Noschvie/shrdzm/hardware/19-12-22 15-27-47 3607.jpg

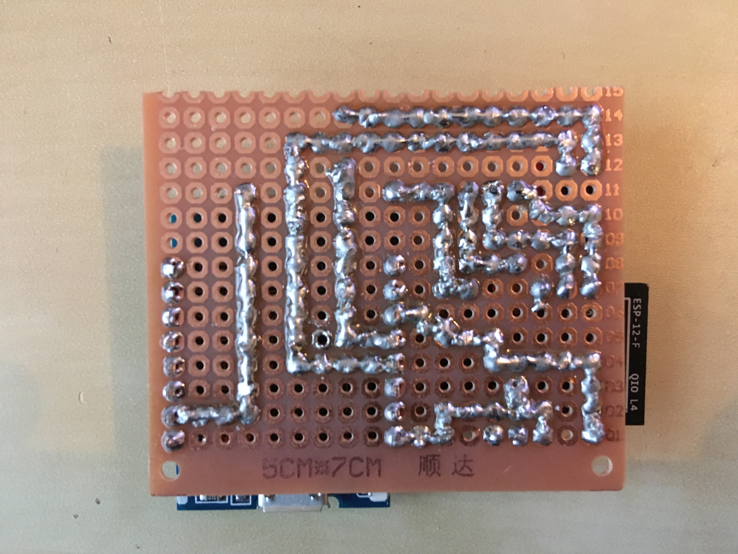
hardware/19-12-22 15-27-47 3607.jpg
