Noschvie/shrdzm/hardware/19-12-23 08-18-39 3610.jpg

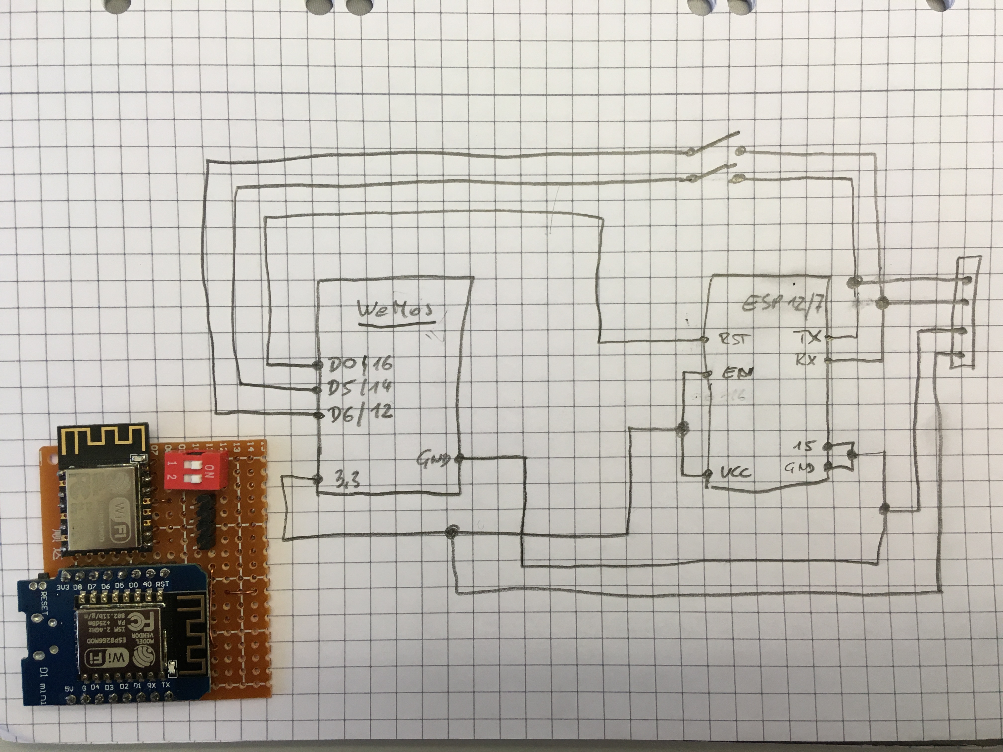
hardware/19-12-23 08-18-39 3610.jpg
