Noschvie/shrdzm/hardware/Alexa1.png

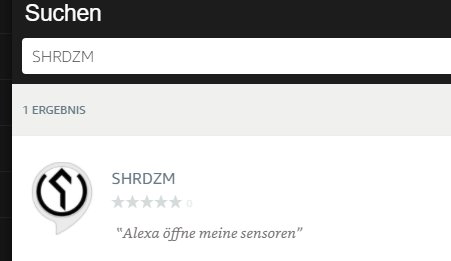
hardware/Alexa1.png
