Noschvie/shrdzm/hardware/Alexa5.png

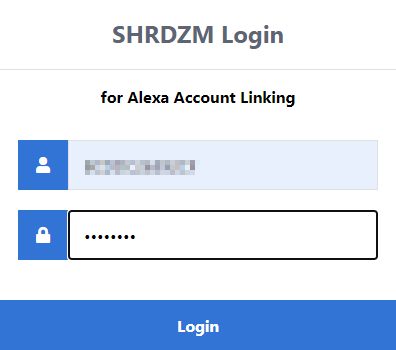
hardware/Alexa5.png
