Noschvie/shrdzm/hardware/Alexa6.png

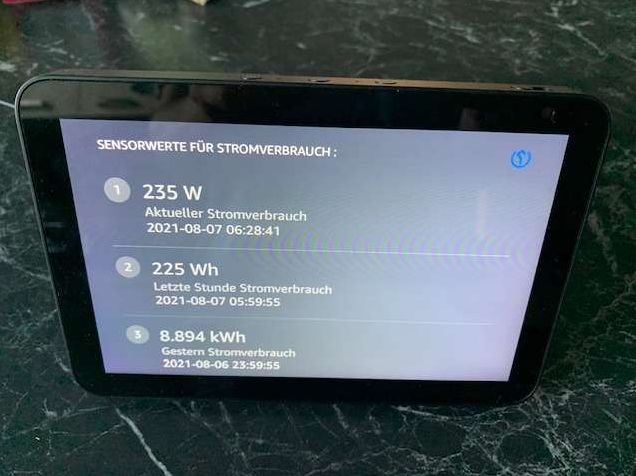
hardware/Alexa6.png
