Noschvie/shrdzm/hardware/Alexa7.png

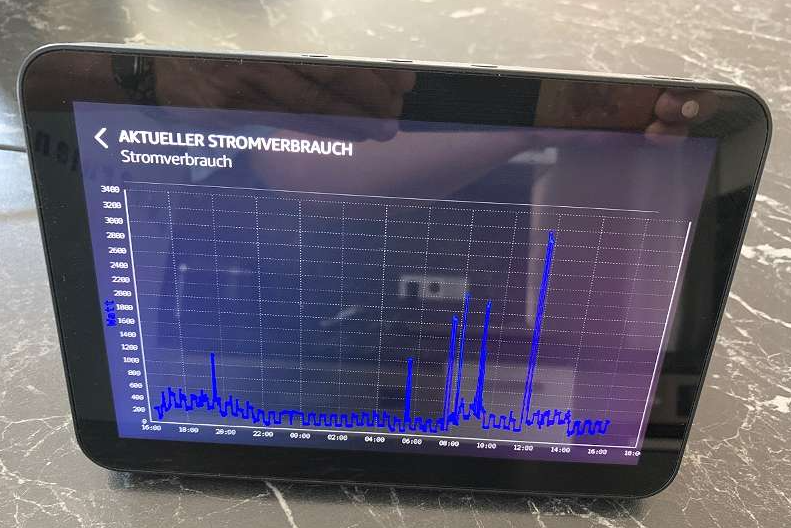
hardware/Alexa7.png
