Noschvie/shrdzm/hardware/AlexaConcept.png

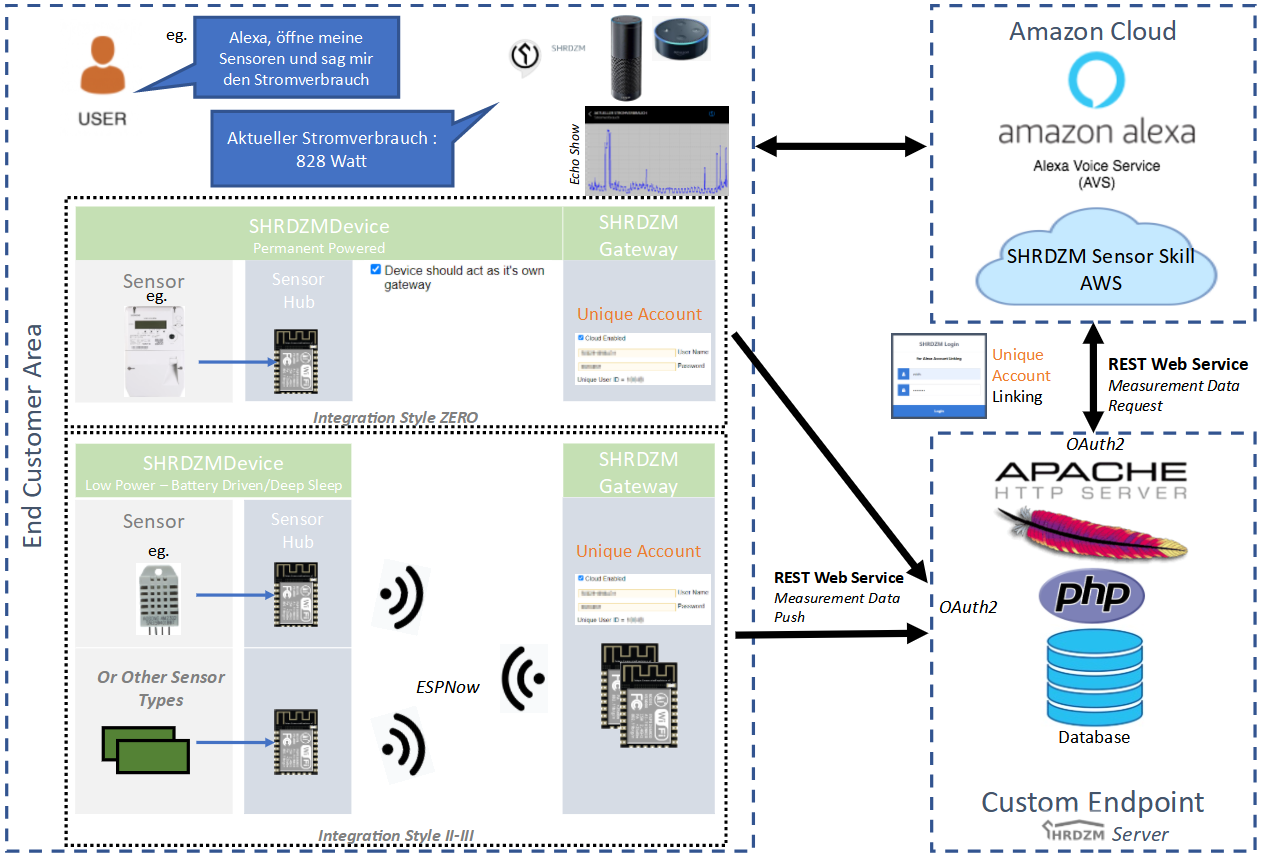
hardware/AlexaConcept.png
