Noschvie/shrdzm/hardware/BatteryCheck_1.png

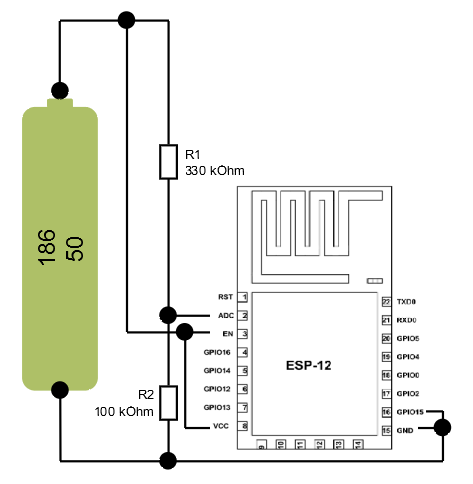
hardware/BatteryCheck_1.png
