Noschvie/shrdzm/hardware/BatteryCheck_4.png

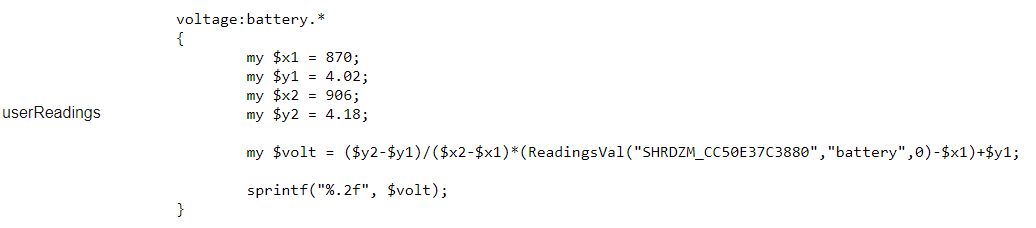
hardware/BatteryCheck_4.png
