Noschvie/shrdzm/hardware/BH1750.png

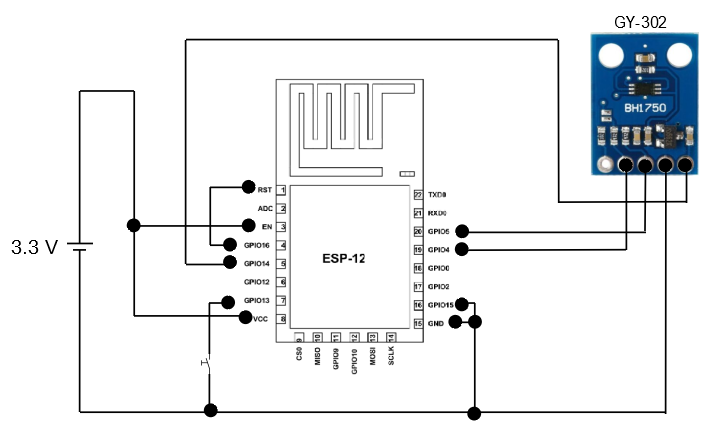
hardware/BH1750.png
