Noschvie/shrdzm/hardware/BMP280.png

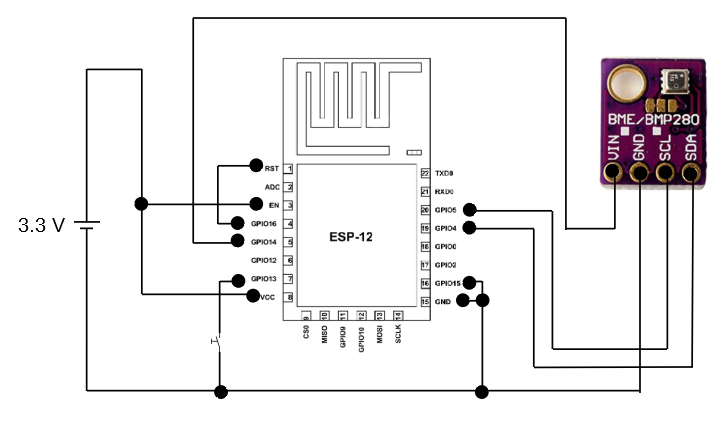
hardware/BMP280.png
