Noschvie/shrdzm/hardware/Breadboard.png

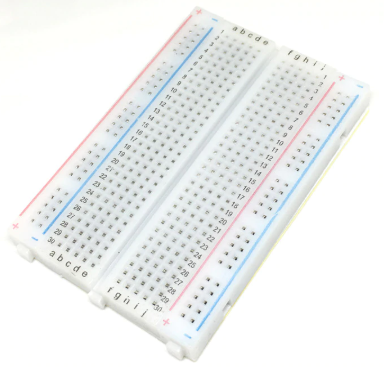
hardware/Breadboard.png
