Noschvie/shrdzm/hardware/CH340.png

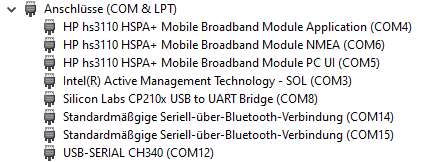
hardware/CH340.png
