Noschvie/shrdzm/hardware/Cloud1.png

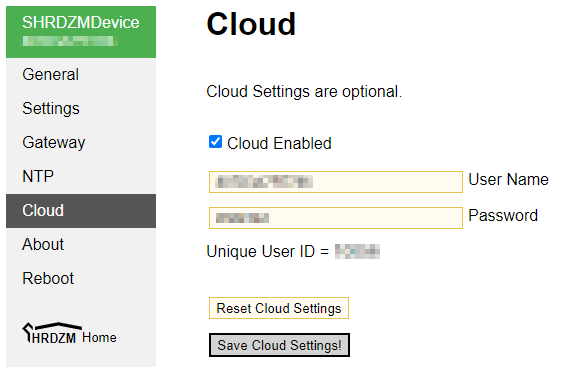
hardware/Cloud1.png
