Noschvie/shrdzm/hardware/Cloud2.png

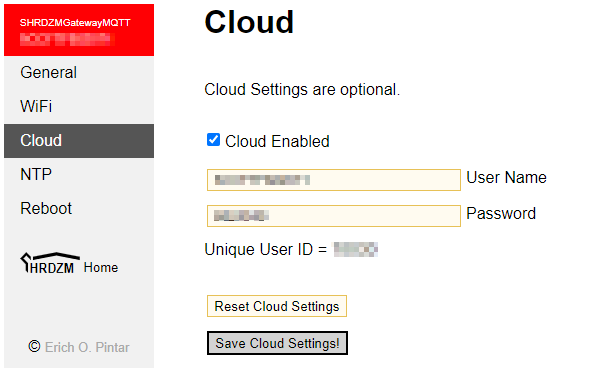
hardware/Cloud2.png
