Noschvie/shrdzm/hardware/Copyright.png

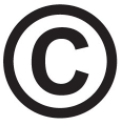
hardware/Copyright.png
