Noschvie/shrdzm/hardware/CP2102.png

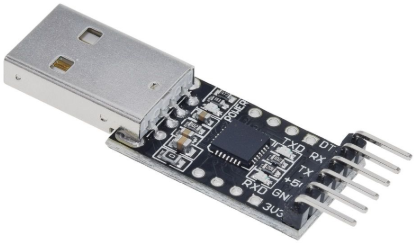
hardware/CP2102.png
