Noschvie/shrdzm/hardware/DeviceConfig.png

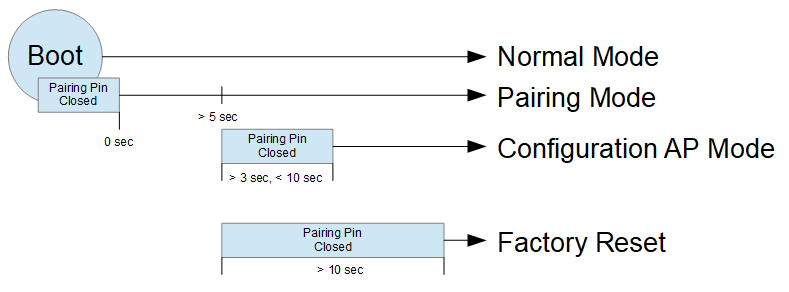
hardware/DeviceConfig.png
