Noschvie/shrdzm/hardware/DHT22.png

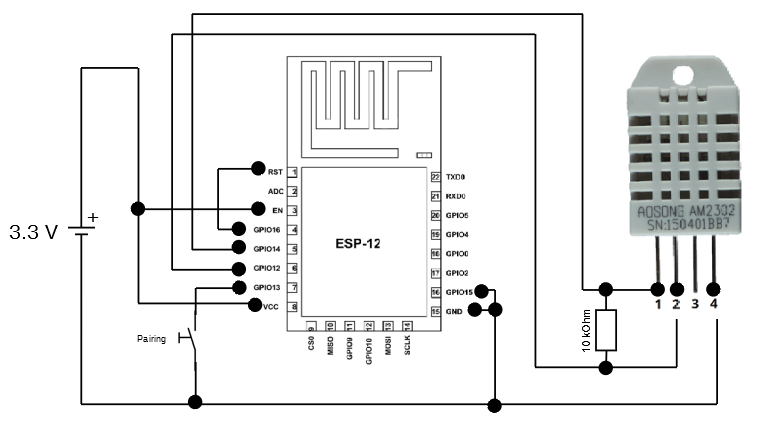
hardware/DHT22.png
