Noschvie/shrdzm/hardware/DOORSENSOR.png

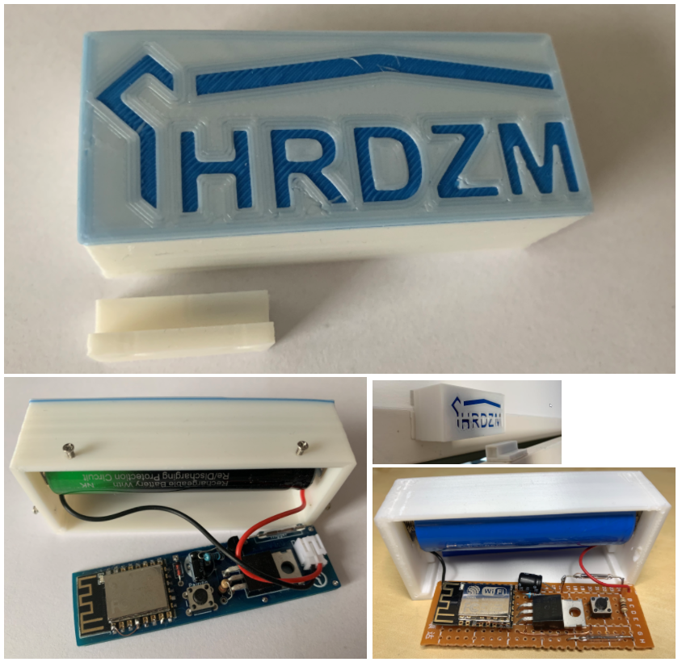
hardware/DOORSENSOR.png
