Noschvie/shrdzm/hardware/DOORSENSOR_1.png

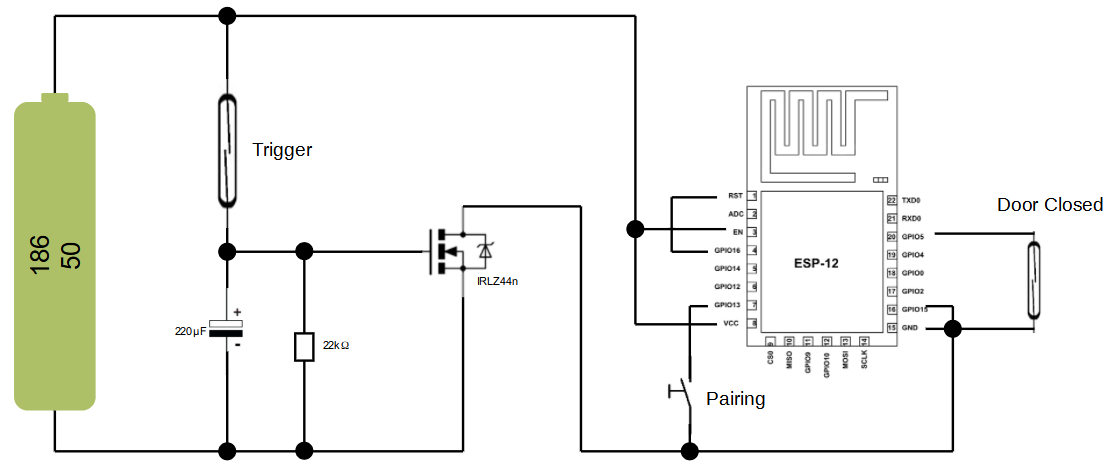
hardware/DOORSENSOR_1.png
