Noschvie/shrdzm/hardware/DOORSENSOR_9V_Cover.png

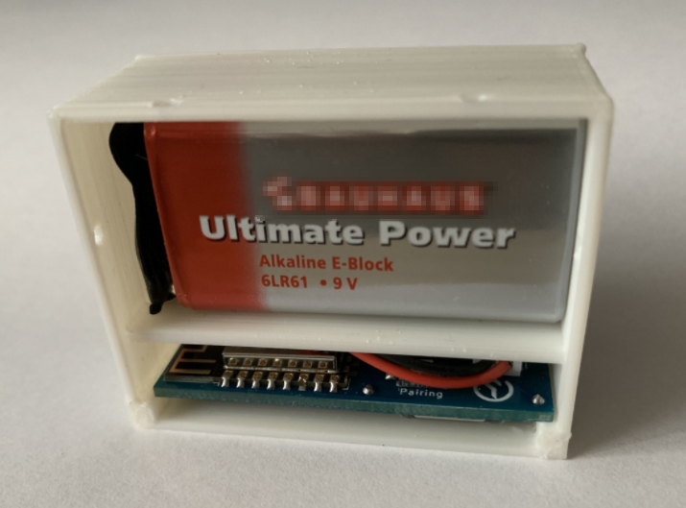
hardware/DOORSENSOR_9V_Cover.png
