Noschvie/shrdzm/hardware/DOORSENSOR_Closed.png

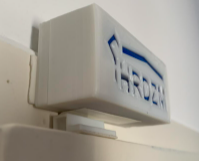
hardware/DOORSENSOR_Closed.png
