Noschvie/shrdzm/hardware/DOORSENSOR_Enhanced_Circuit.png

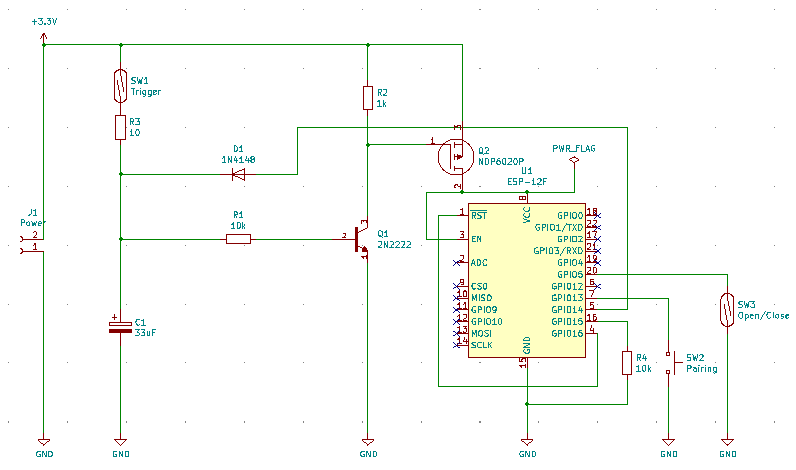
hardware/DOORSENSOR_Enhanced_Circuit.png
