Noschvie/shrdzm/hardware/DOORSENSOR_Enhanced_Cover.png

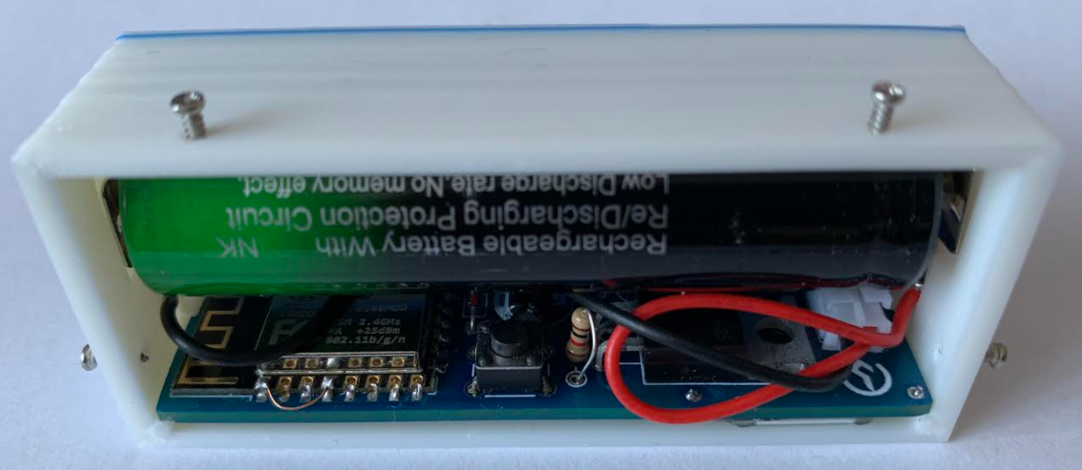
hardware/DOORSENSOR_Enhanced_Cover.png
