Noschvie/shrdzm/hardware/DOORSENSOR_Enhanced_PCB.png

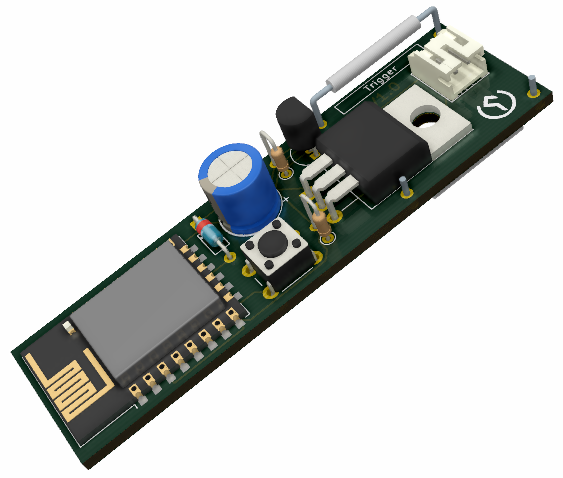
hardware/DOORSENSOR_Enhanced_PCB.png
