Noschvie/shrdzm/hardware/DOORSENSOR_FHEM.png

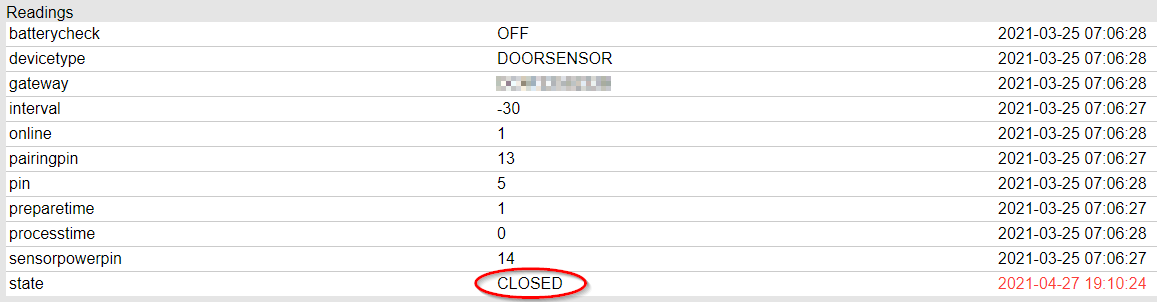
hardware/DOORSENSOR_FHEM.png
