Noschvie/shrdzm/hardware/DOORSENSOR_Open.png

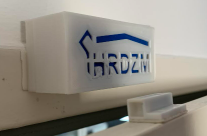
hardware/DOORSENSOR_Open.png
