Noschvie/shrdzm/hardware/DOORSENSOR_PCB.png

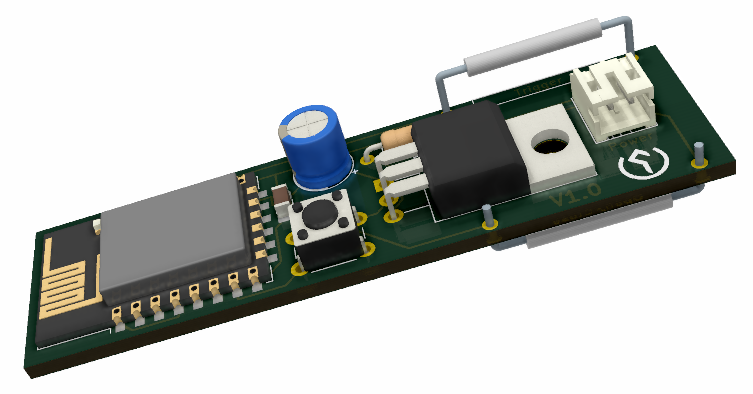
hardware/DOORSENSOR_PCB.png
