Noschvie/shrdzm/hardware/DOORSENSOR_Principle.png

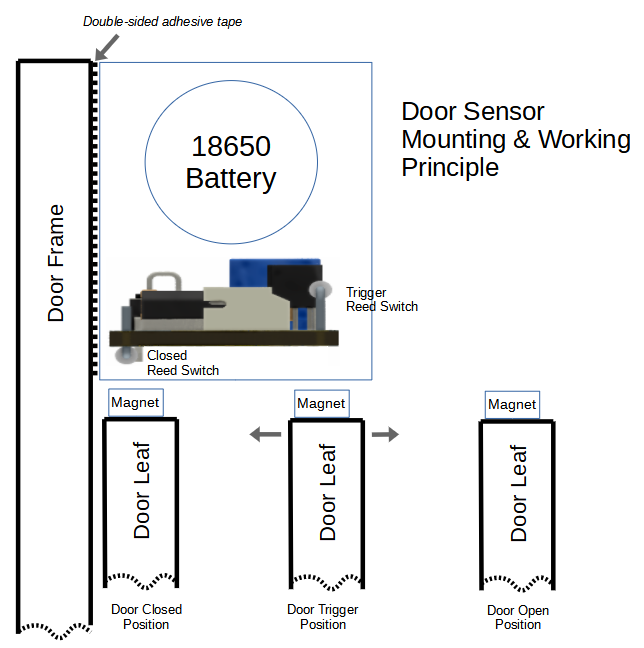
hardware/DOORSENSOR_Principle.png
