Noschvie/shrdzm/hardware/DOORSENSOR_Simple_9V_Circuit.png

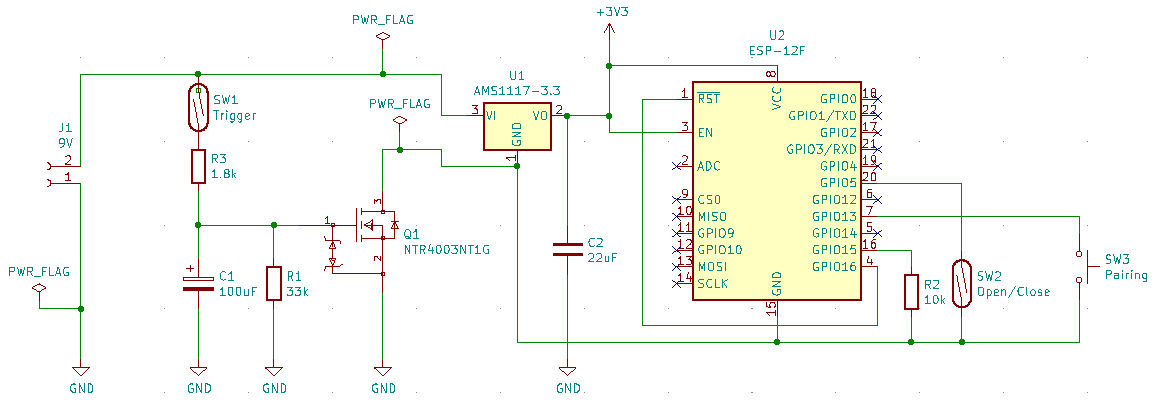
hardware/DOORSENSOR_Simple_9V_Circuit.png
