Noschvie/shrdzm/hardware/DOORSENSOR_Simple_9V_PCB.png

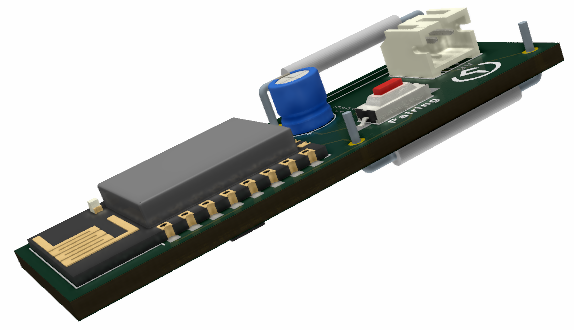
hardware/DOORSENSOR_Simple_9V_PCB.png
