Noschvie/shrdzm/hardware/DOORSENSOR_Trigger.png

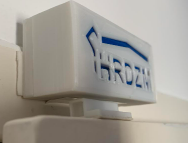
hardware/DOORSENSOR_Trigger.png
