Noschvie/shrdzm/hardware/DOORSENSOR_Unmounted.png

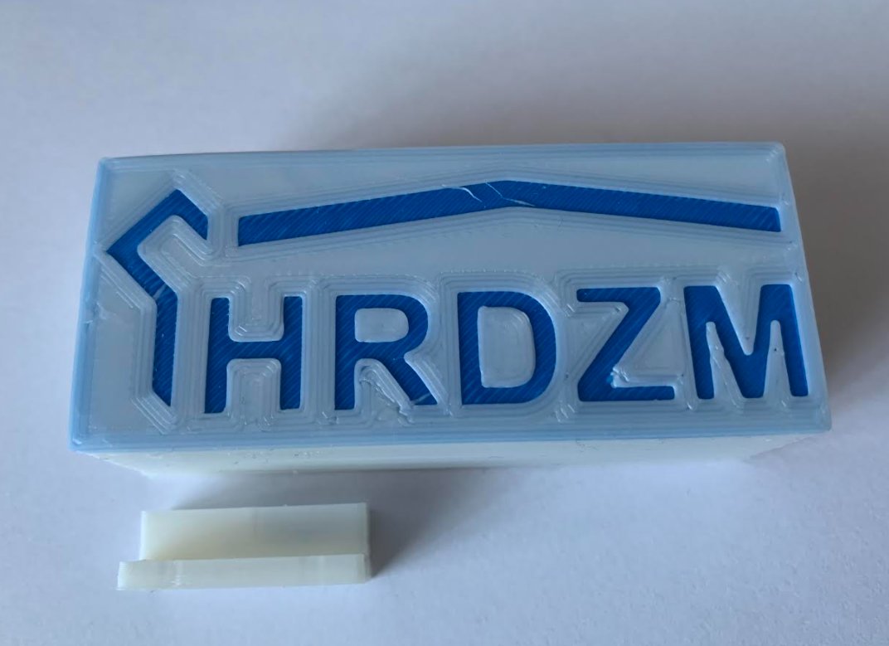
hardware/DOORSENSOR_Unmounted.png
