Noschvie/shrdzm/hardware/DS18B20.png

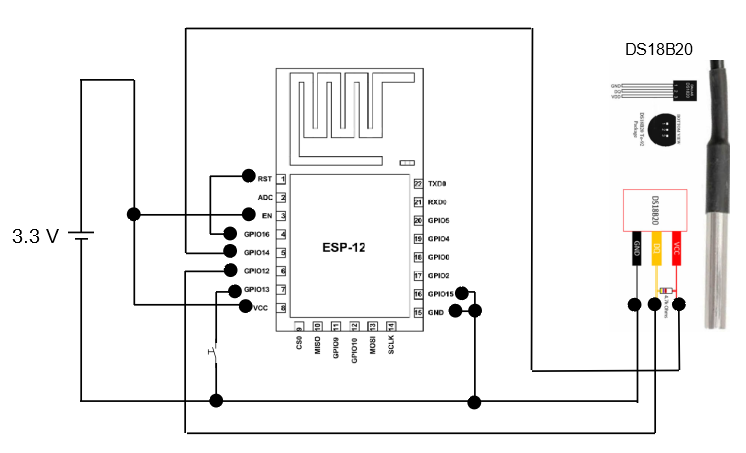
hardware/DS18B20.png
