Noschvie/shrdzm/hardware/ESP12.png

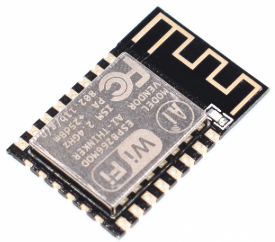
hardware/ESP12.png
