Noschvie/shrdzm/hardware/ESP8266Flasher_1.png

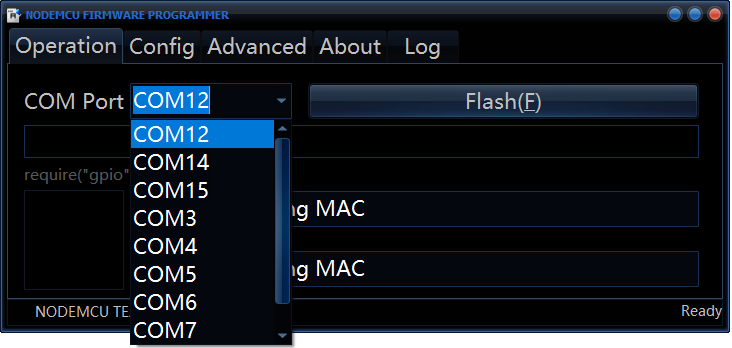
hardware/ESP8266Flasher_1.png
