Noschvie/shrdzm/hardware/ESP8266Flasher_2.png

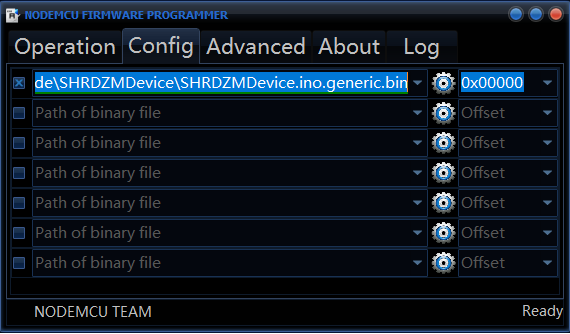
hardware/ESP8266Flasher_2.png
