Noschvie/shrdzm/hardware/ESP8266Flasher_2_1.png

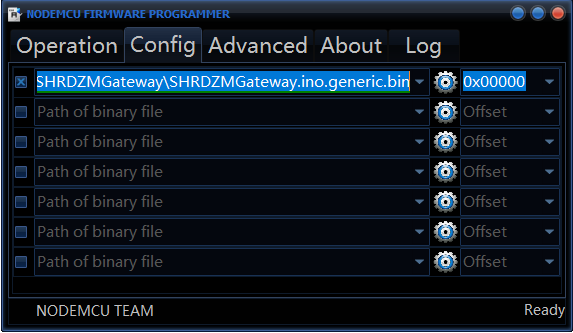
hardware/ESP8266Flasher_2_1.png
