Noschvie/shrdzm/hardware/ESP8266Flasher_3.png

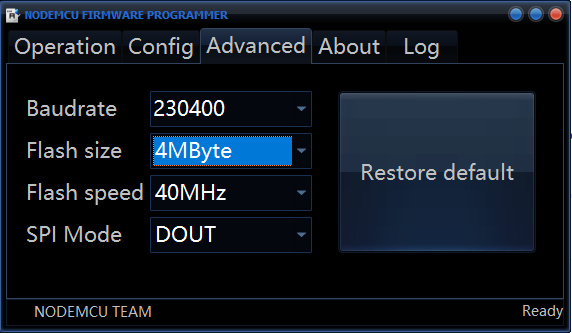
hardware/ESP8266Flasher_3.png
