Noschvie/shrdzm/hardware/ESP8266Flasher_3_1.png

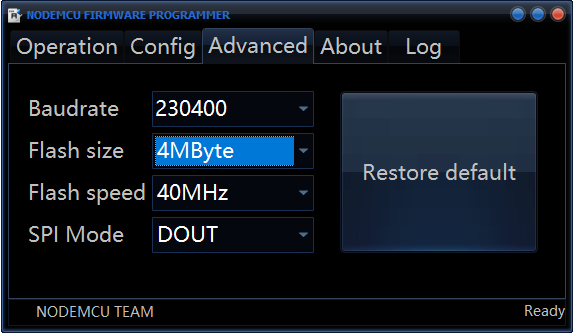
hardware/ESP8266Flasher_3_1.png
