Noschvie/shrdzm/hardware/ESP8266Flasher_4.png

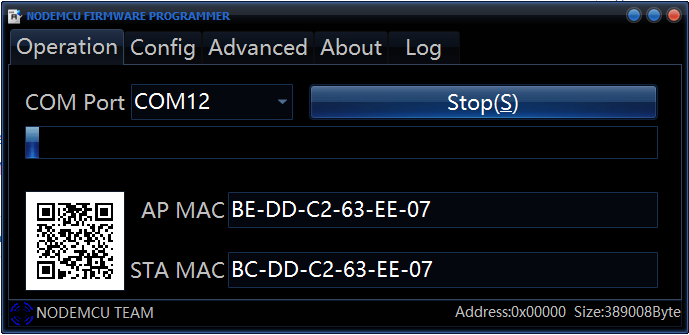
hardware/ESP8266Flasher_4.png
