Noschvie/shrdzm/hardware/ESP8266Flasher_5.png

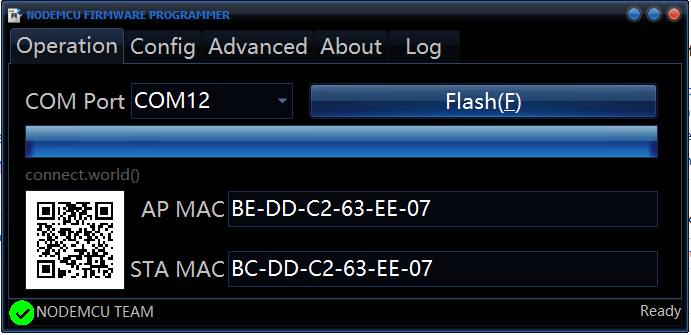
hardware/ESP8266Flasher_5.png
