Noschvie/shrdzm/hardware/ESP-07.png

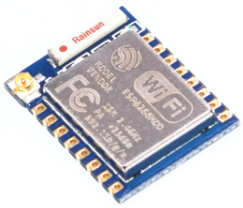
hardware/ESP-07.png
