Noschvie/shrdzm/hardware/ESPWLANGatewayAntennaHolder.png

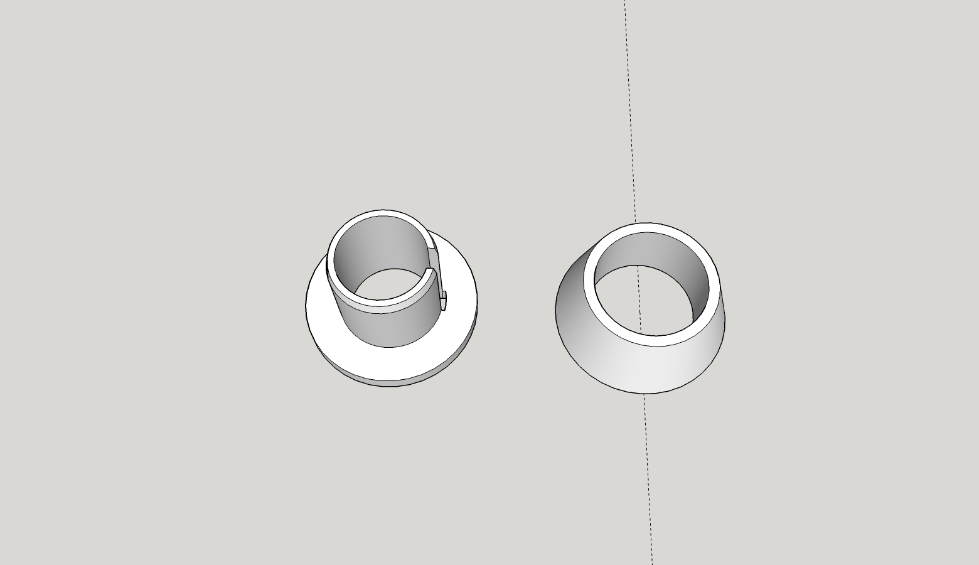
hardware/ESPWLANGatewayAntennaHolder.png
