Noschvie/shrdzm/hardware/ESPWLANGatewayBottom.png

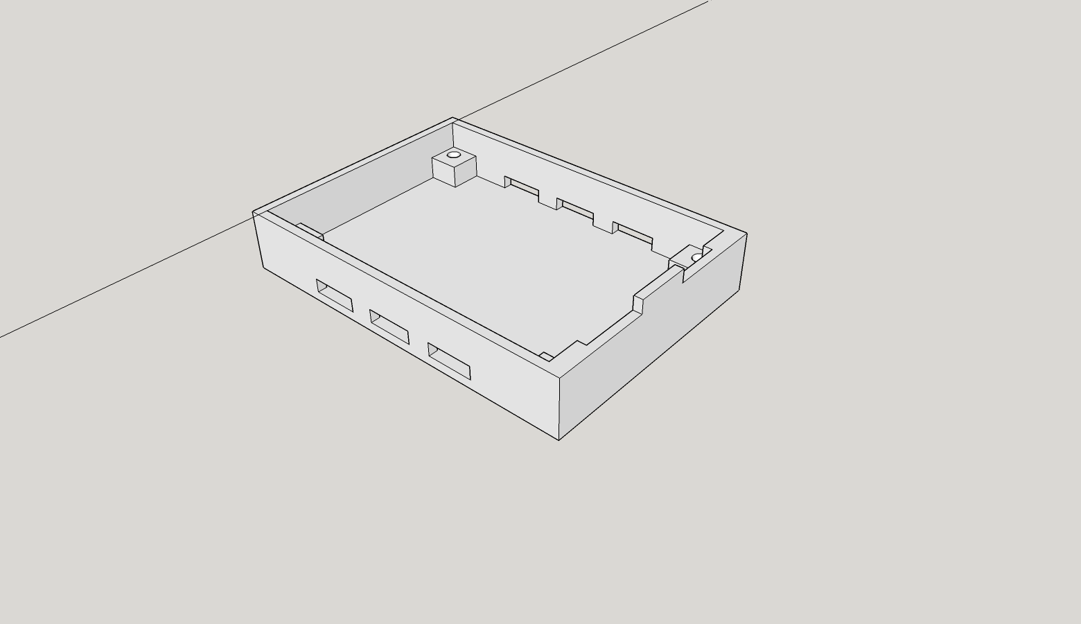
hardware/ESPWLANGatewayBottom.png
