Noschvie/shrdzm/hardware/ESPWLANGatewayTop.png

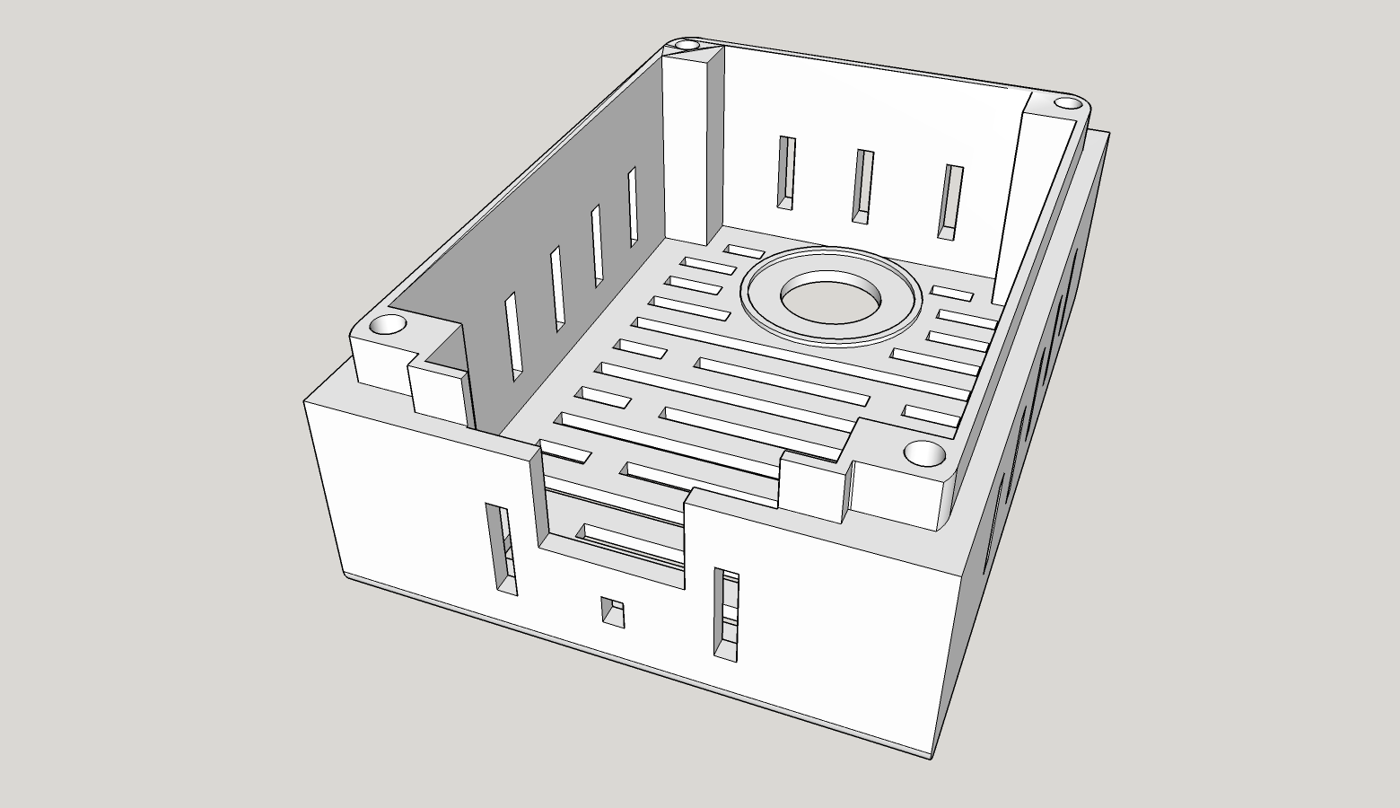
hardware/ESPWLANGatewayTop.png
