Noschvie/shrdzm/hardware/FHEM_definedMQTT.png

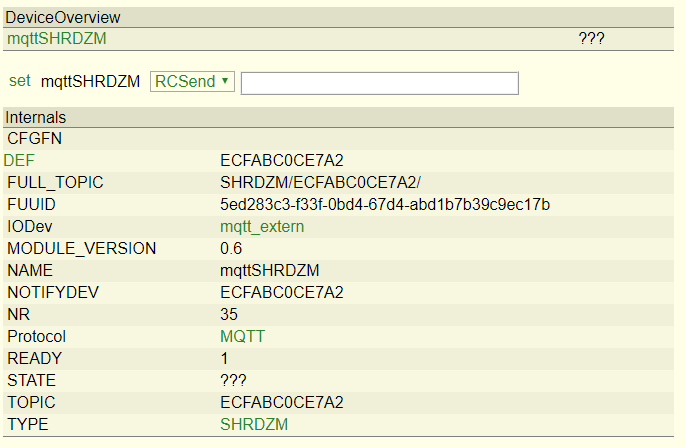
hardware/FHEM_definedMQTT.png
