Noschvie/shrdzm/hardware/FHEM_definedSerial.png

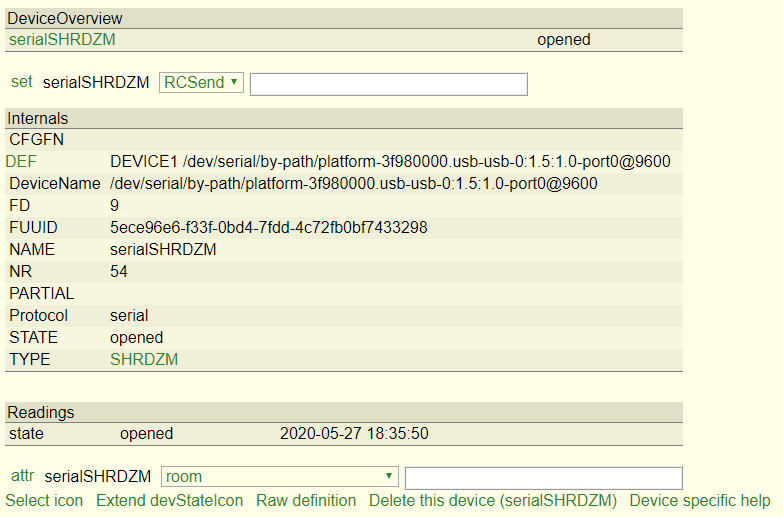
hardware/FHEM_definedSerial.png
