Noschvie/shrdzm/hardware/FHEM_DHT22_1.PNG

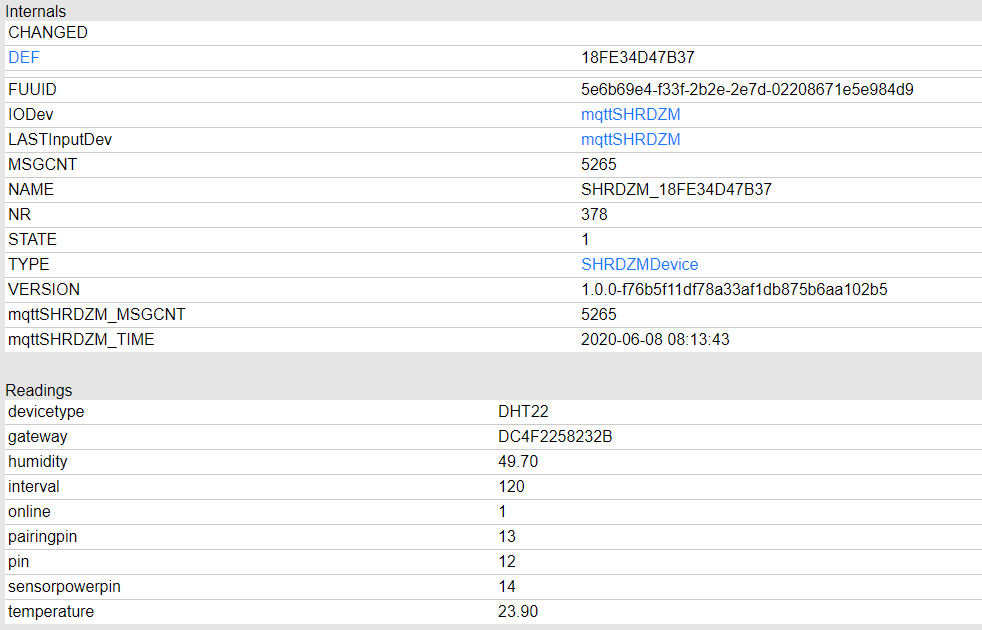
hardware/FHEM_DHT22_1.PNG
