Noschvie/shrdzm/hardware/FHEM_DIGITALGROUNDopen.png

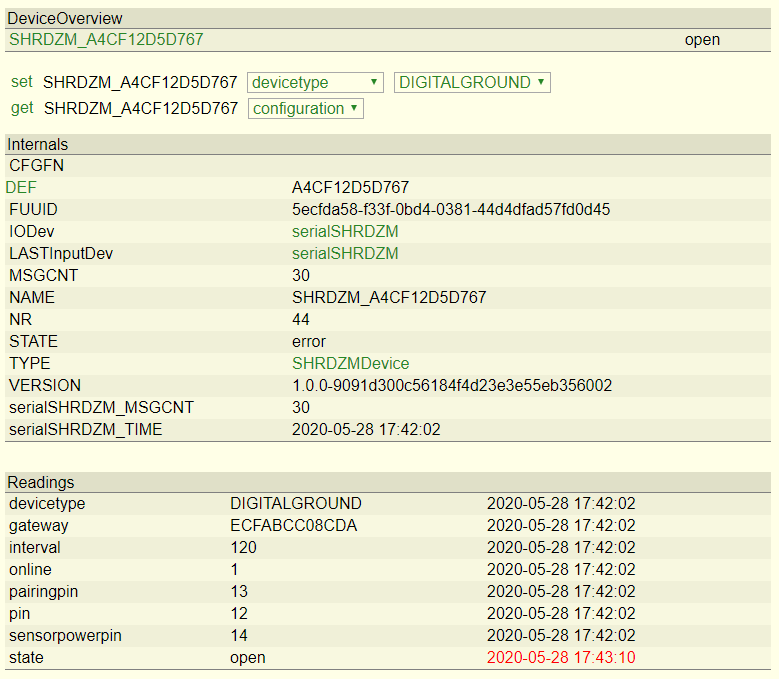
hardware/FHEM_DIGITALGROUNDopen.png
