Noschvie/shrdzm/hardware/FHEM_HTU21D_1.PNG

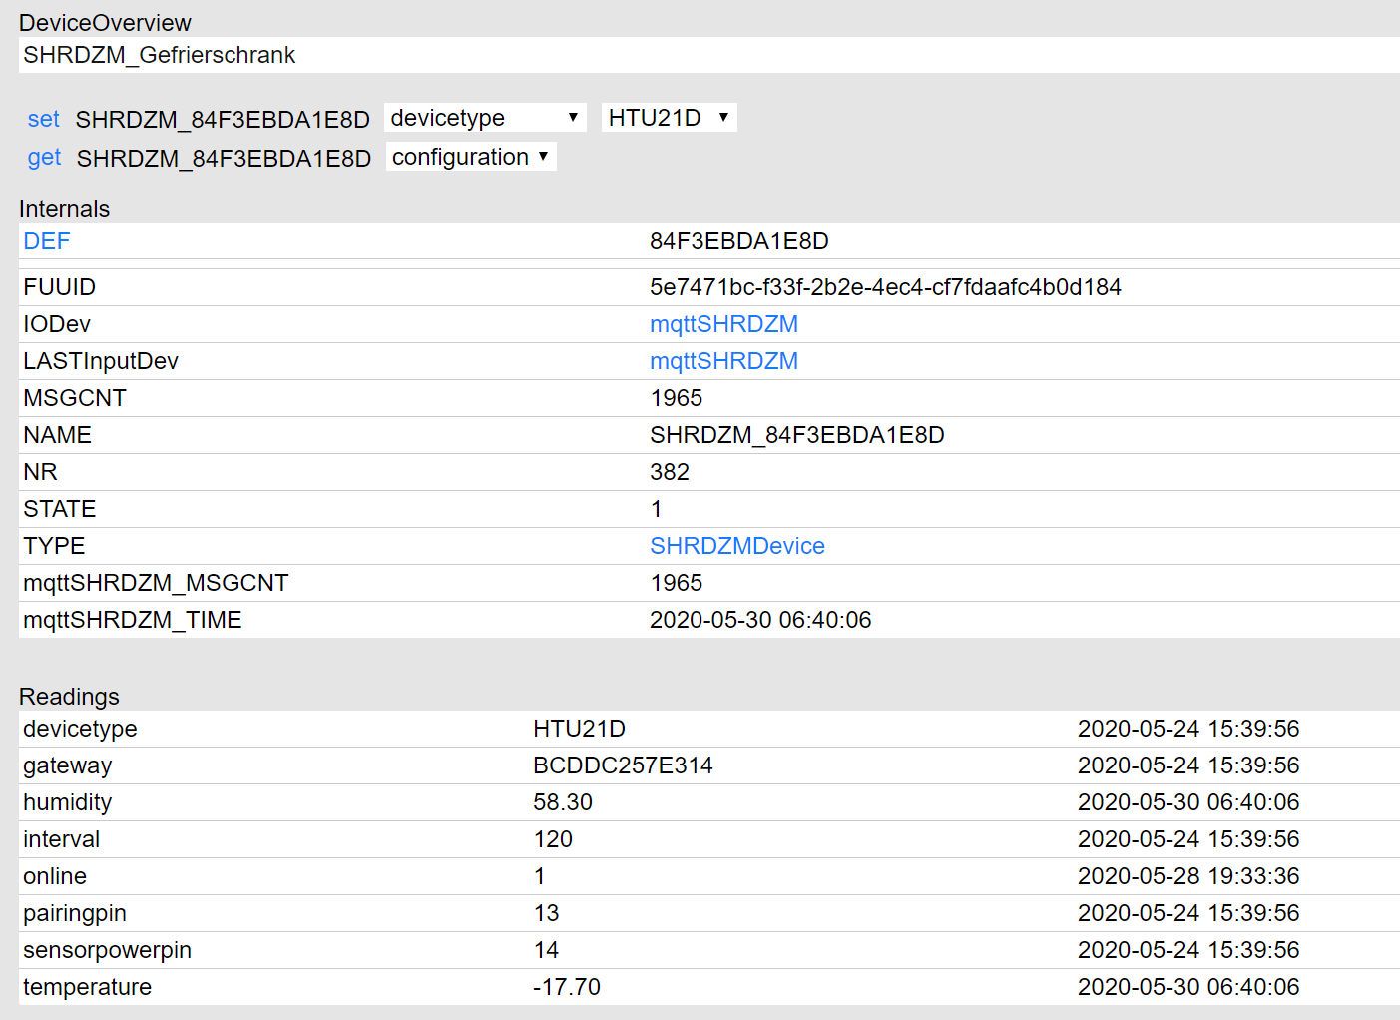
hardware/FHEM_HTU21D_1.PNG
