Noschvie/shrdzm/hardware/FHEM_HTU21D_2.PNG

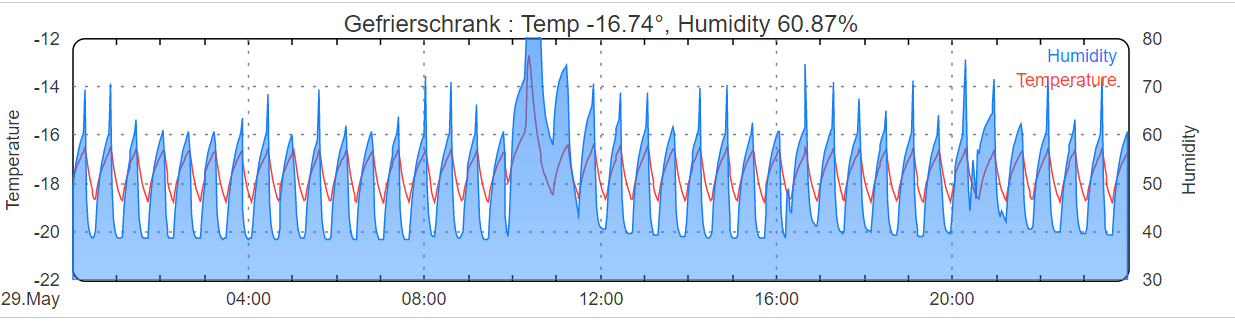
hardware/FHEM_HTU21D_2.PNG
