Noschvie/shrdzm/hardware/FHEM_IM350_2.png

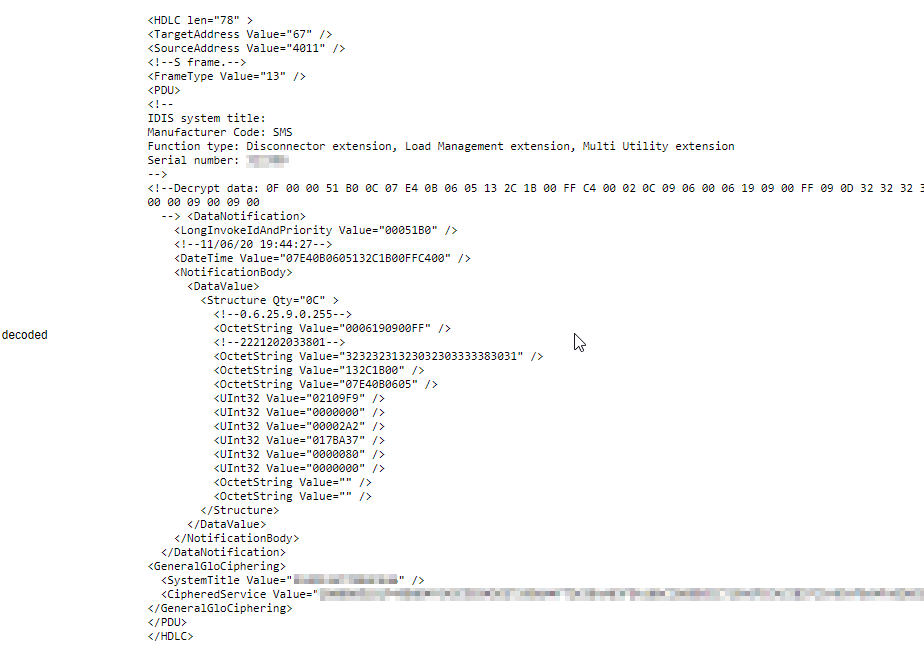
hardware/FHEM_IM350_2.png
