Noschvie/shrdzm/hardware/FHEM_IM350_3.png

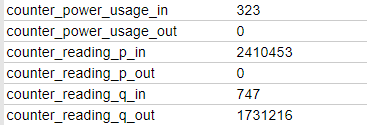
hardware/FHEM_IM350_3.png
