Noschvie/shrdzm/hardware/FHEM_IM350_4.png

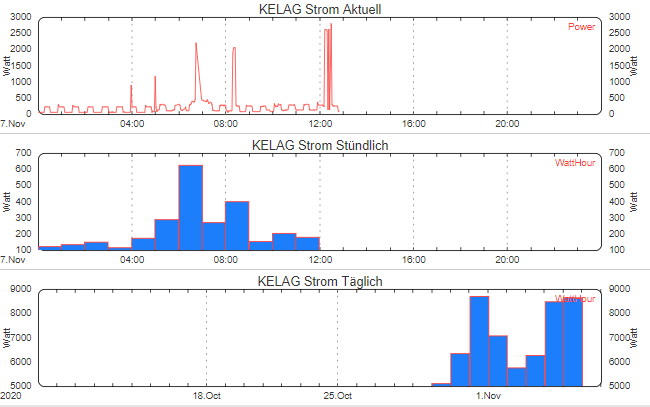
hardware/FHEM_IM350_4.png
