Noschvie/shrdzm/hardware/FHEM_PairedDone.png

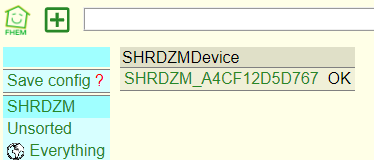
hardware/FHEM_PairedDone.png
