Noschvie/shrdzm/hardware/FHEM_SelectDIGITALGROUND.png

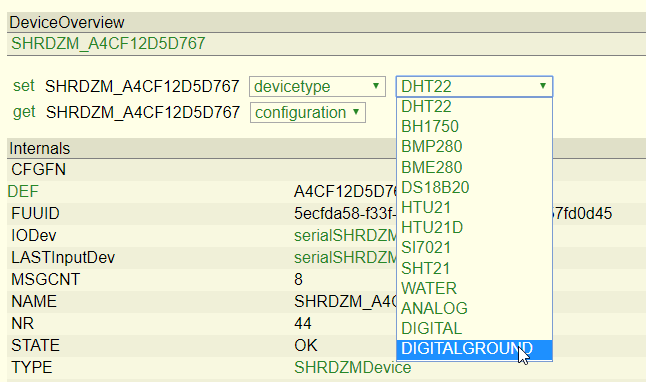
hardware/FHEM_SelectDIGITALGROUND.png
