Noschvie/shrdzm/hardware/FHEM_Sensors1.jpg

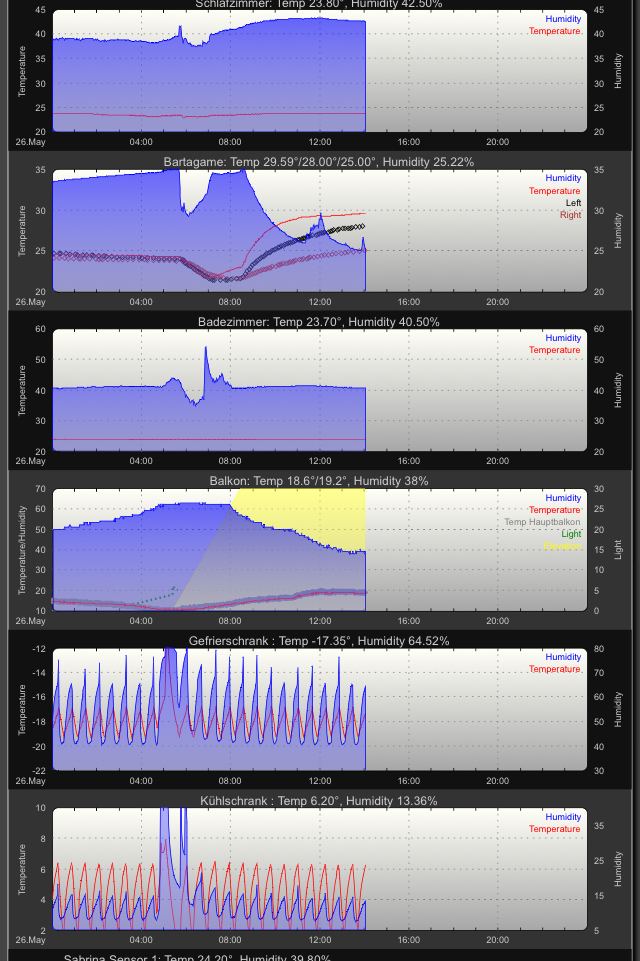
hardware/FHEM_Sensors1.jpg
