Noschvie/shrdzm/hardware/GatewaySettings.png

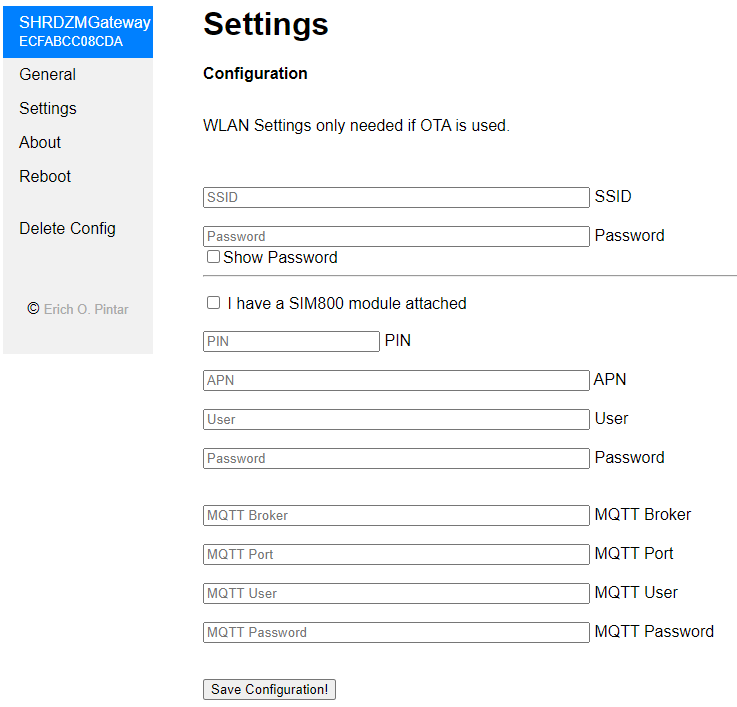
hardware/GatewaySettings.png
