Noschvie/shrdzm/hardware/GatewaySSID.png

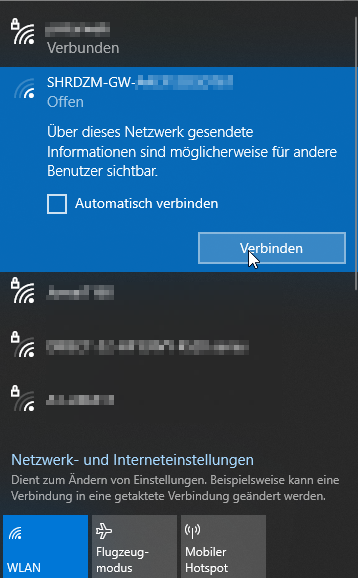
hardware/GatewaySSID.png
