Noschvie/shrdzm/hardware/Grafana_IM350.png

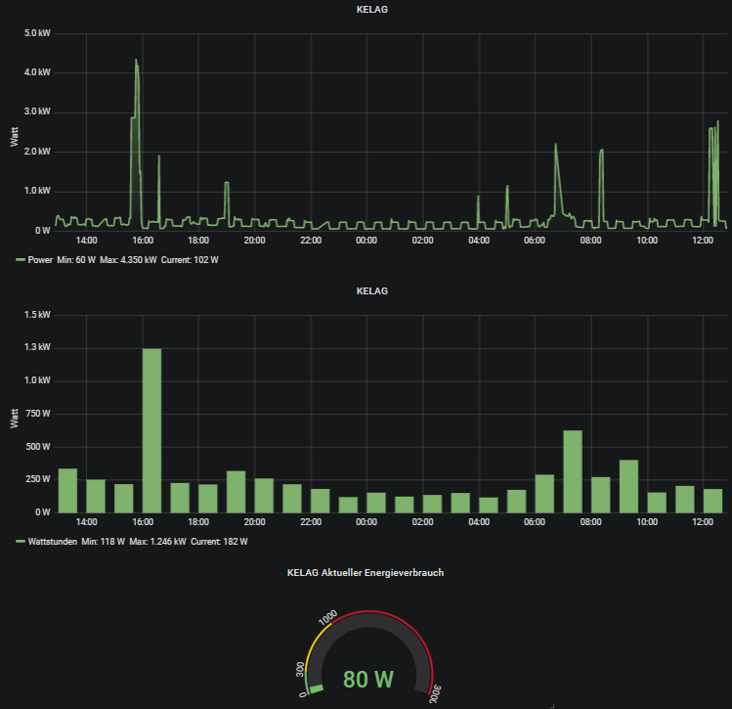
hardware/Grafana_IM350.png
