Noschvie/shrdzm/hardware/IM350.png

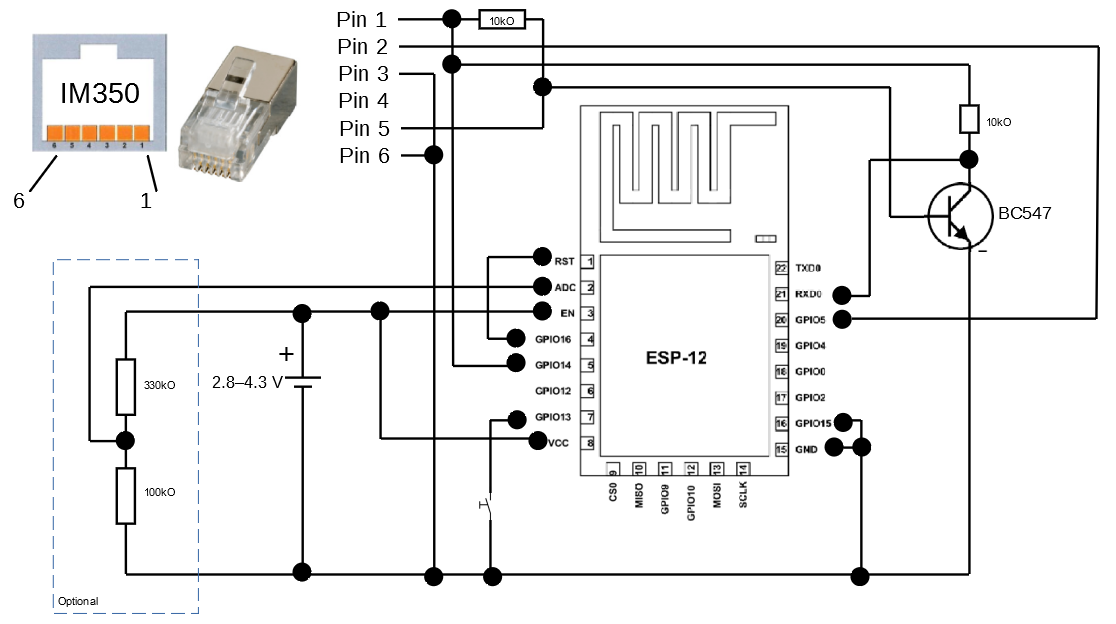
hardware/IM350.png
