Noschvie/shrdzm/hardware/IM350_1_Battery.png

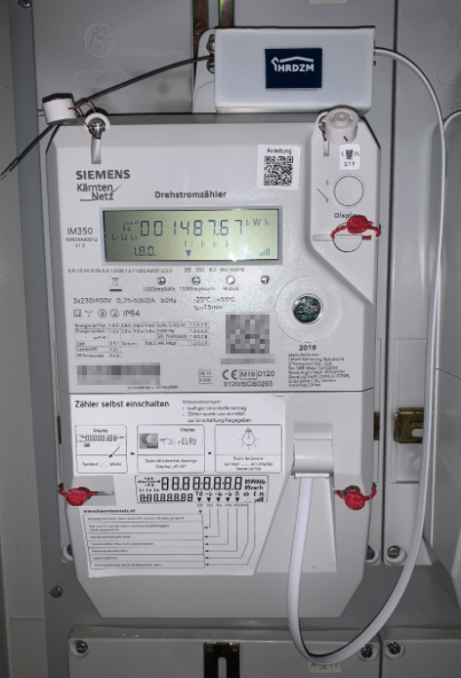
hardware/IM350_1_Battery.png
