Noschvie/shrdzm/hardware/IM350_2.png

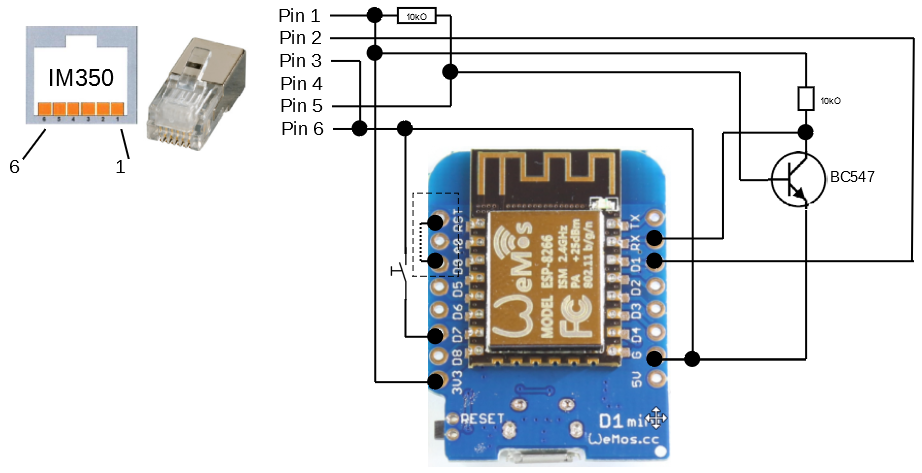
hardware/IM350_2.png
