Noschvie/shrdzm/hardware/IM350_2_SWInverter.png

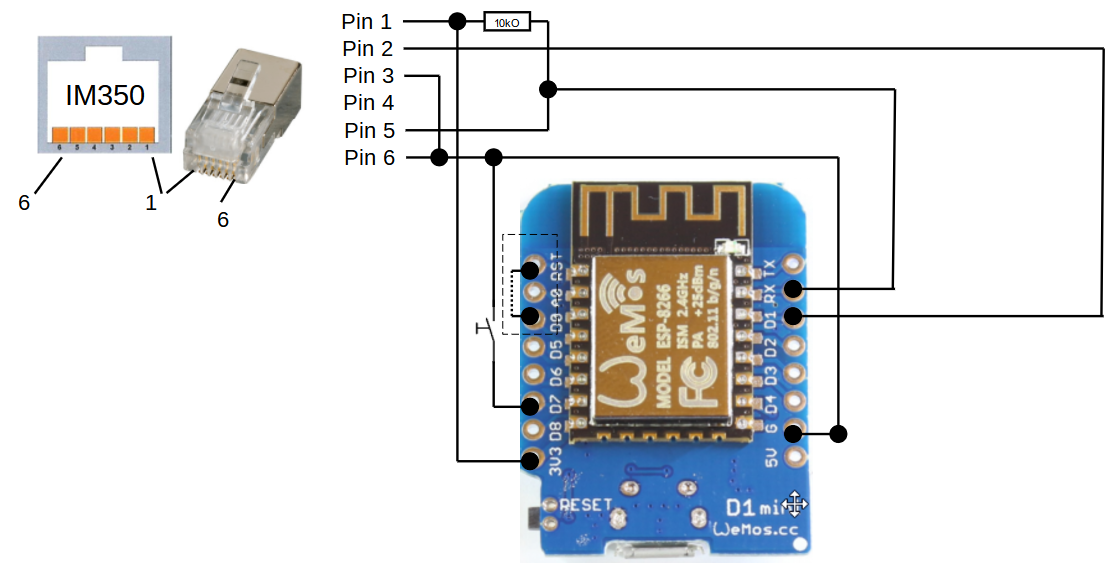
hardware/IM350_2_SWInverter.png
