Noschvie/shrdzm/hardware/IM350_3.png

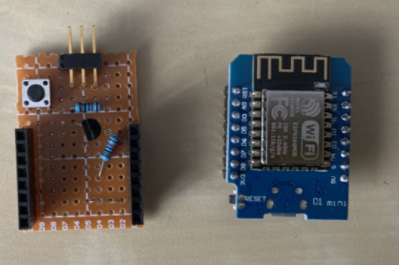
hardware/IM350_3.png
