Noschvie/shrdzm/hardware/IM350_4.png

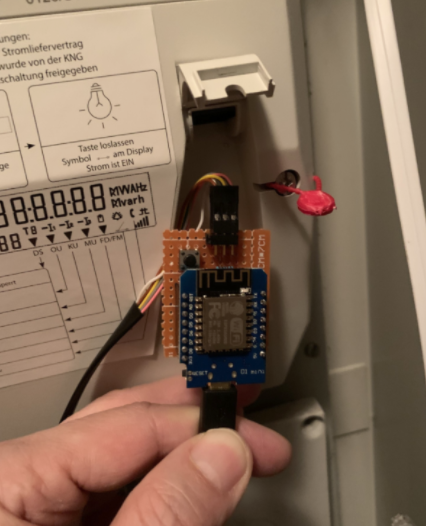
hardware/IM350_4.png
