Noschvie/shrdzm/hardware/IM350_PCB.png

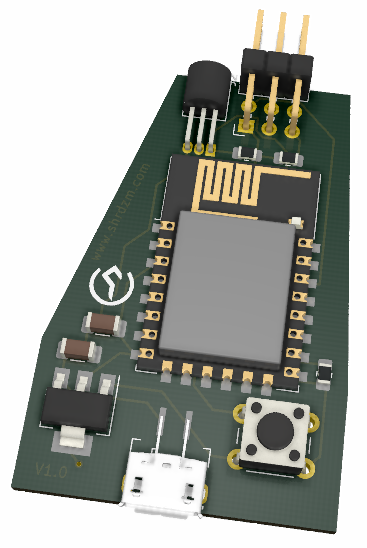
hardware/IM350_PCB.png
