Noschvie/shrdzm/hardware/IM350_PCB_Battery.png

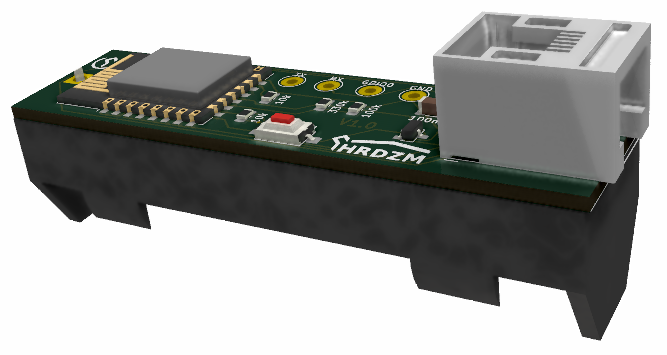
hardware/IM350_PCB_Battery.png
