Noschvie/shrdzm/hardware/IM350_PCB_Mini.png

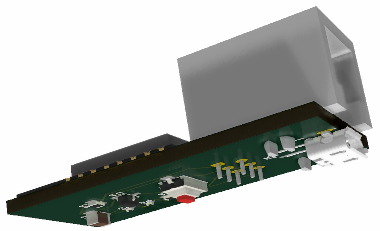
hardware/IM350_PCB_Mini.png
