Noschvie/shrdzm/hardware/IM350_PCB_Standard.png

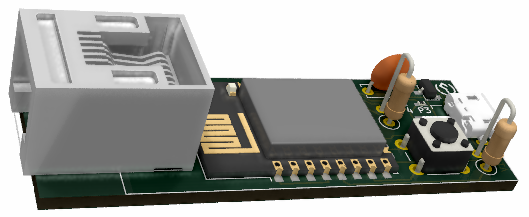
hardware/IM350_PCB_Standard.png
