Noschvie/shrdzm/hardware/IM350_S1.png

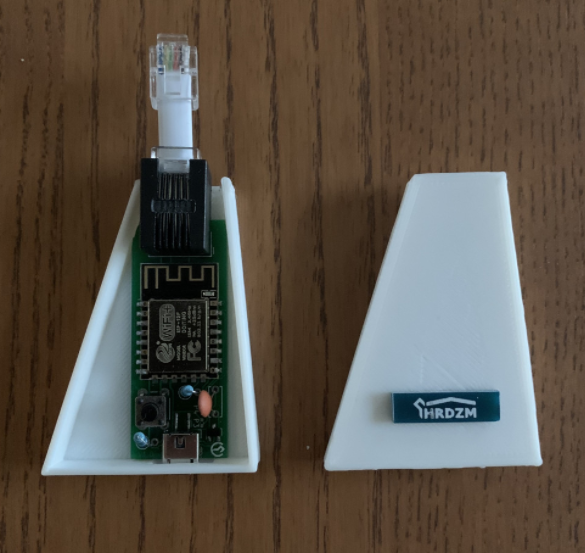
hardware/IM350_S1.png
