Noschvie/shrdzm/hardware/IM350_S2.png

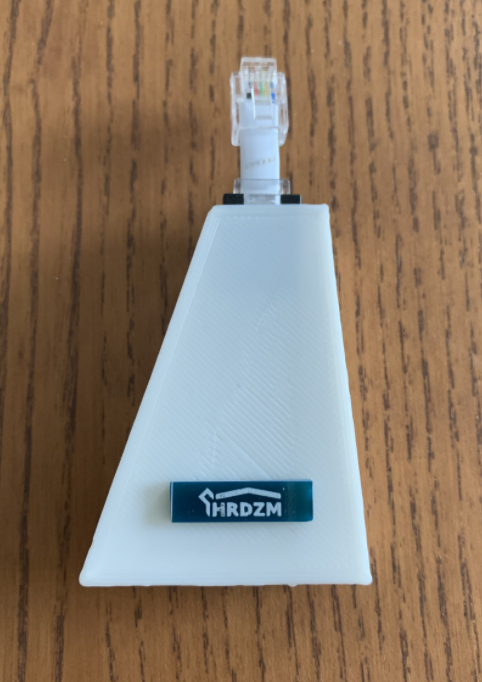
hardware/IM350_S2.png
