Noschvie/shrdzm/hardware/IM350_S3.png

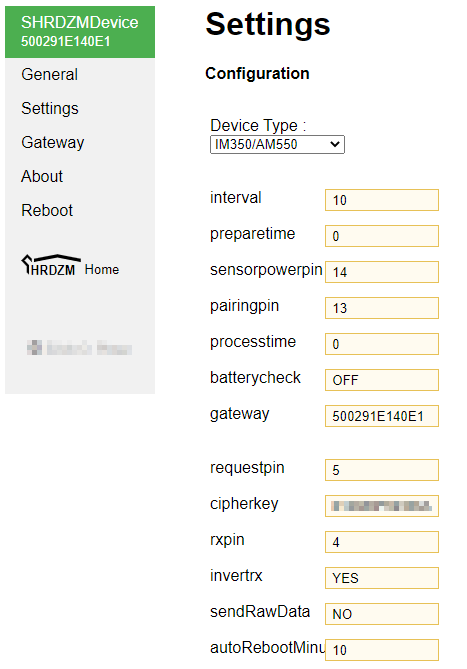
hardware/IM350_S3.png
