Noschvie/shrdzm/hardware/IM350_S4.png

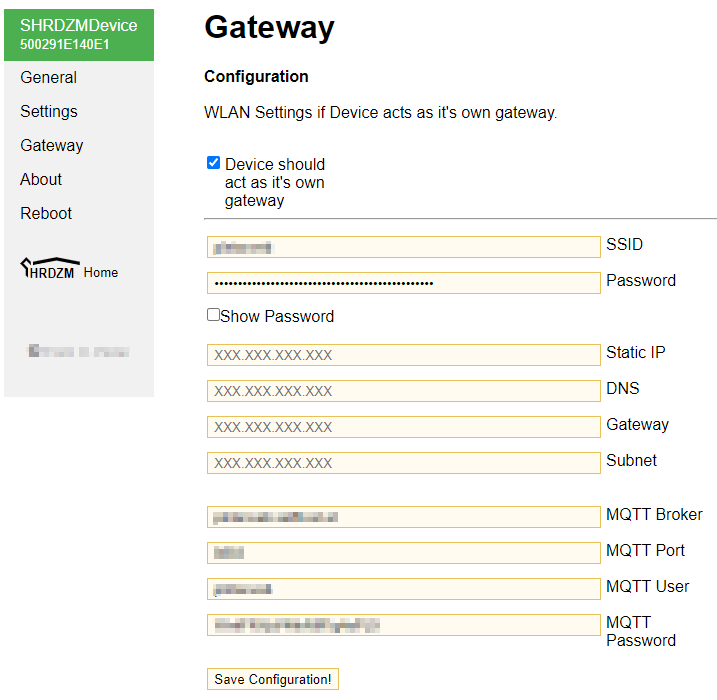
hardware/IM350_S4.png
