Noschvie/shrdzm/hardware/IM350_S5.png

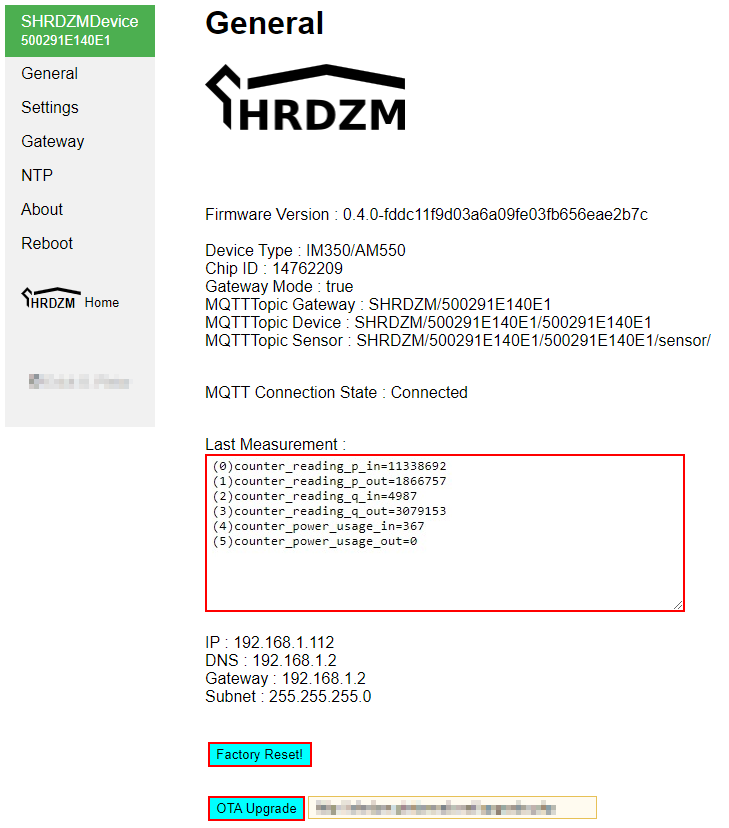
hardware/IM350_S5.png
