Noschvie/shrdzm/hardware/IM350_SWInverter.png

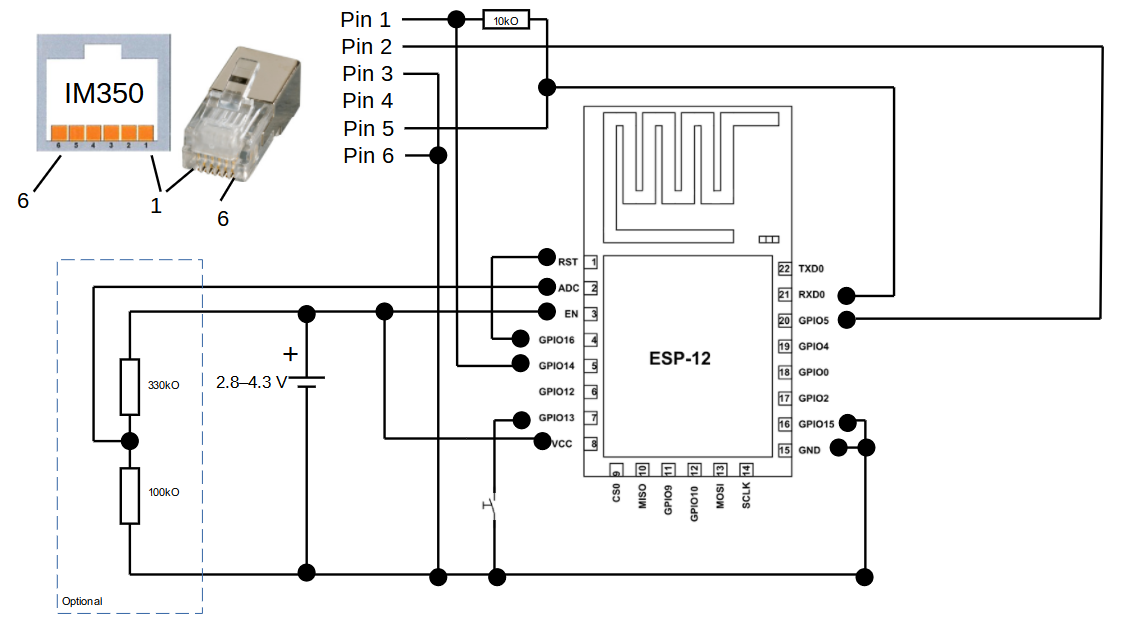
hardware/IM350_SWInverter.png
