Noschvie/shrdzm/hardware/IM350_SWInvertNO.png

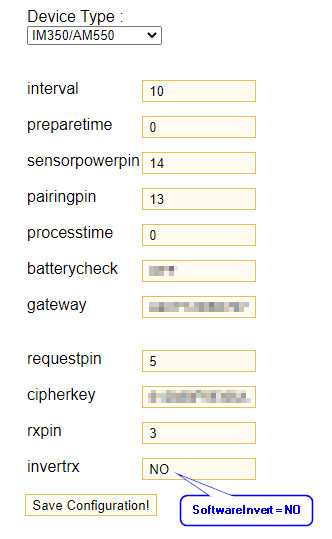
hardware/IM350_SWInvertNO.png
