Noschvie/shrdzm/hardware/IM350_SWInvertYES.png

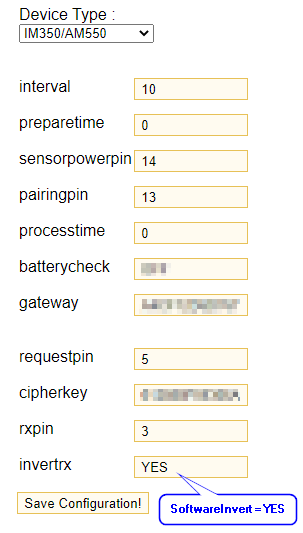
hardware/IM350_SWInvertYES.png
