Noschvie/shrdzm/hardware/IMG_3999.JPG

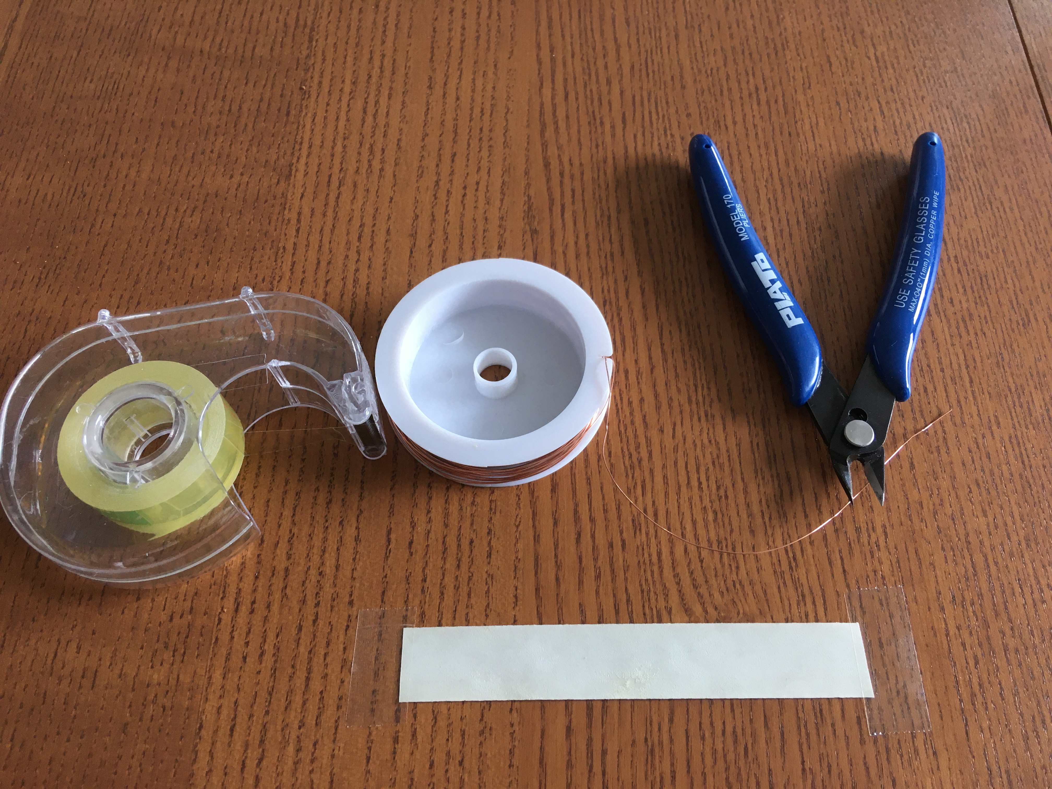
hardware/IMG_3999.JPG
