Noschvie/shrdzm/hardware/IMG_4001.JPG

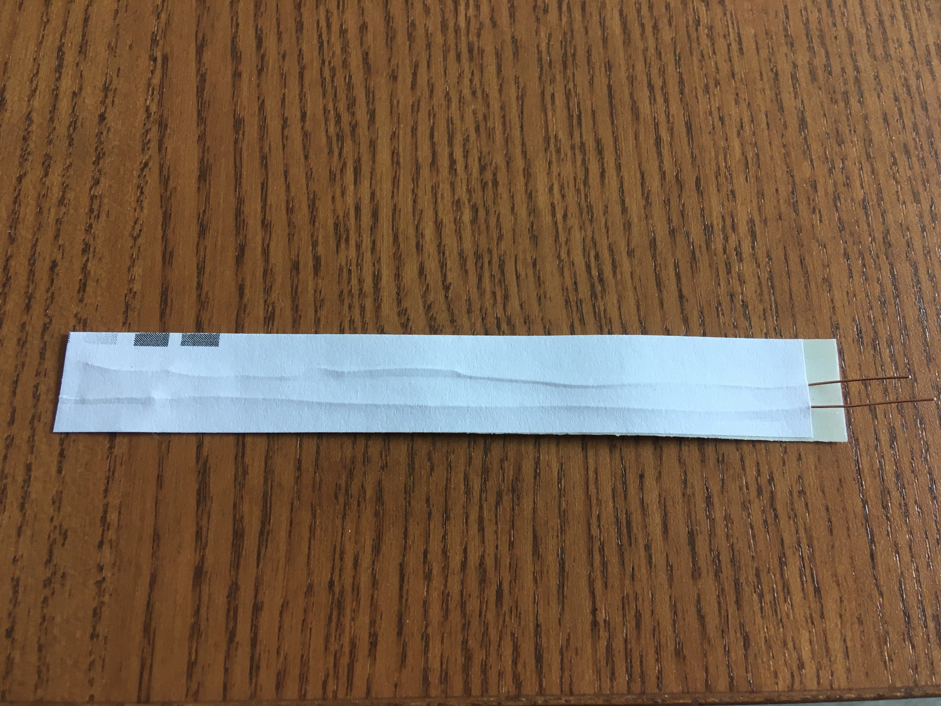
hardware/IMG_4001.JPG
