Noschvie/shrdzm/hardware/IMG_4002.JPG

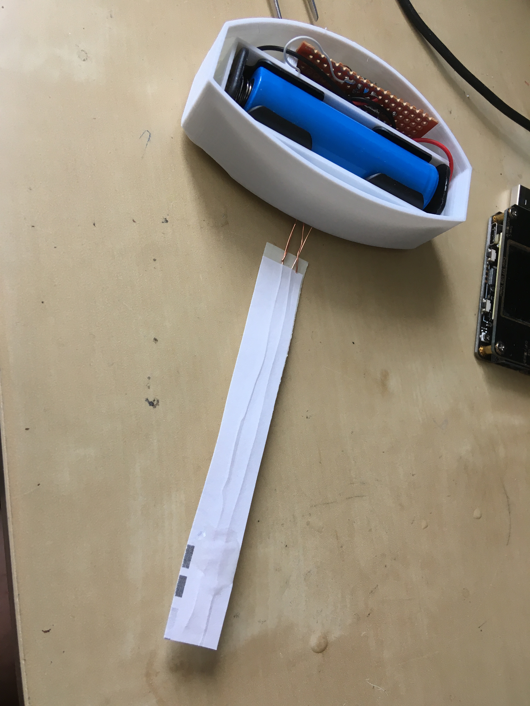
hardware/IMG_4002.JPG
