Noschvie/shrdzm/hardware/IMG_4003.JPG

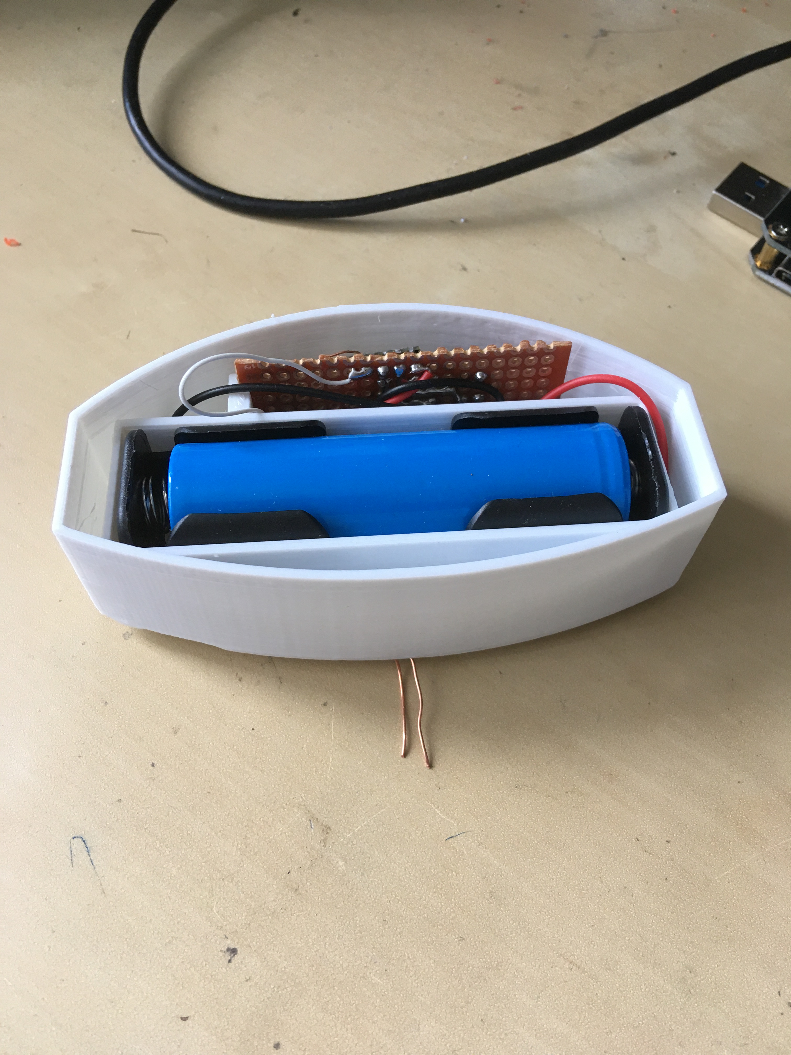
hardware/IMG_4003.JPG
