Noschvie/shrdzm/hardware/IMG_4005.JPG

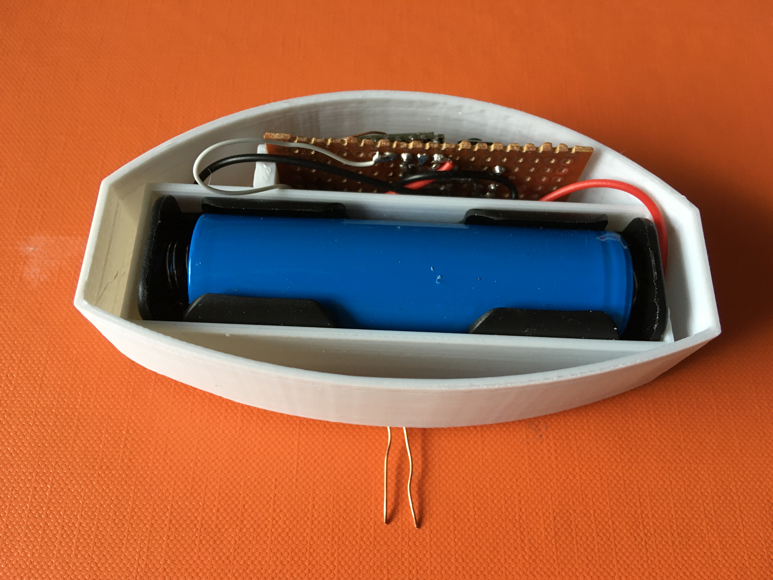
hardware/IMG_4005.JPG
