Noschvie/shrdzm/hardware/IMG_4006.JPG

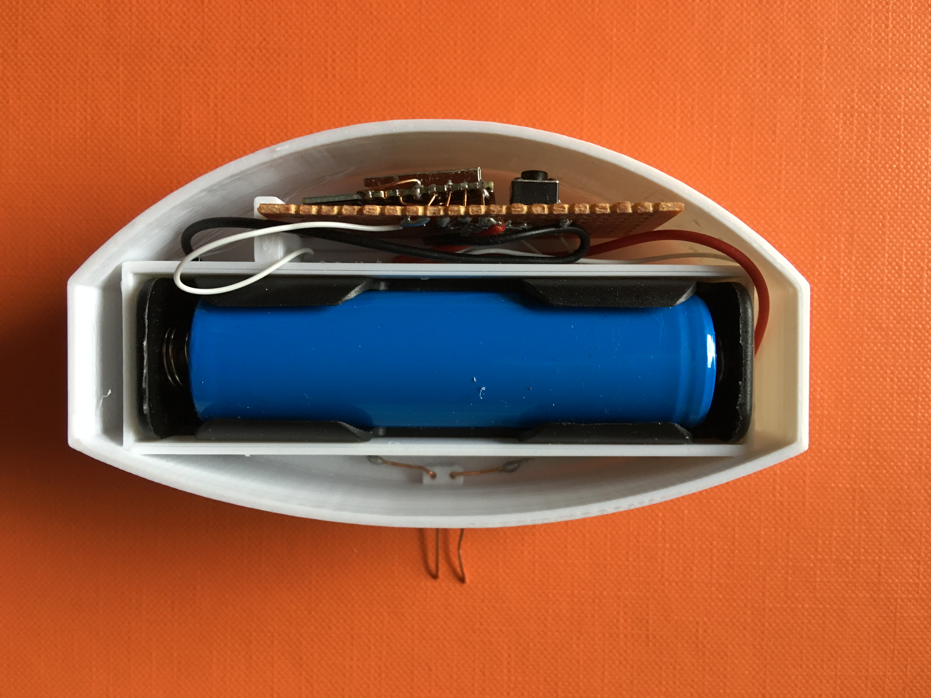
hardware/IMG_4006.JPG
