Noschvie/shrdzm/hardware/IMG_4007.JPG

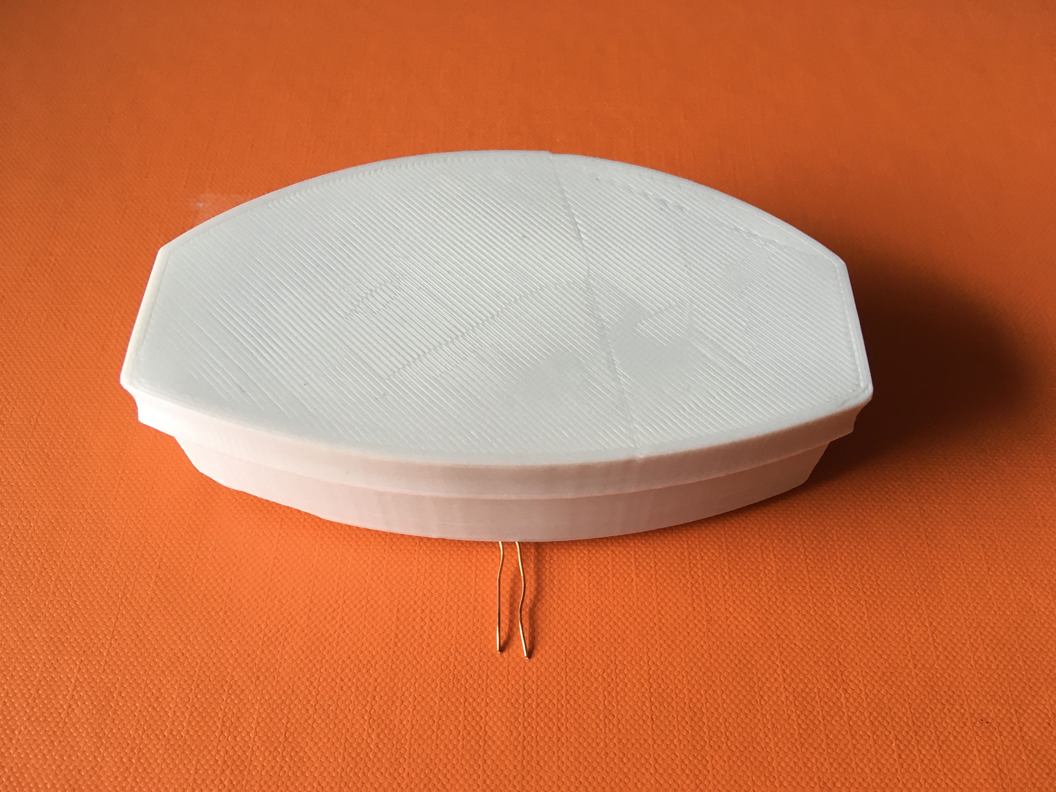
hardware/IMG_4007.JPG
