Noschvie/shrdzm/hardware/IMG_4008.JPG

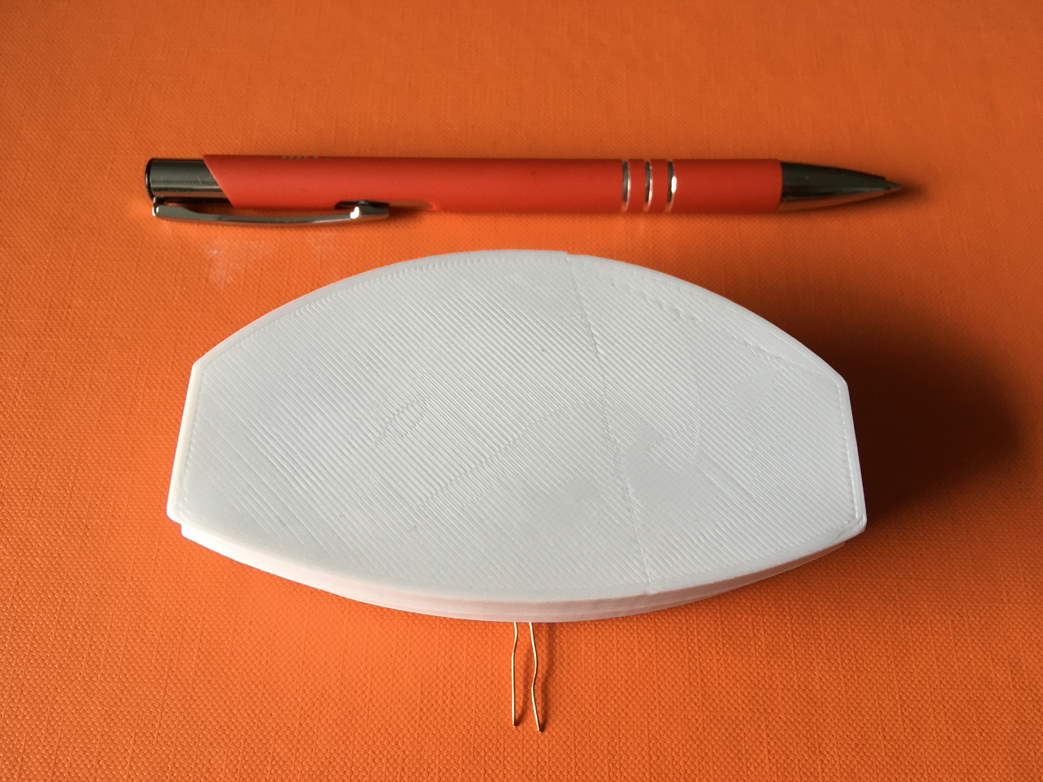
hardware/IMG_4008.JPG
