Noschvie/shrdzm/hardware/IntegrationStyle_1.png

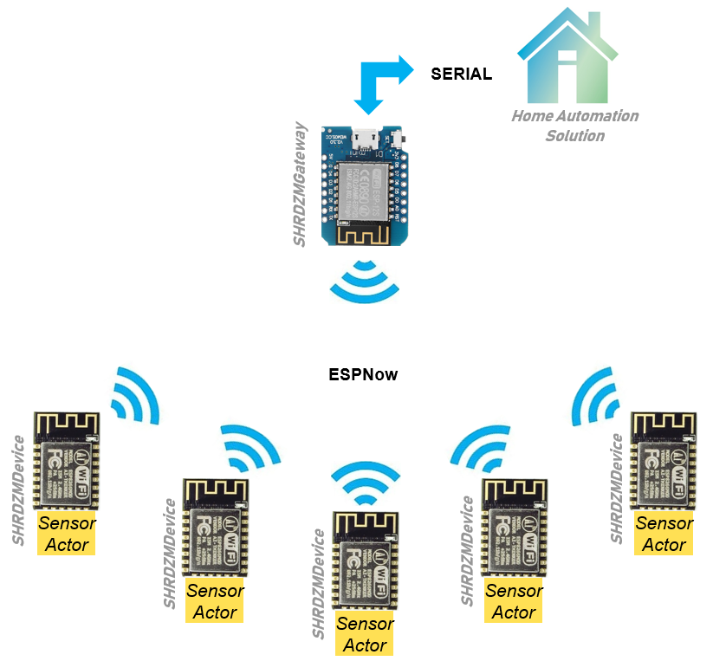
hardware/IntegrationStyle_1.png
