Noschvie/shrdzm/hardware/IntegrationStyle_2.png

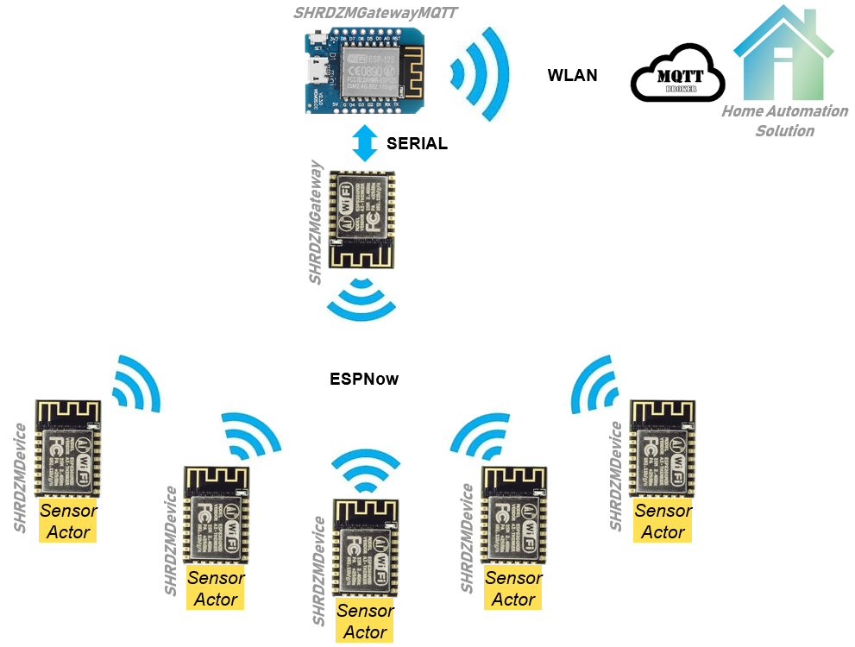
hardware/IntegrationStyle_2.png
