Noschvie/shrdzm/hardware/IntegrationStyle_2a.png

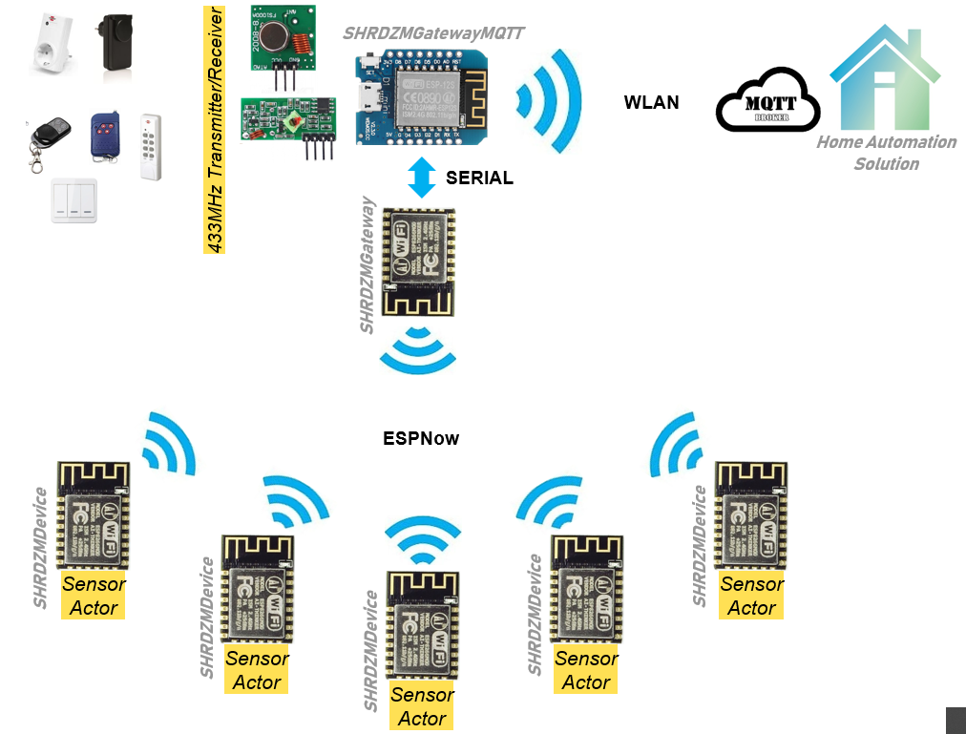
hardware/IntegrationStyle_2a.png
