Noschvie/shrdzm/hardware/IntegrationStyle_3.png

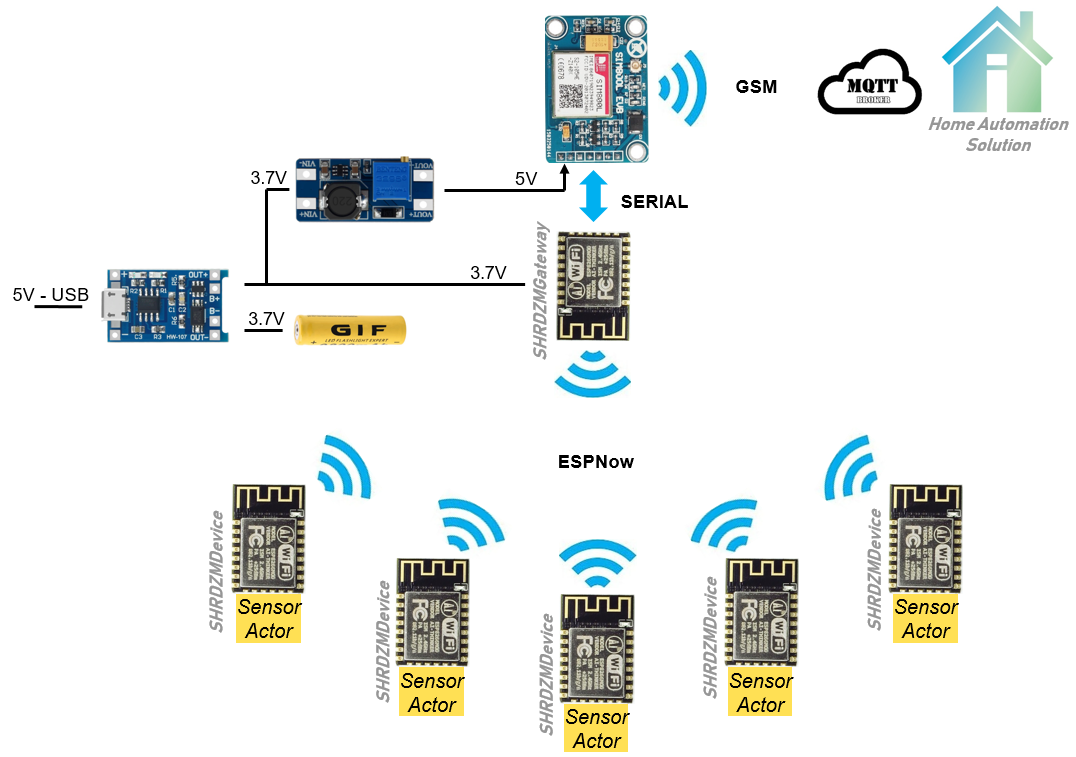
hardware/IntegrationStyle_3.png
