Noschvie/shrdzm/hardware/IntegrationStyle_4.png

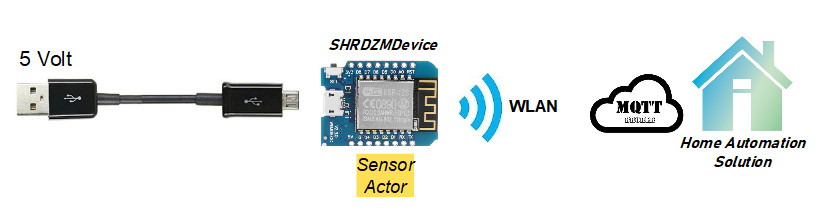
hardware/IntegrationStyle_4.png
