Noschvie/shrdzm/hardware/JumperCable.png

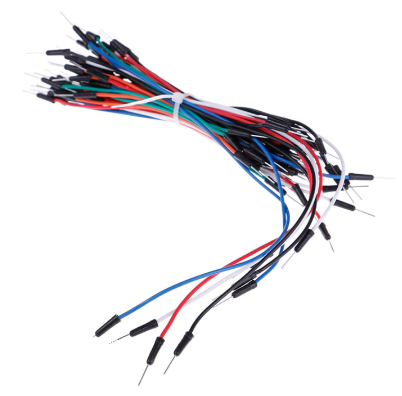
hardware/JumperCable.png
