Noschvie/shrdzm/hardware/LongTimeUp.png

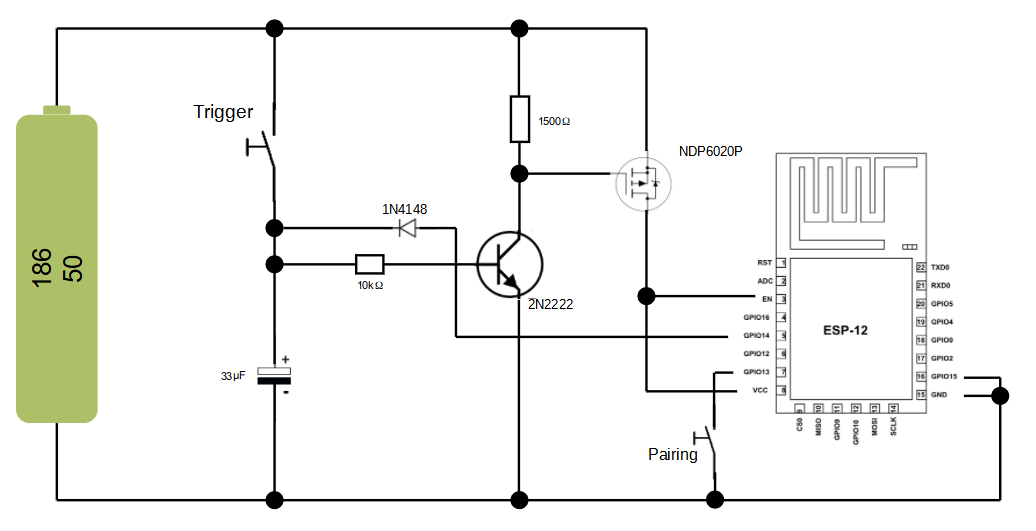
hardware/LongTimeUp.png
