Noschvie/shrdzm/hardware/MQ135.png

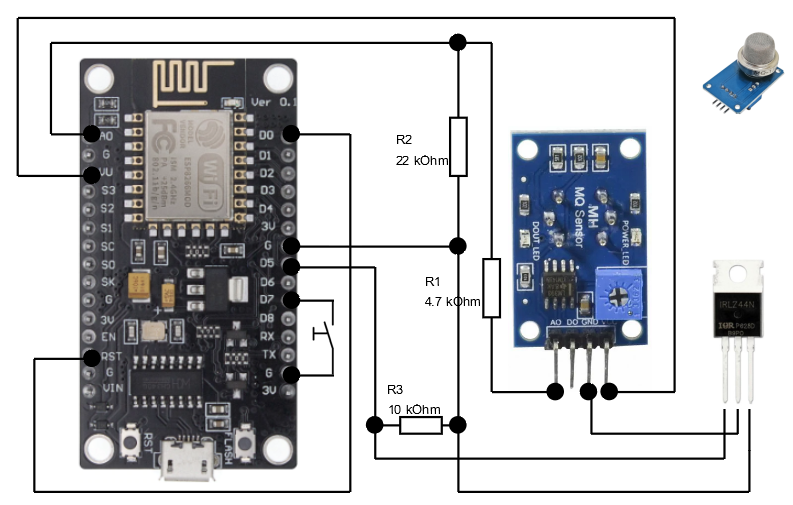
hardware/MQ135.png
