Noschvie/shrdzm/hardware/MQ135_1.png

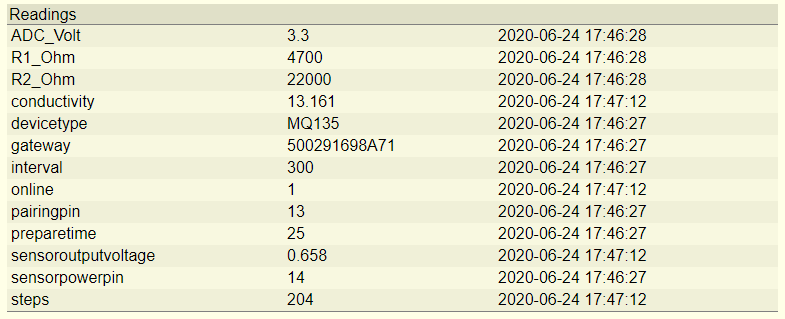
hardware/MQ135_1.png
