Noschvie/shrdzm/hardware/MQ135_2.png

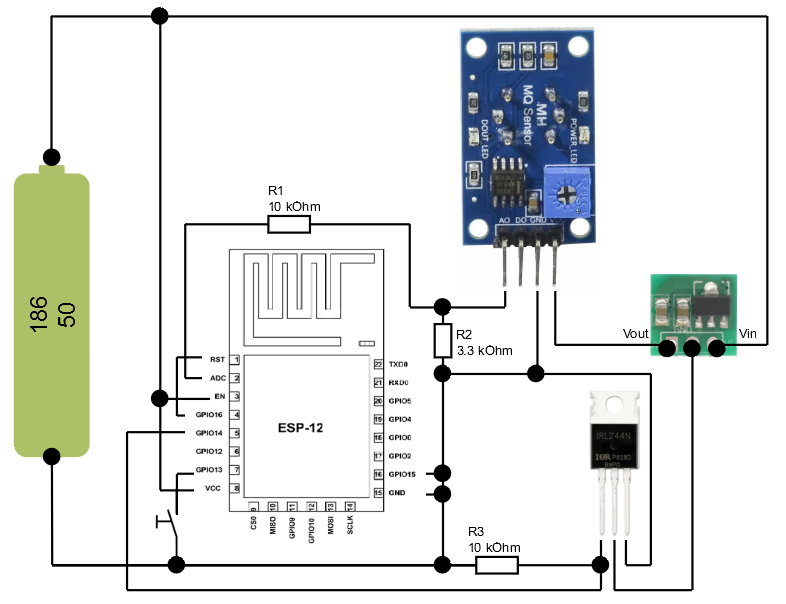
hardware/MQ135_2.png
