Noschvie/shrdzm/hardware/MQTTGateway_1.JPG

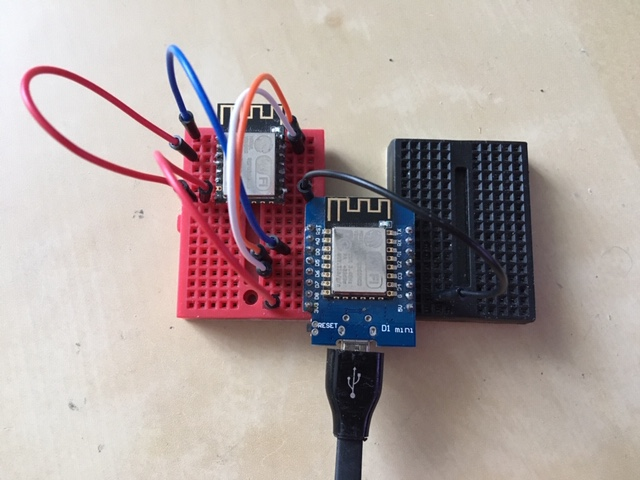
hardware/MQTTGateway_1.JPG
