Noschvie/shrdzm/hardware/MQTTGateway_2.JPG

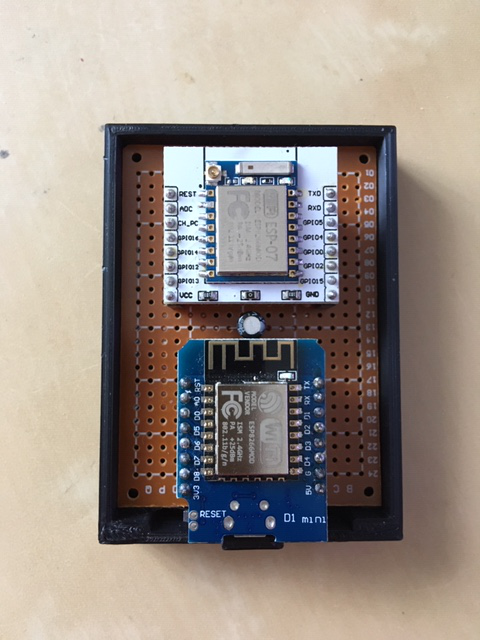
hardware/MQTTGateway_2.JPG
