Noschvie/shrdzm/hardware/NodeMCU.png

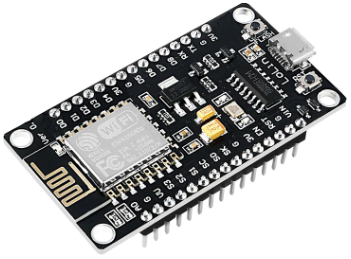
hardware/NodeMCU.png
