Noschvie/shrdzm/hardware/openSenseMap_1.png

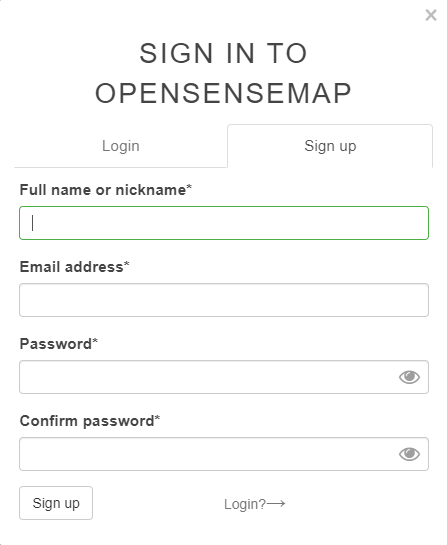
hardware/openSenseMap_1.png
