Noschvie/shrdzm/hardware/openSenseMap_2.png

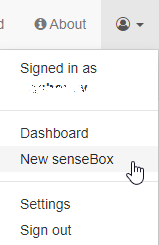
hardware/openSenseMap_2.png
