Noschvie/shrdzm/hardware/openSenseMap_3.png

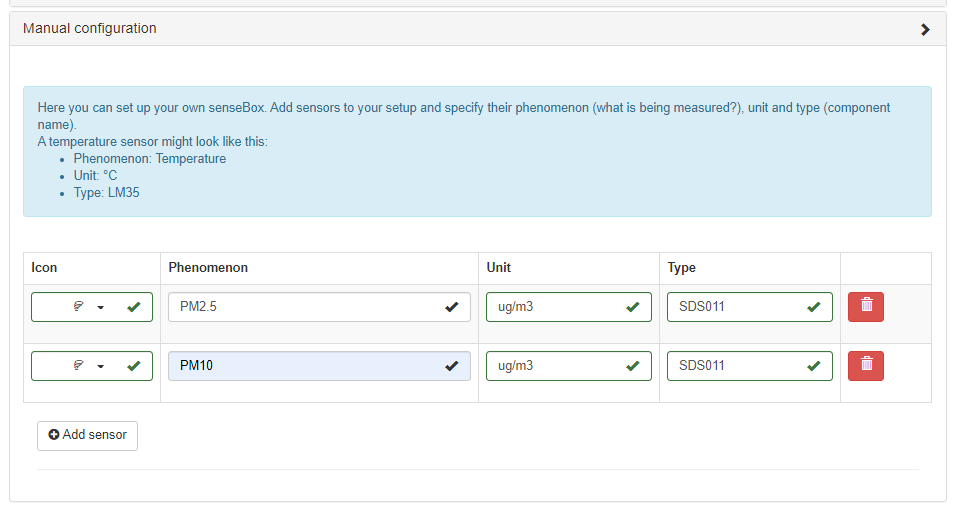
hardware/openSenseMap_3.png
