Noschvie/shrdzm/hardware/openSenseMap_4.png

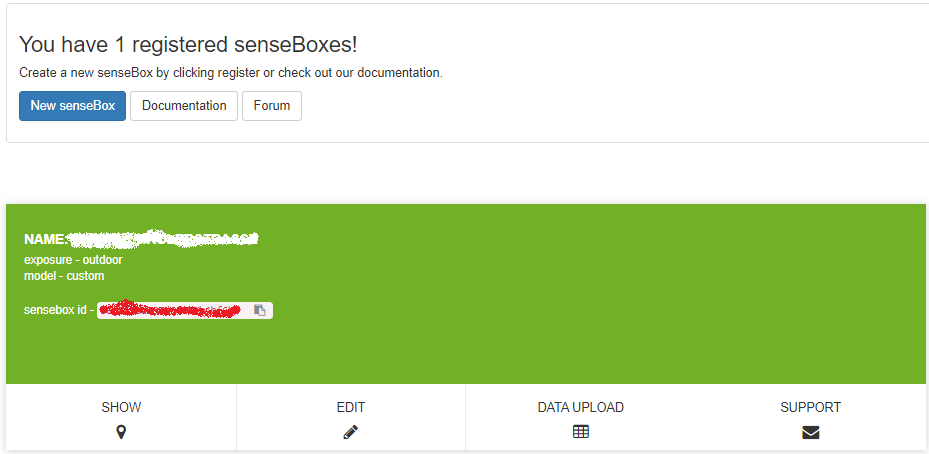
hardware/openSenseMap_4.png
