Noschvie/shrdzm/hardware/openSenseMap_5.png

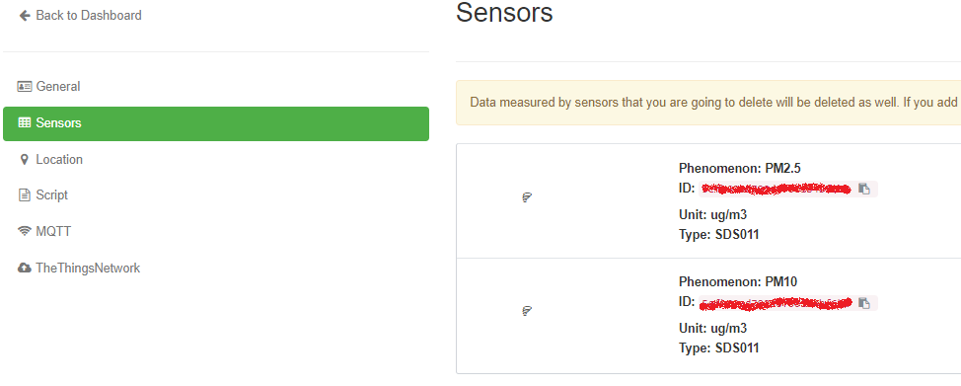
hardware/openSenseMap_5.png
