Noschvie/shrdzm/hardware/openSenseMap_6.png

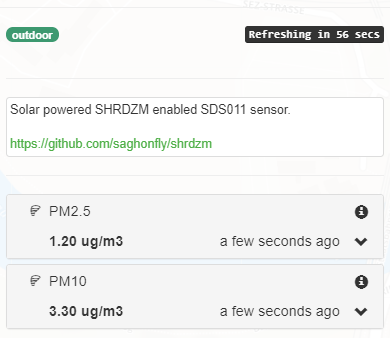
hardware/openSenseMap_6.png
