Noschvie/shrdzm/hardware/P1.jpg

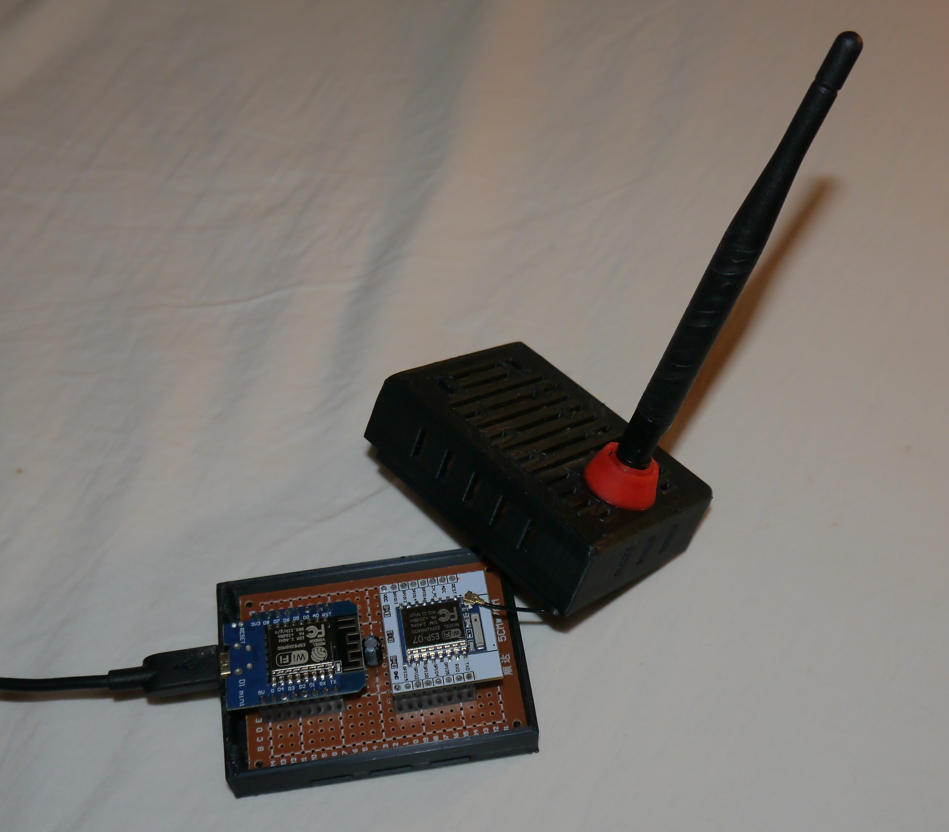
hardware/P1.jpg
