Noschvie/shrdzm/hardware/P2.jpg

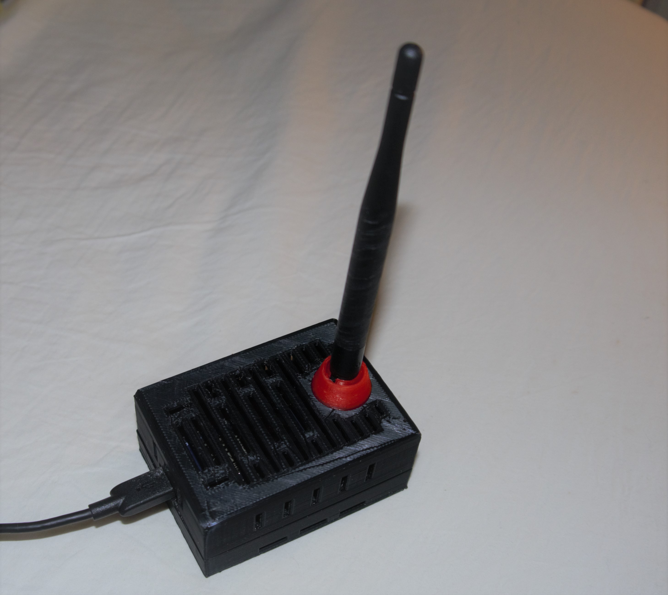
hardware/P2.jpg
