Noschvie/shrdzm/hardware/PiezoWaterSensor_Template.jpg

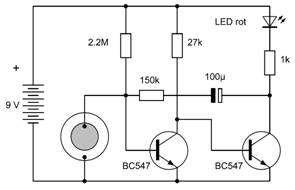
hardware/PiezoWaterSensor_Template.jpg
