Noschvie/shrdzm/hardware/PushButtonSwitch.png

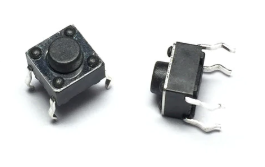
hardware/PushButtonSwitch.png
