Noschvie/shrdzm/hardware/Putty_1.png

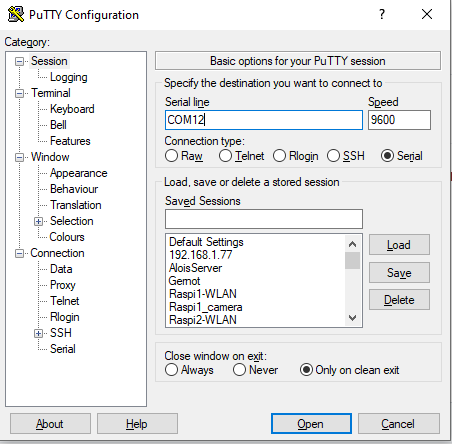
hardware/Putty_1.png
