Noschvie/shrdzm/hardware/Putty_2.png

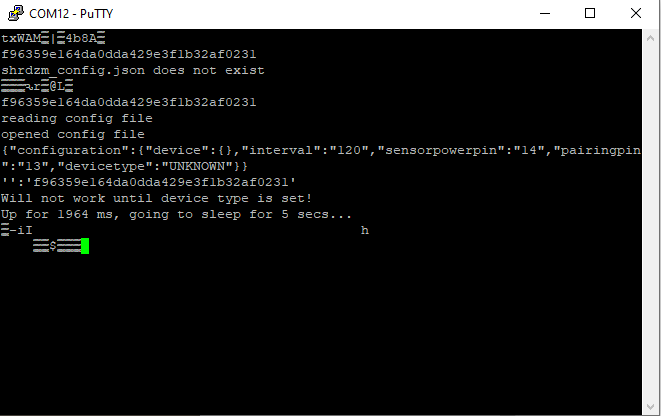
hardware/Putty_2.png
