Noschvie/shrdzm/hardware/Putty_3.png

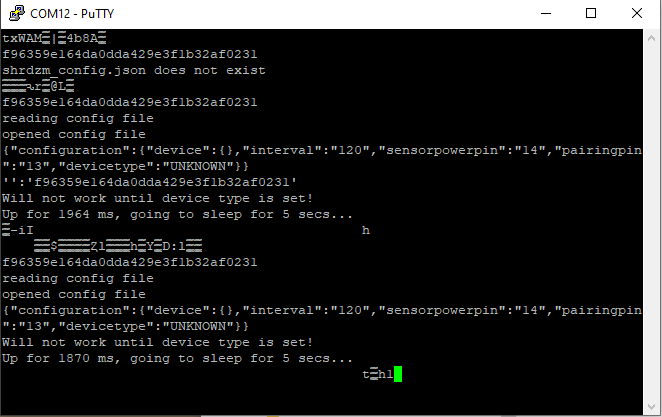
hardware/Putty_3.png
