Noschvie/shrdzm/hardware/Putty_4.png

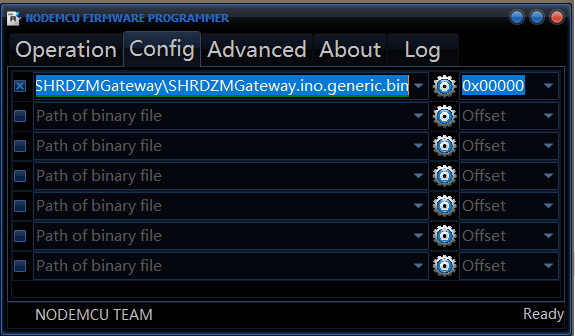
hardware/Putty_4.png
