Noschvie/shrdzm/hardware/RasPi.png

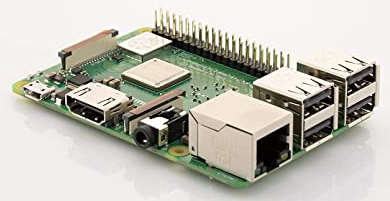
hardware/RasPi.png
