Noschvie/shrdzm/hardware/Sagemcom.png

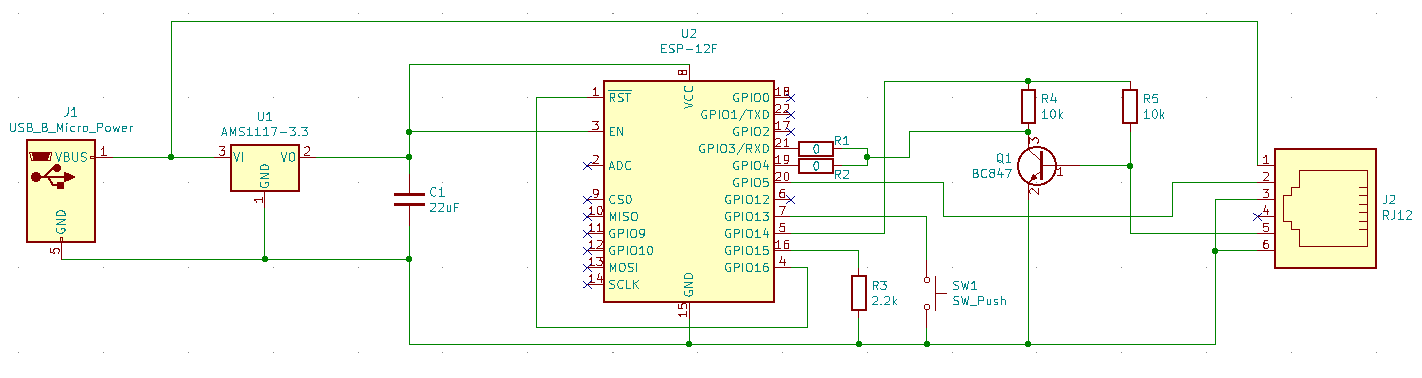
hardware/Sagemcom.png
