Noschvie/shrdzm/hardware/SDS011-Solar.jpg

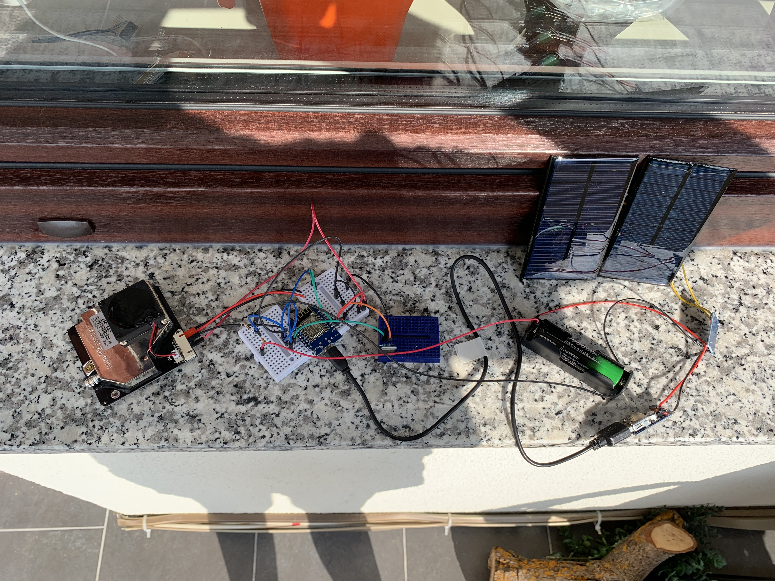
hardware/SDS011-Solar.jpg
