Noschvie/shrdzm/hardware/SDS011_3DCase.jpg

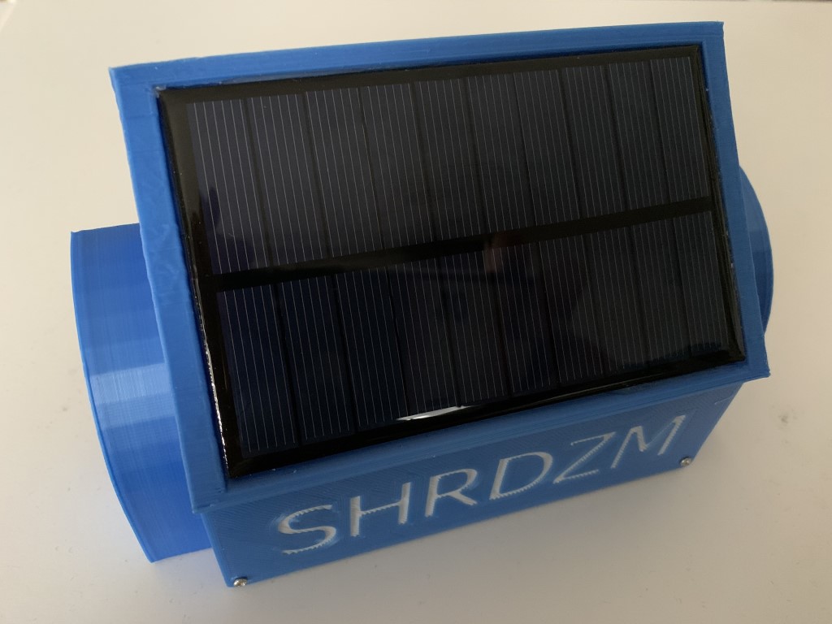
hardware/SDS011_3DCase.jpg
