Noschvie/shrdzm/hardware/SDS011_Blue.jpg

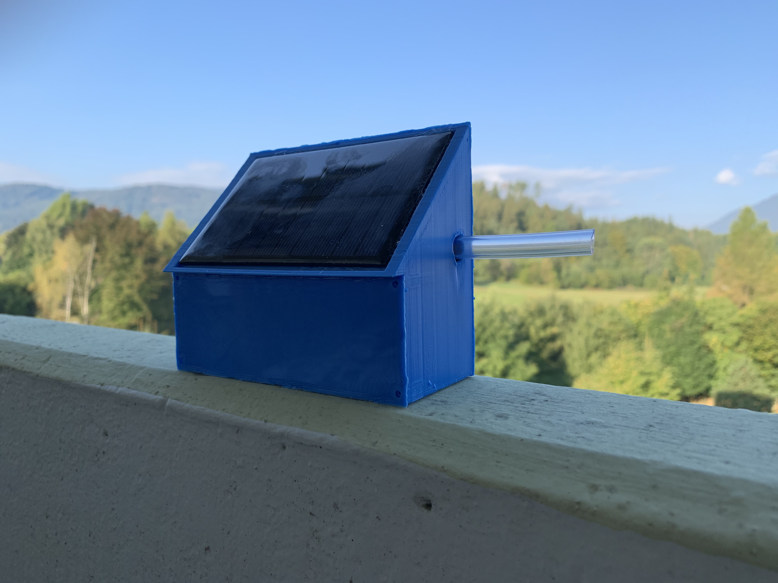
hardware/SDS011_Blue.jpg
