Noschvie/shrdzm/hardware/SDS011_Blue_Small.jpg

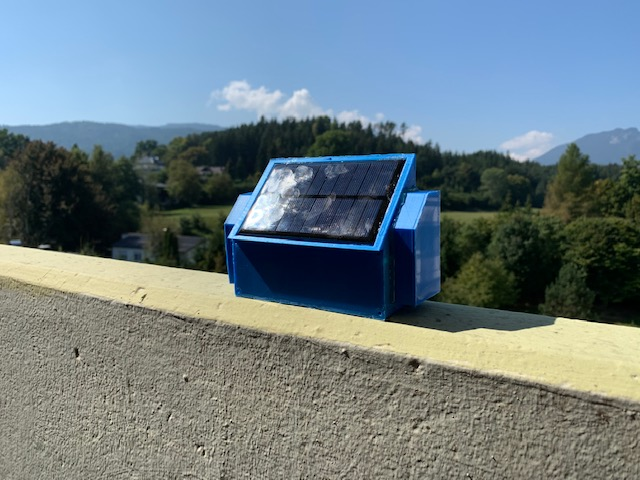
hardware/SDS011_Blue_Small.jpg
