Noschvie/shrdzm/hardware/SDS011_Final.png

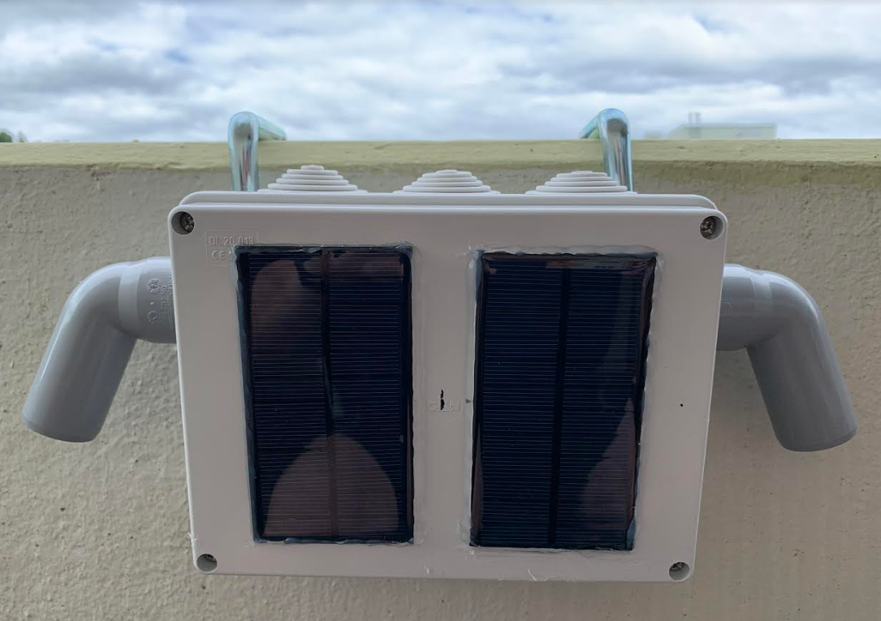
hardware/SDS011_Final.png
