Noschvie/shrdzm/hardware/SDS011_Full.png

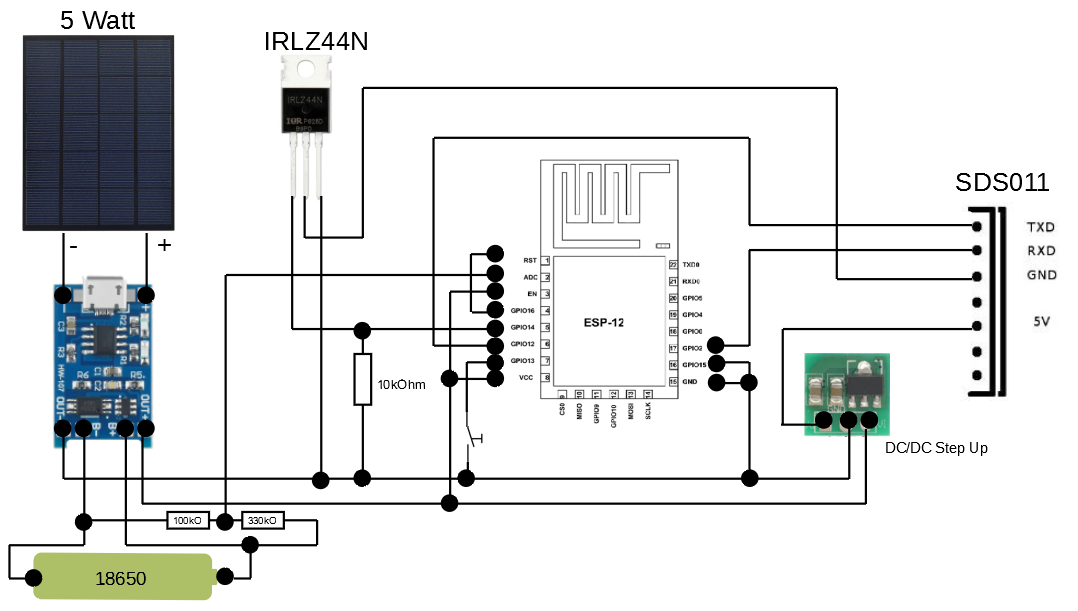
hardware/SDS011_Full.png
