Noschvie/shrdzm/hardware/SDS011_Minimum.png

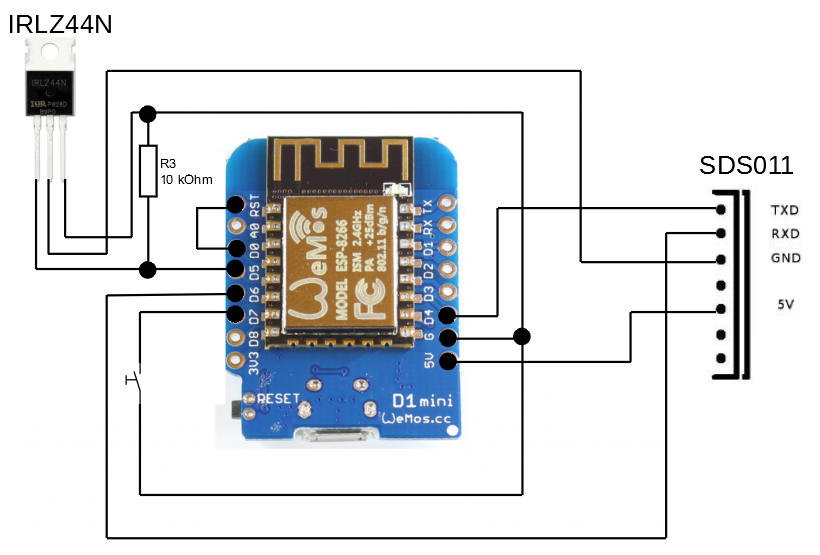
hardware/SDS011_Minimum.png
