Noschvie/shrdzm/hardware/SDS011_NOMOSFET.png

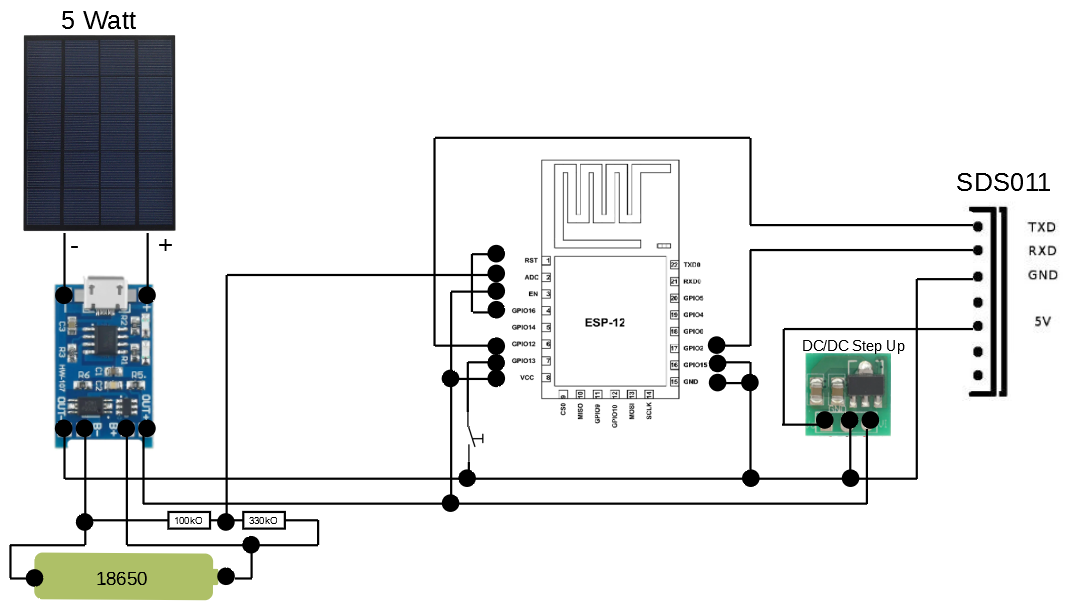
hardware/SDS011_NOMOSFET.png
