Noschvie/shrdzm/hardware/SDS011_Ossiachersee.png

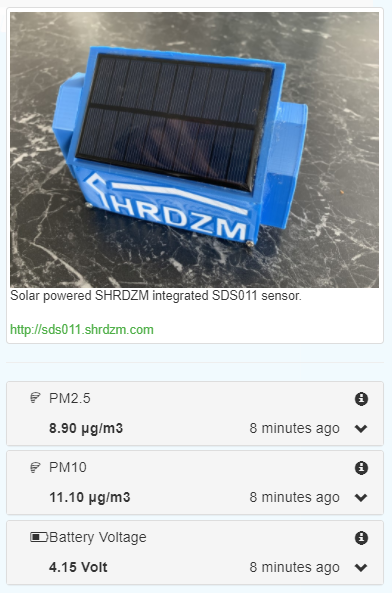
hardware/SDS011_Ossiachersee.png
