Noschvie/shrdzm/hardware/SDS011_Small.png

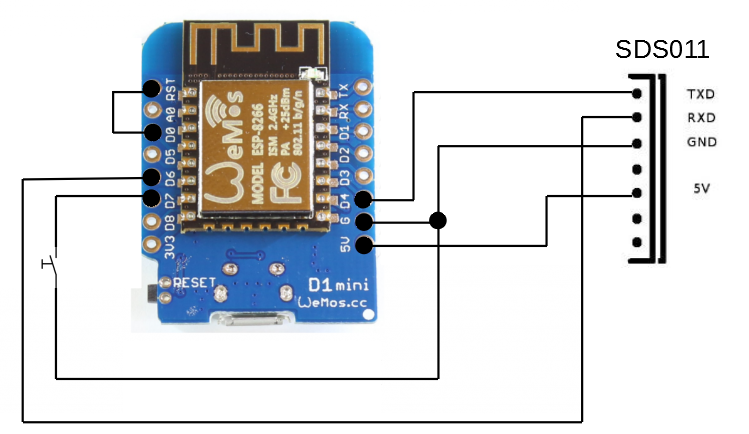
hardware/SDS011_Small.png
