Noschvie/shrdzm/hardware/SDS011Cloudy.png

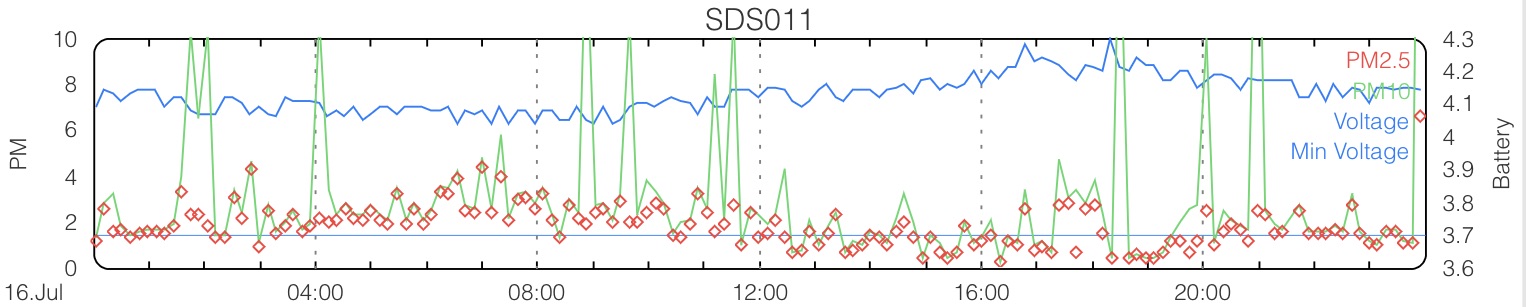
hardware/SDS011Cloudy.png
