Noschvie/shrdzm/hardware/SDS011Grafana.png

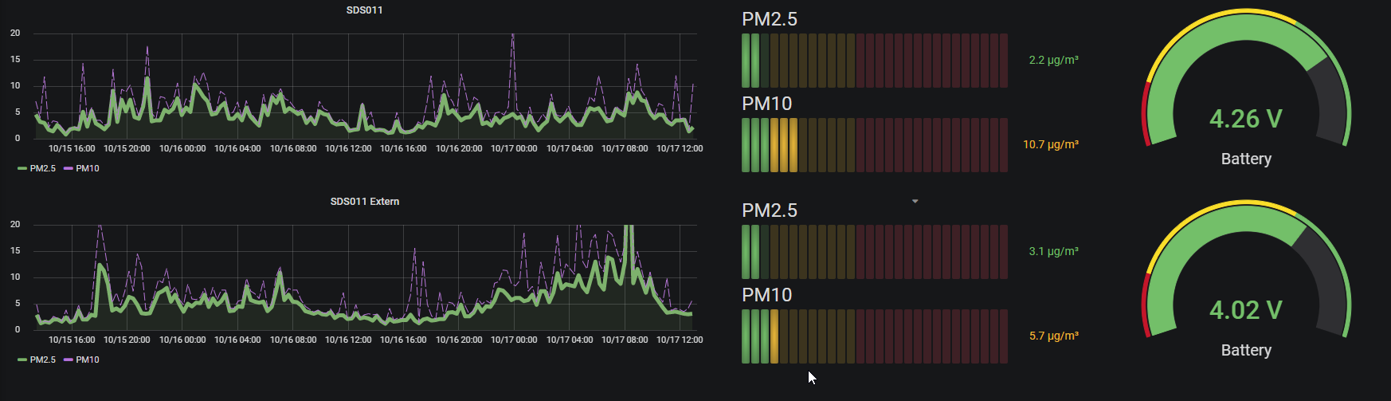
hardware/SDS011Grafana.png
