Noschvie/shrdzm/hardware/SensorMinimal.JPG

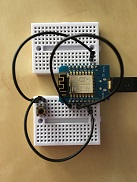
hardware/SensorMinimal.JPG
