Noschvie/shrdzm/hardware/Sensors1.png

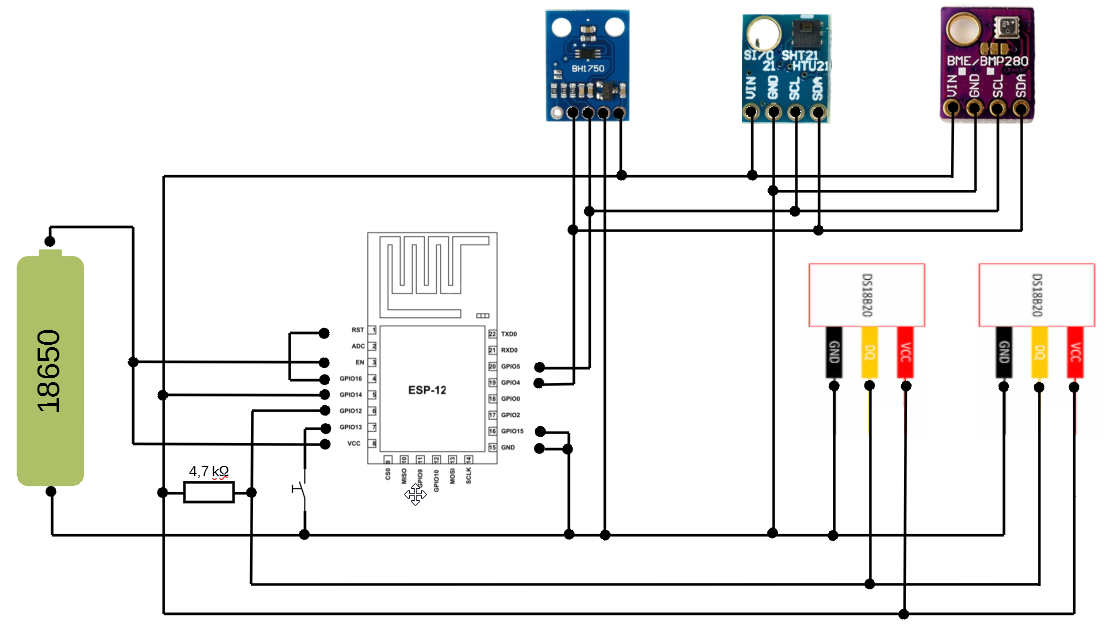
hardware/Sensors1.png
