Noschvie/shrdzm/hardware/ShortTimeUp.png

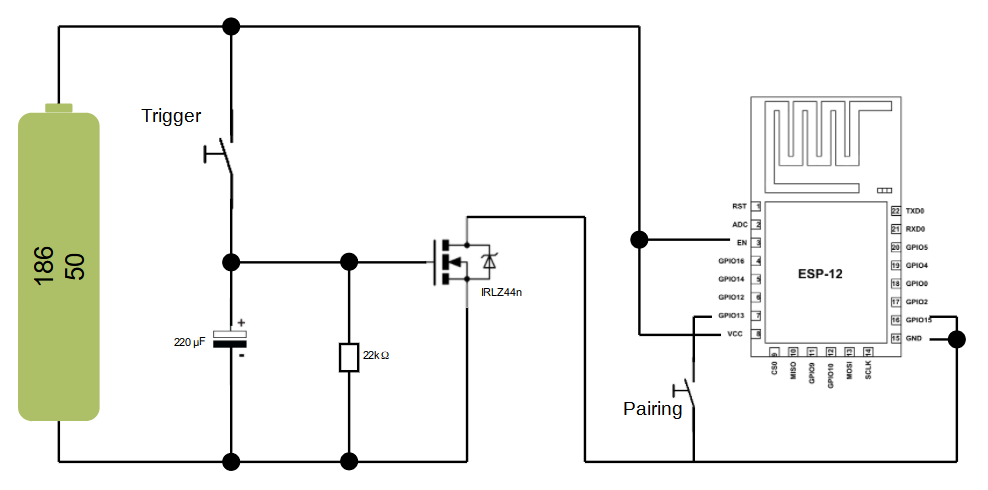
hardware/ShortTimeUp.png
