Noschvie/shrdzm/hardware/SHRDZMDevice-AP-1.png

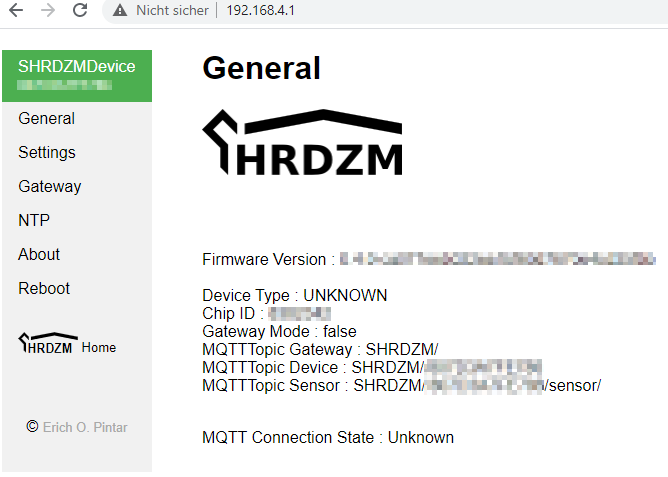
hardware/SHRDZMDevice-AP-1.png
