Noschvie/shrdzm/hardware/SHRDZMDevice-AP-2.png

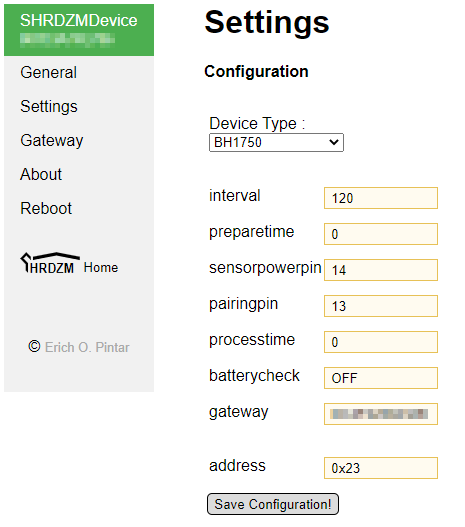
hardware/SHRDZMDevice-AP-2.png
