Noschvie/shrdzm/hardware/SHRDZMDevice-AP-3.png

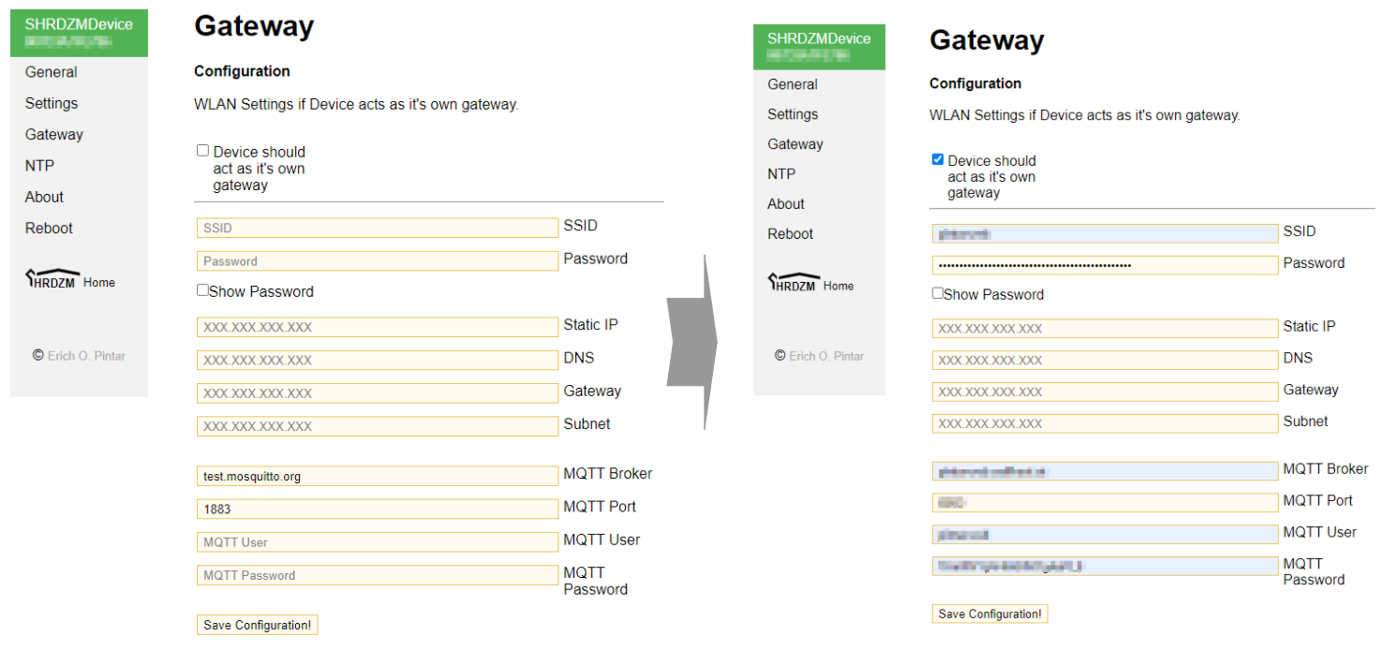
hardware/SHRDZMDevice-AP-3.png
