Noschvie/shrdzm/hardware/SHRDZMDevice-AP-4.png

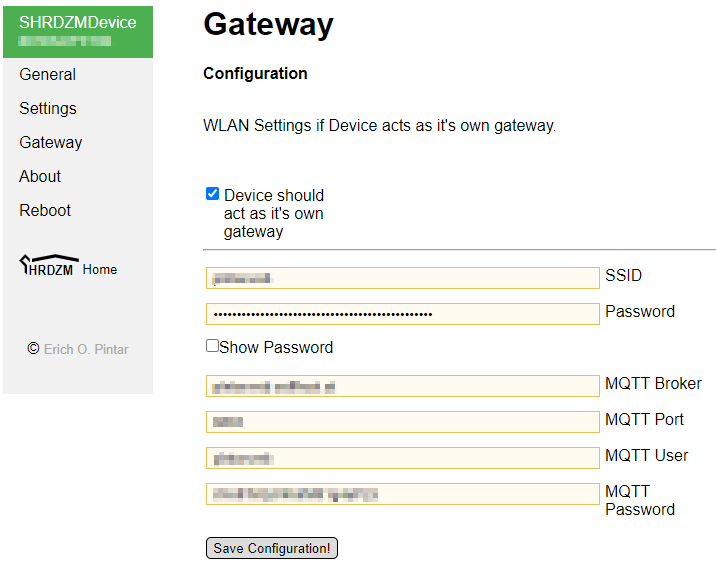
hardware/SHRDZMDevice-AP-4.png
