Noschvie/shrdzm/hardware/SHRDZMDevice-AP-5.png

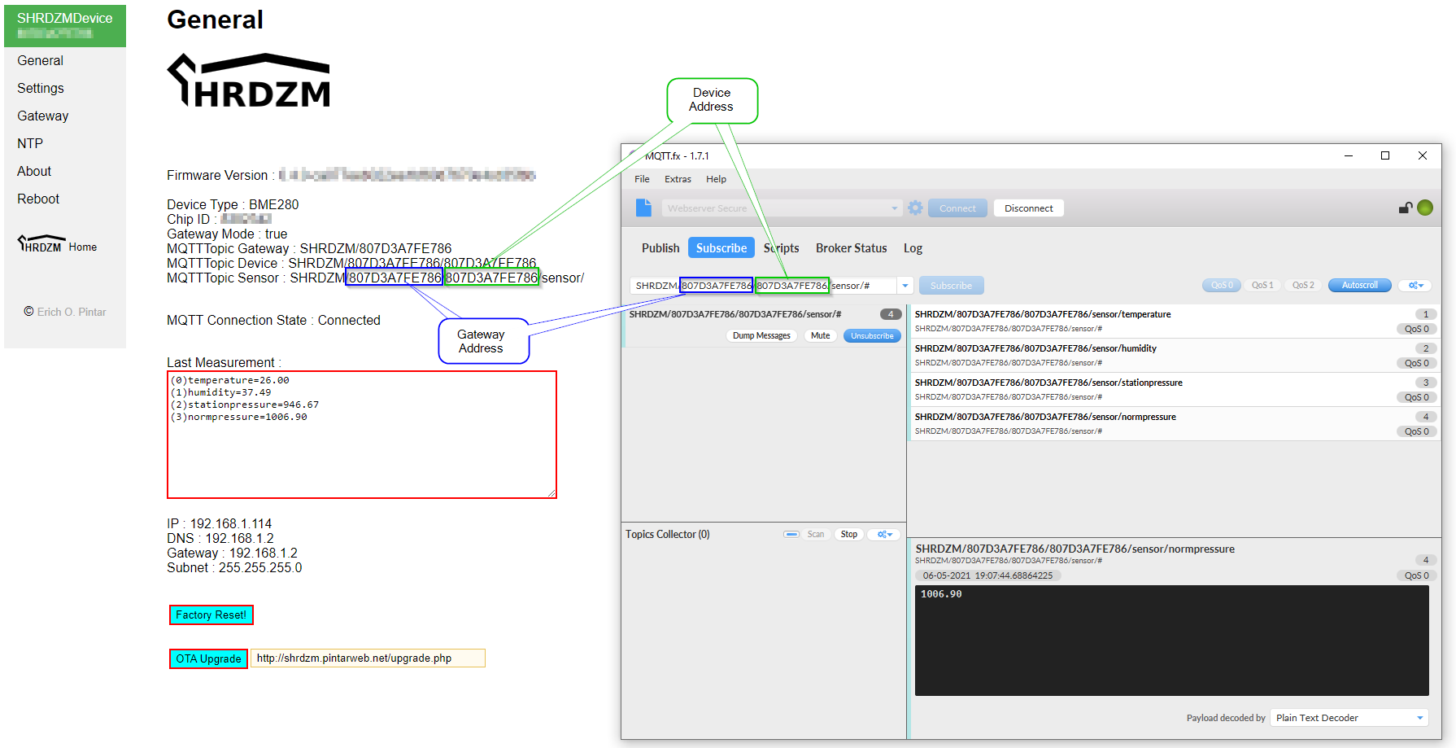
hardware/SHRDZMDevice-AP-5.png
