Noschvie/shrdzm/hardware/SHRDZMDevice-AP.png

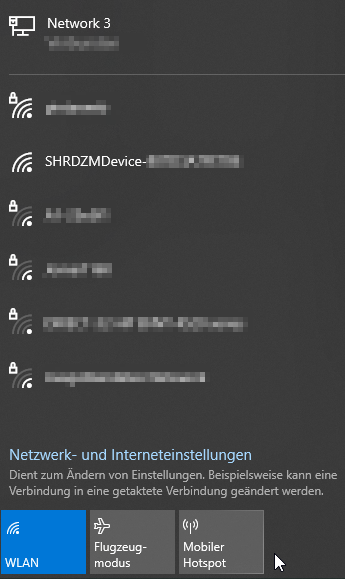
hardware/SHRDZMDevice-AP.png
