Noschvie/shrdzm/hardware/SHRDZMGateway_OTA1.png

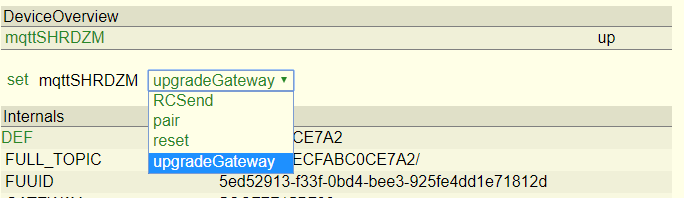
hardware/SHRDZMGateway_OTA1.png
