Noschvie/shrdzm/hardware/SHRDZMGatewayMQTT-AP.png

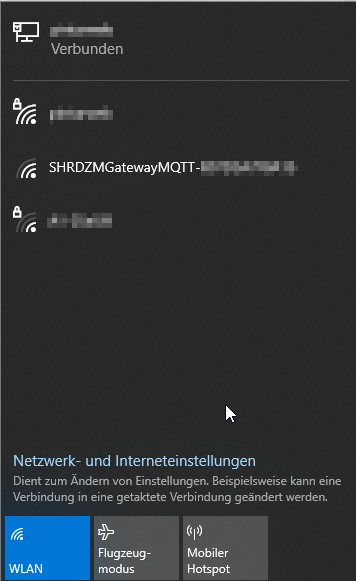
hardware/SHRDZMGatewayMQTT-AP.png
