Noschvie/shrdzm/hardware/SHRDZMGatewayMQTT-webserver.png

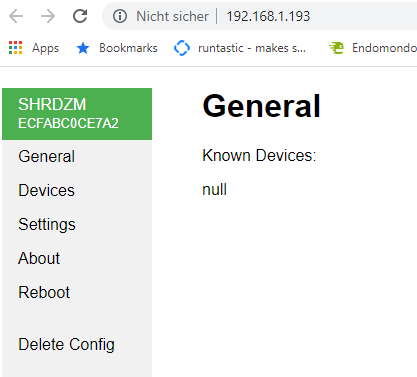
hardware/SHRDZMGatewayMQTT-webserver.png
