Noschvie/shrdzm/hardware/SHRDZMGatewayMQTT-WIFI-Parameter.png

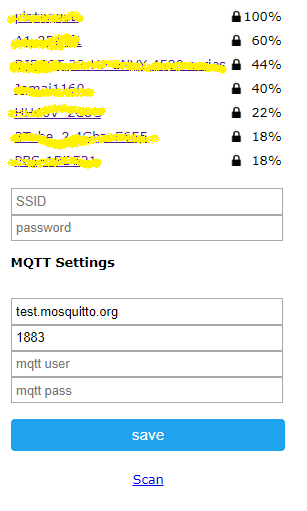
hardware/SHRDZMGatewayMQTT-WIFI-Parameter.png
