Noschvie/shrdzm/hardware/SHRDZMGatewayMQTT-WifiManager.png

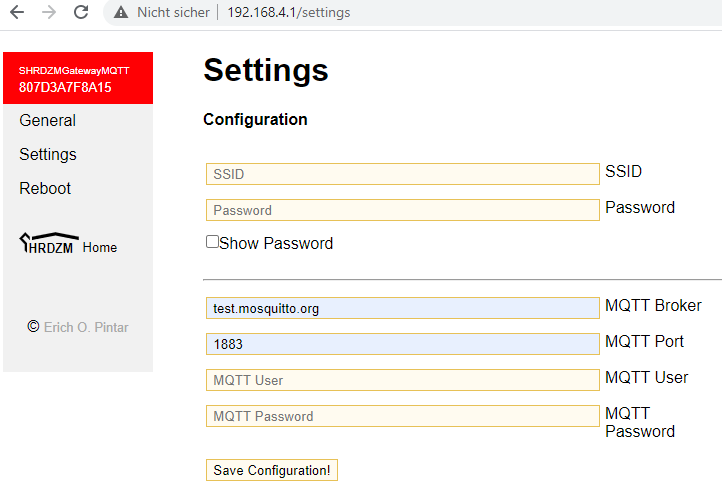
hardware/SHRDZMGatewayMQTT-WifiManager.png
