Noschvie/shrdzm/hardware/SHRDZMGatewayMQTT_mini1.JPG

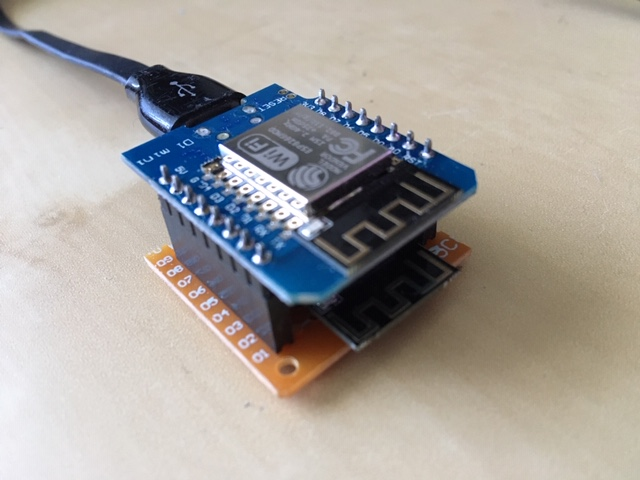
hardware/SHRDZMGatewayMQTT_mini1.JPG
