Noschvie/shrdzm/hardware/SHRDZMGatewayMQTT_mini2.JPG

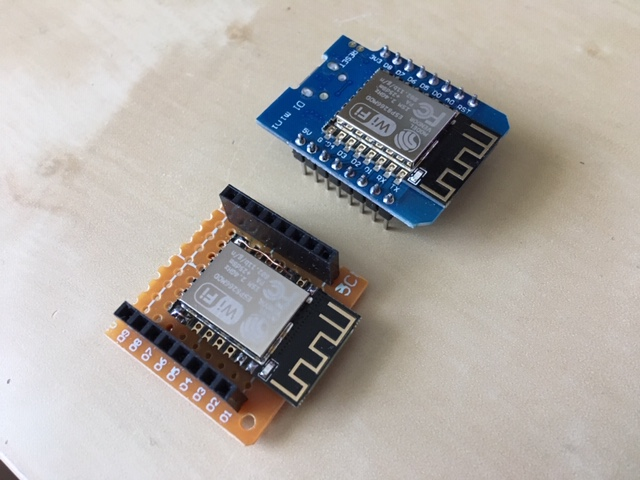
hardware/SHRDZMGatewayMQTT_mini2.JPG
