Noschvie/shrdzm/hardware/SHRDZMGatewayMQTT_OTA1.png

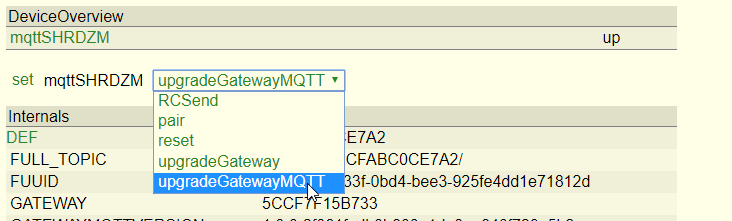
hardware/SHRDZMGatewayMQTT_OTA1.png
