Noschvie/shrdzm/hardware/SHRDZMGatewaySIM800.jpg

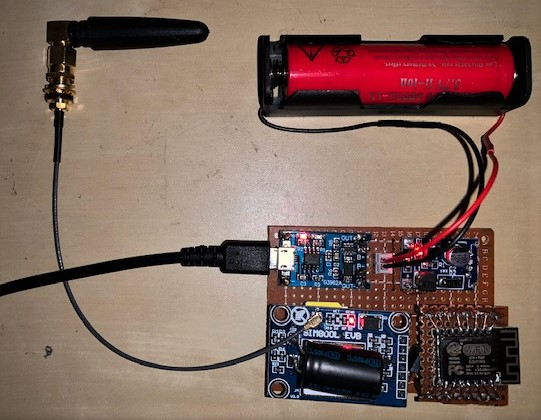
hardware/SHRDZMGatewaySIM800.jpg
