Noschvie/shrdzm/hardware/SHRDZMSensor_OTA1.png

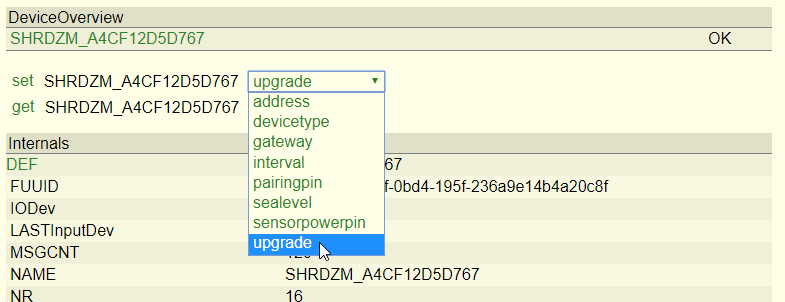
hardware/SHRDZMSensor_OTA1.png
