Noschvie/shrdzm/hardware/SHT21.png

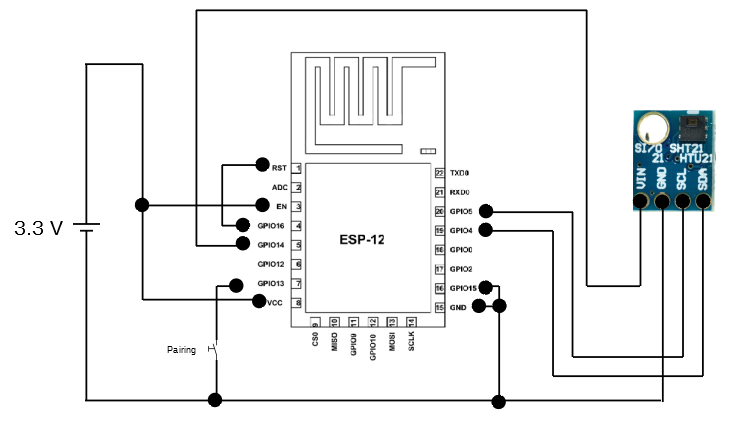
hardware/SHT21.png
