Noschvie/shrdzm/hardware/SIM800_Gateway1.png

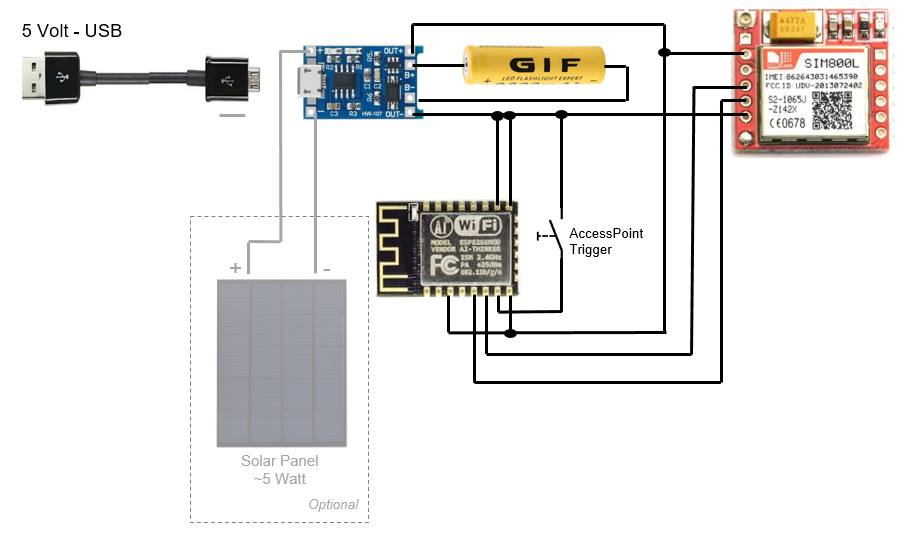
hardware/SIM800_Gateway1.png
