Noschvie/shrdzm/hardware/SIM800_Gateway.png

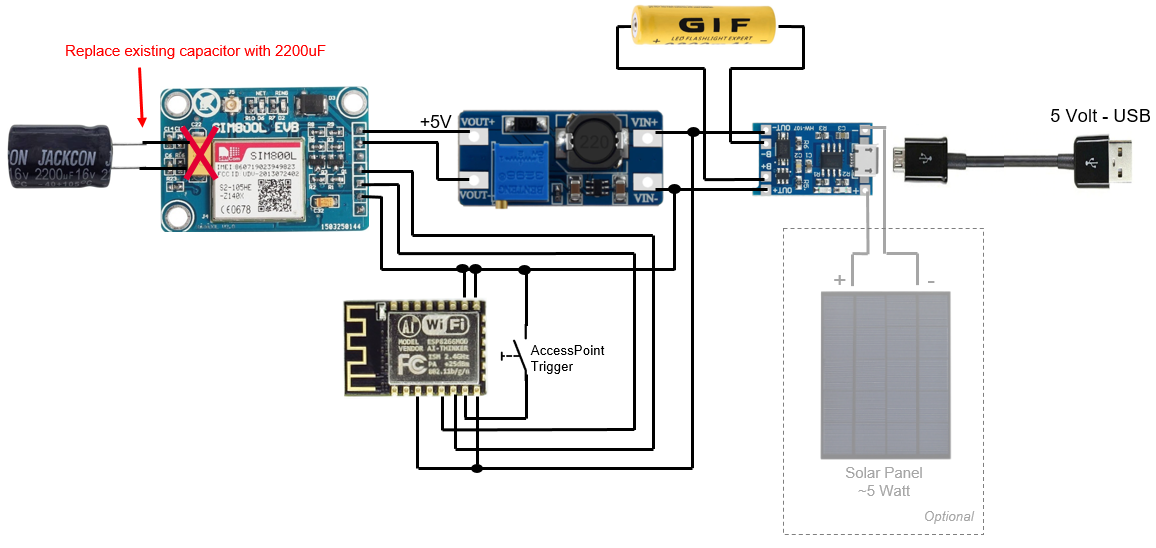
hardware/SIM800_Gateway.png
