Noschvie/shrdzm/hardware/Smartmeter.png

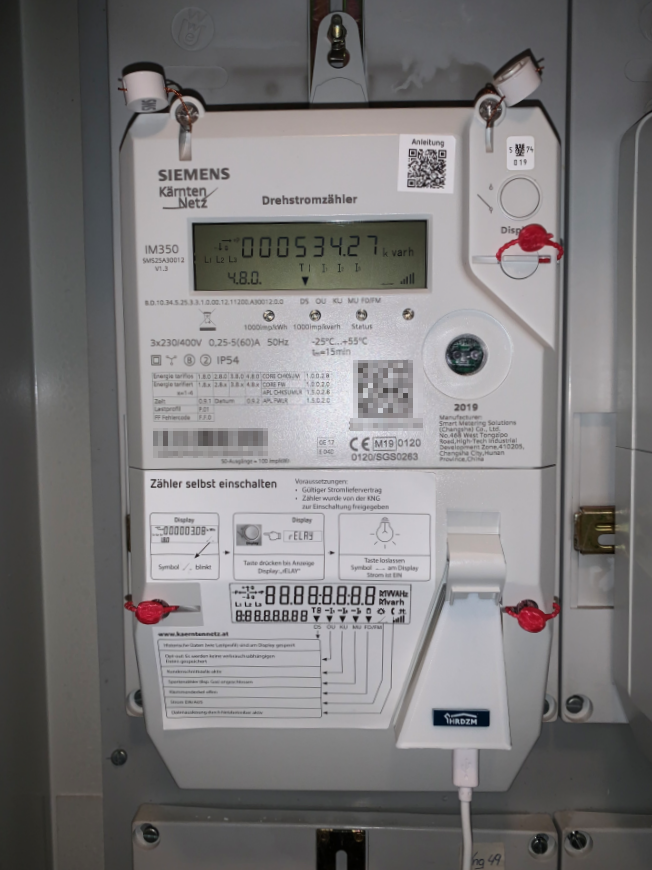
hardware/Smartmeter.png
