Noschvie/shrdzm/hardware/SmartmeterList.jpeg

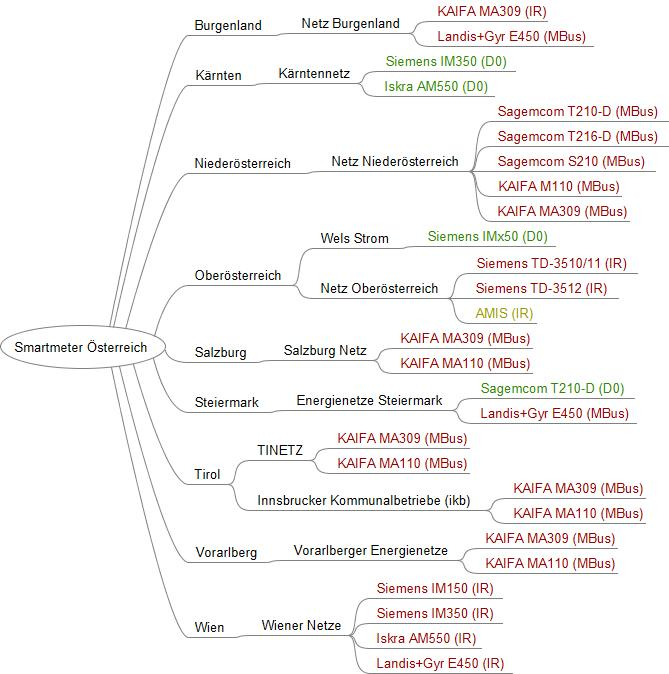
hardware/SmartmeterList.jpeg
