Noschvie/shrdzm/hardware/TP4056 USB18650 Lithium Battery Protection Charger.png

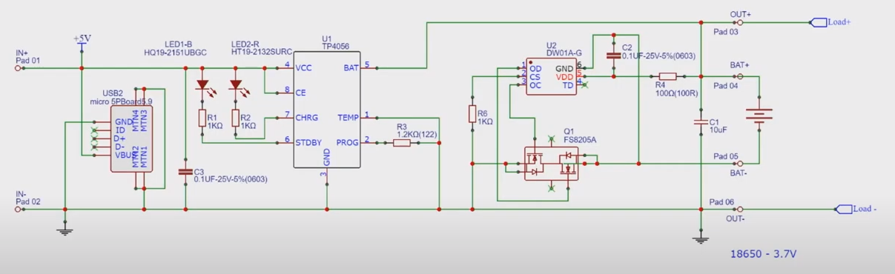
hardware/TP4056 USB18650 Lithium Battery Protection Charger.png
