Noschvie/shrdzm/hardware/Water Detector.png

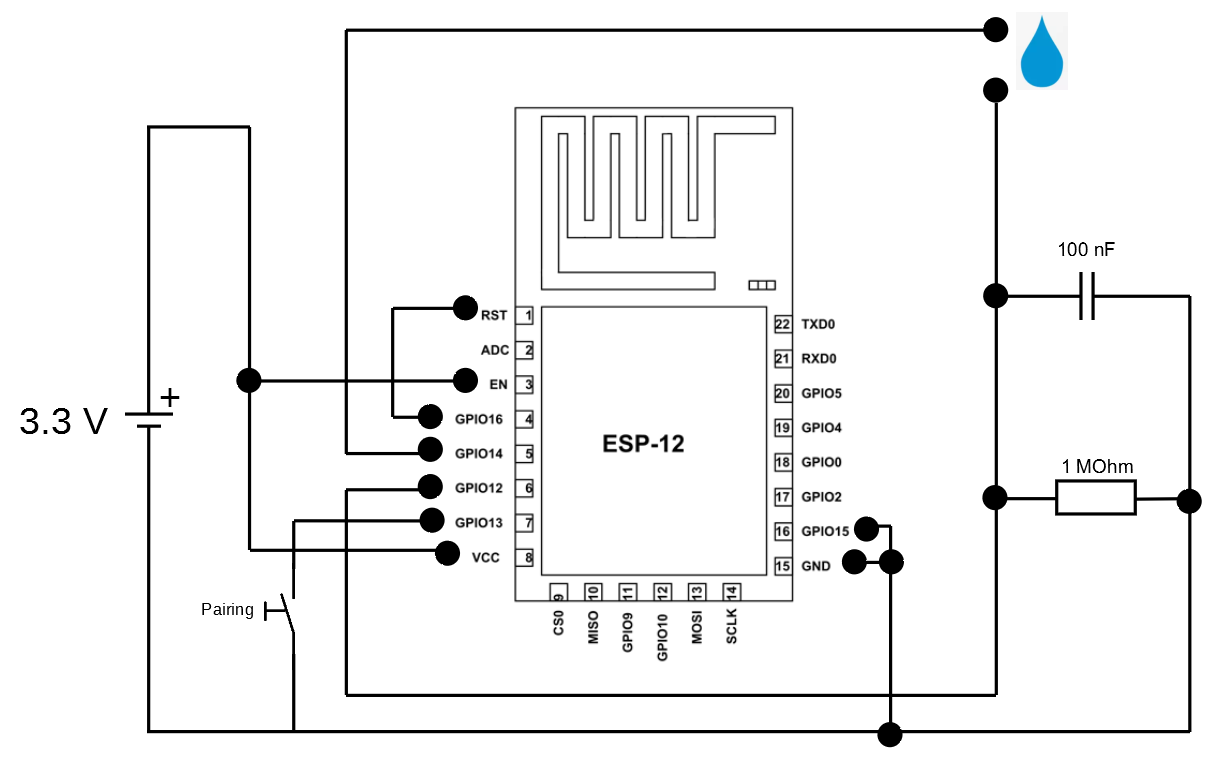
hardware/Water Detector.png
