Noschvie/shrdzm/hardware/WaterStripe1.png

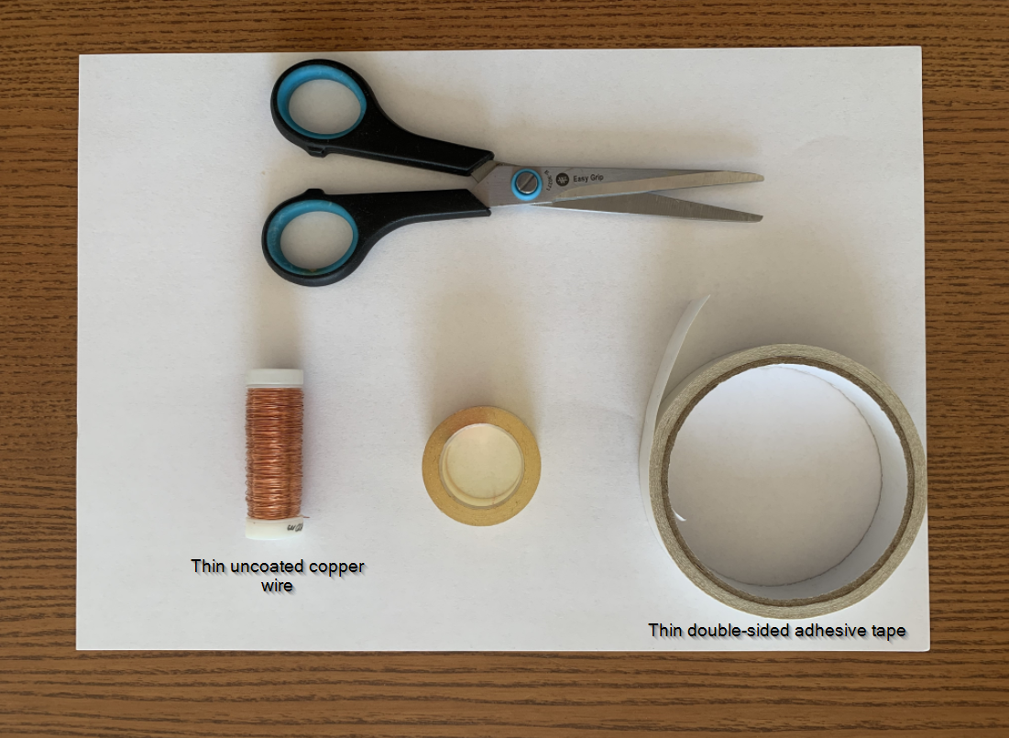
hardware/WaterStripe1.png
