Noschvie/shrdzm/hardware/WaterStripe2.png

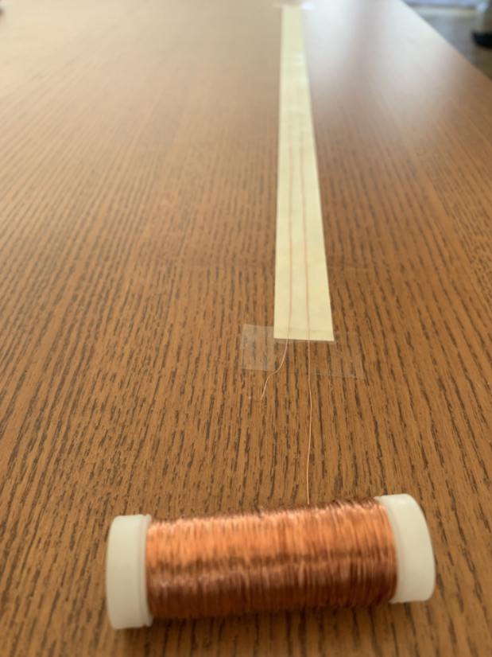
hardware/WaterStripe2.png
