Noschvie/shrdzm/hardware/WaterStripe3.png

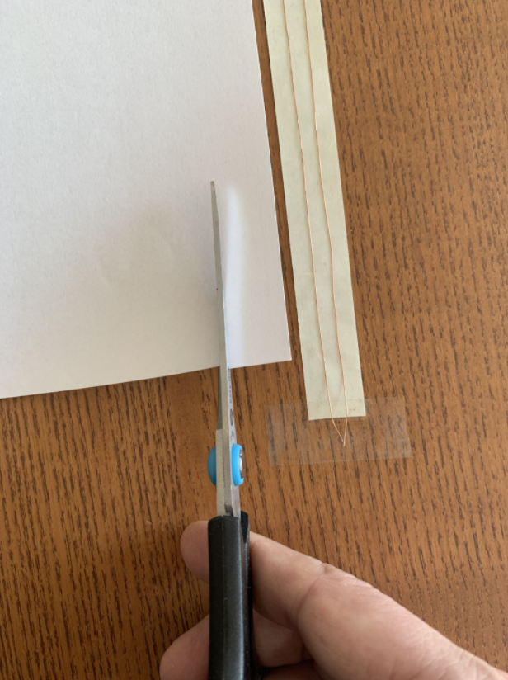
hardware/WaterStripe3.png
