Noschvie/shrdzm/hardware/WaterStripe4.png

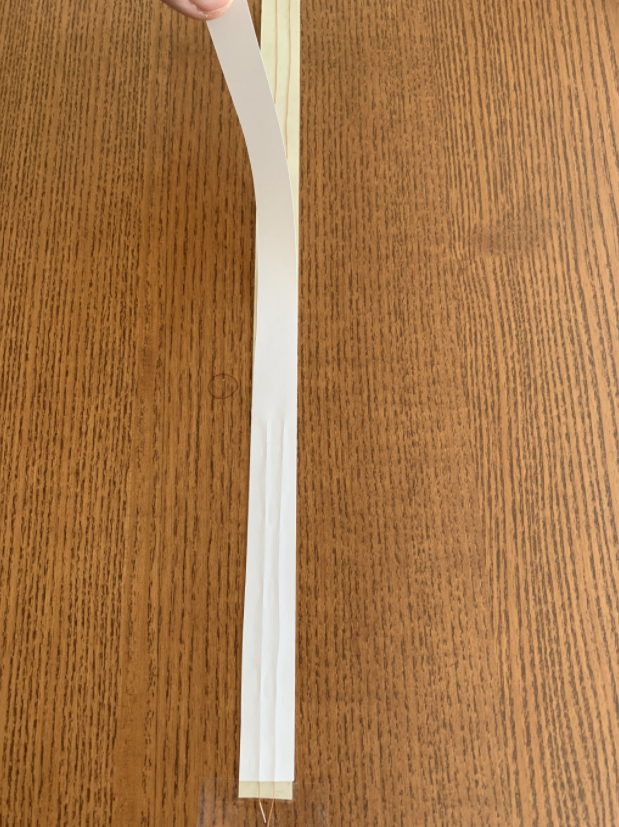
hardware/WaterStripe4.png
