Noschvie/shrdzm/hardware/WaterStripe5.png

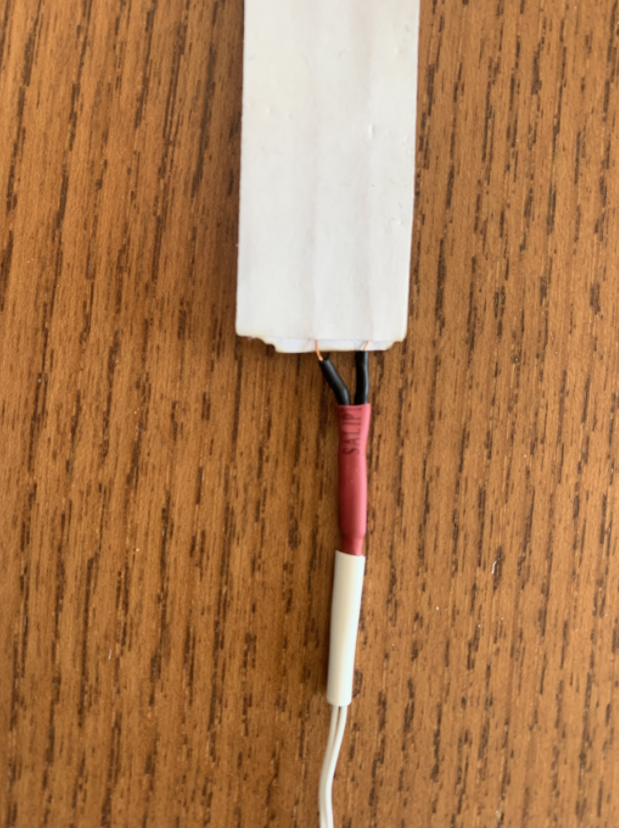
hardware/WaterStripe5.png
