Noschvie/shrdzm/hardware/WaterWithStripes.png

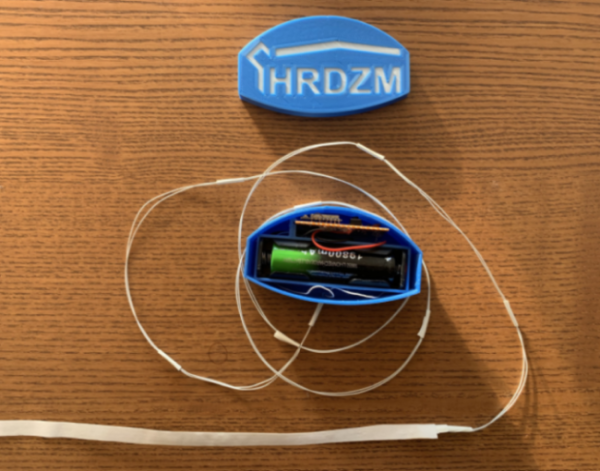
hardware/WaterWithStripes.png
