Noschvie/shrdzm/hardware/WeMos D1 mini.png

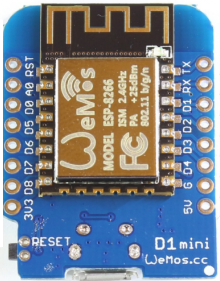
hardware/WeMos D1 mini.png
