Noschvie/shrdzm/hardware/DOORSENSOR_BOM.png

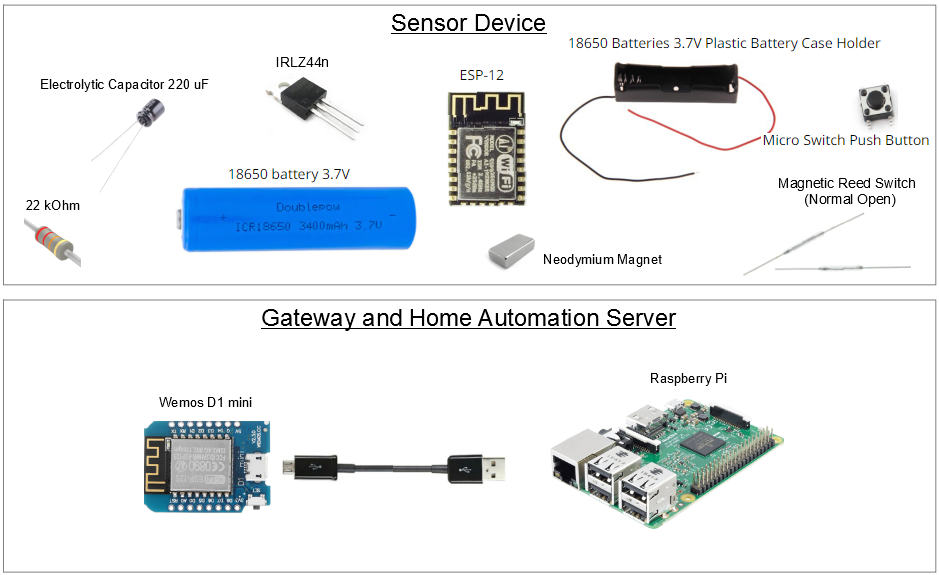
hardware/DOORSENSOR_BOM.png
