Noschvie/shrdzm/hardware/IntegrationStyleI_BOM.png

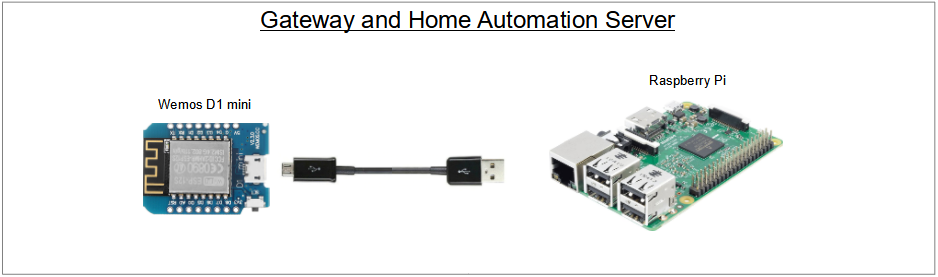
hardware/IntegrationStyleI_BOM.png
