Noschvie/shrdzm/hardware/SDS011_BOM.png

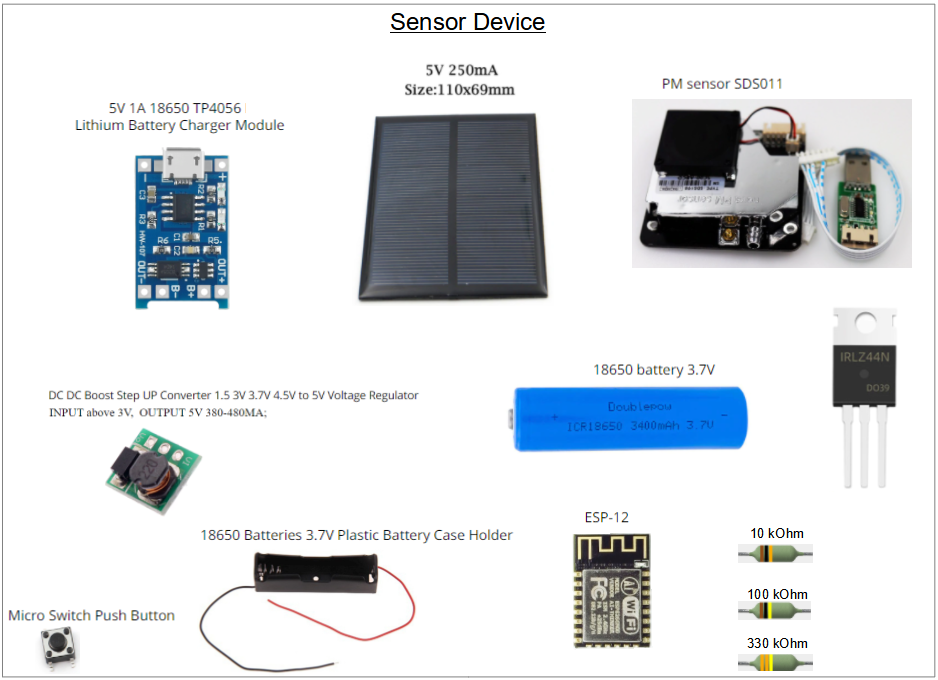
hardware/SDS011_BOM.png
