Noschvie/shrdzm/hardware/Water_BOM.png

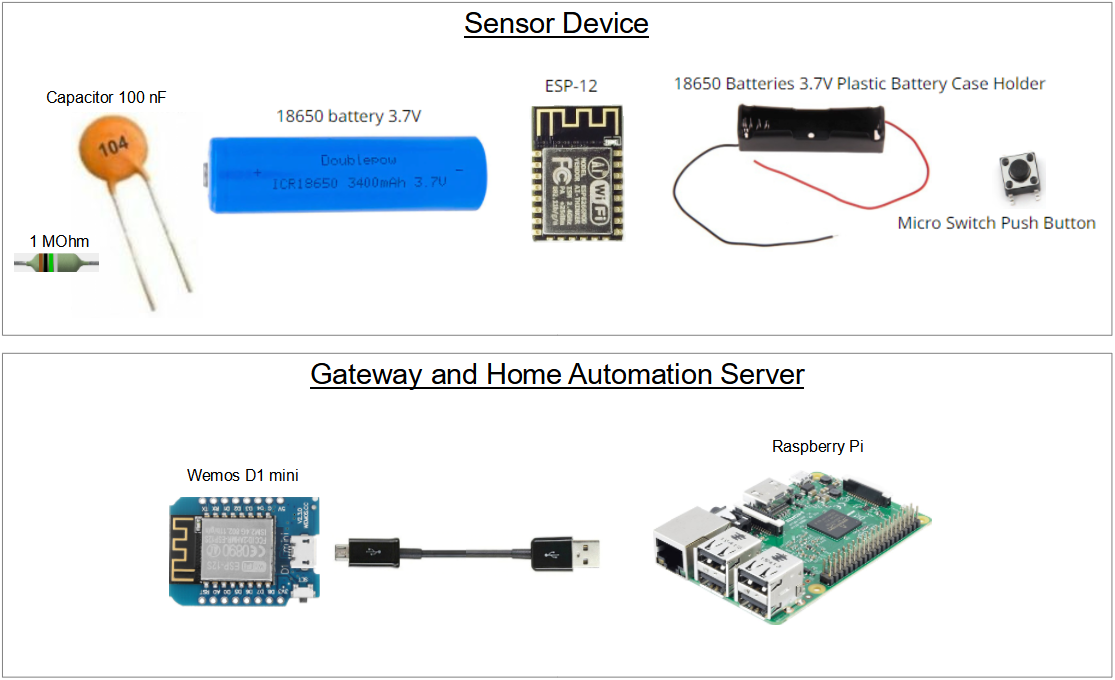
hardware/Water_BOM.png
