Noschvie/shrdzm/hardware/ESPFlashWiring.png

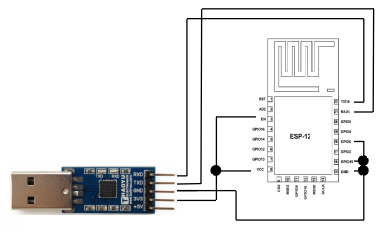
hardware/ESPFlashWiring.png
