Noschvie/shrdzm/hardware/FlashWiring.png

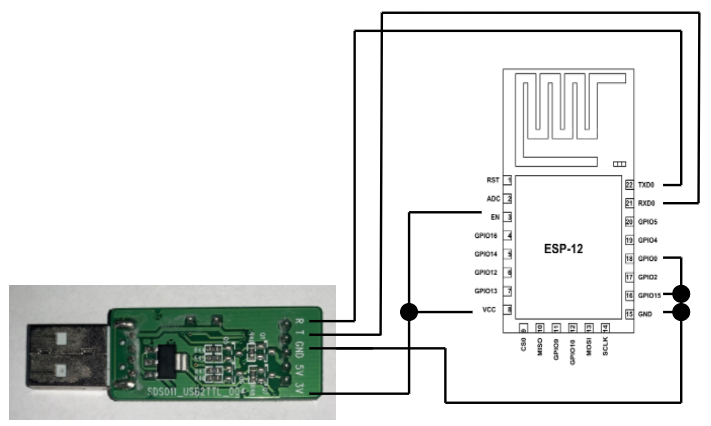
hardware/FlashWiring.png
