Noschvie/shrdzm/hardware/GatewayWiring.png

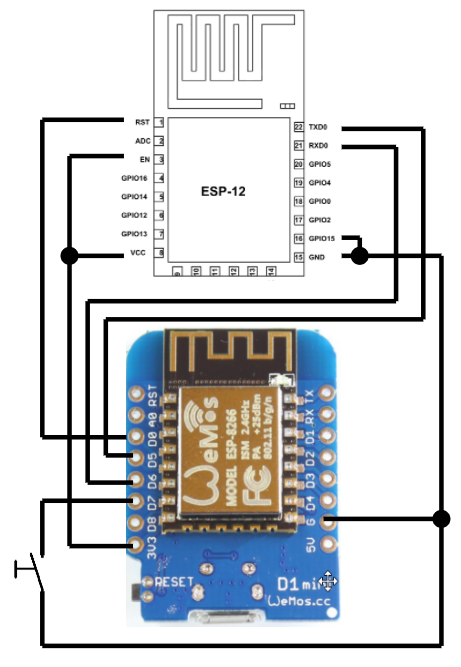
hardware/GatewayWiring.png
