Noschvie/shrdzm/hardware/MinimalGatewayWiring.png

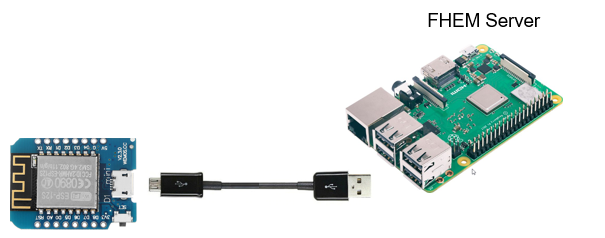
hardware/MinimalGatewayWiring.png
