Noschvie/shrdzm/hardware/MinimalSensorWiring.png

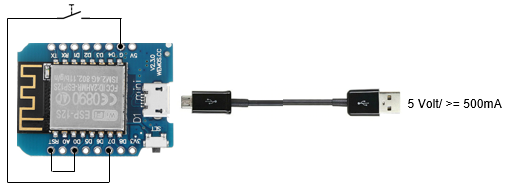
hardware/MinimalSensorWiring.png
