Noschvie/shrdzm/hardware/SDS011_Build.jpg

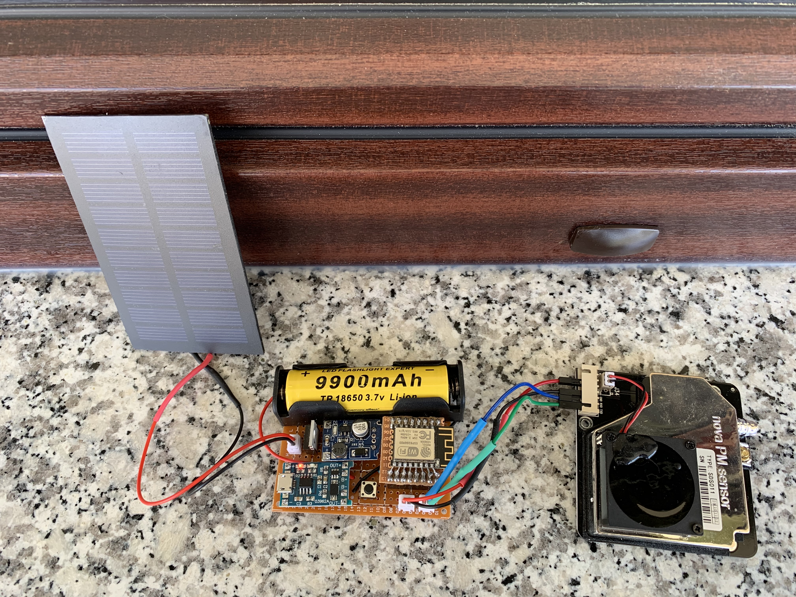
hardware/SDS011_Build.jpg
