Noschvie/shrdzm/hardware/SHRDZMGatewayMQTT_Debug1.png

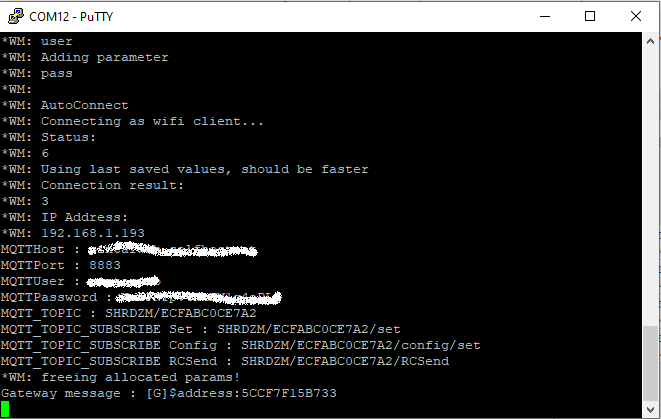
hardware/SHRDZMGatewayMQTT_Debug1.png
