Noschvie/shrdzm/hardware/SHRDZMGatewayMQTT_Debug2.png

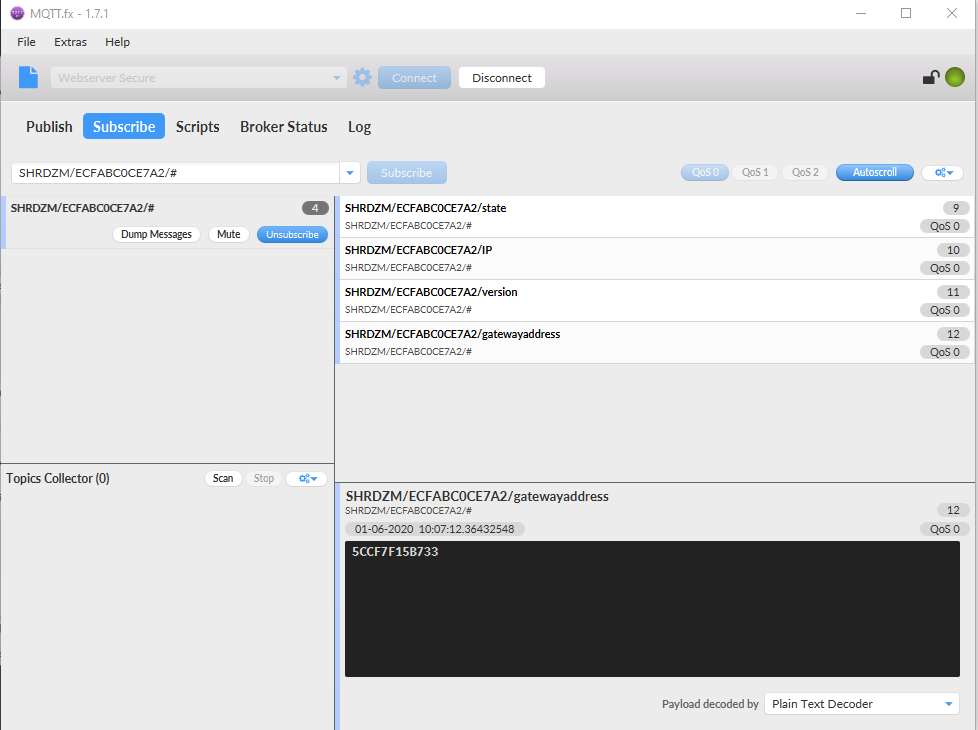
hardware/SHRDZMGatewayMQTT_Debug2.png
