Noschvie/shrdzm/KiCAD/Mainboard/SDS011/SDS011.kicad_pcb

## KiCad design KiCAD/Mainboard/SDS011/SDS011.kicad_pcb (2021-07-03)

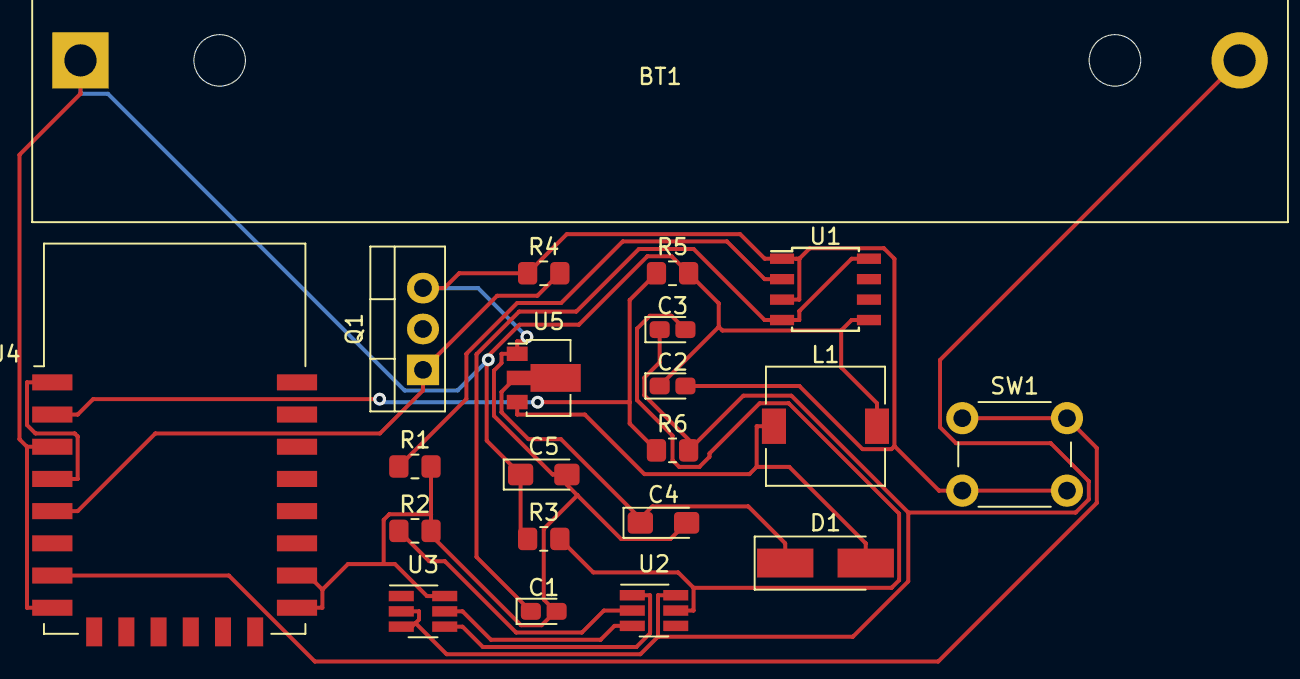
[picture p268: board SDS011.kicad_pcb from above]

Board: 2 copper layers, 21 parts (0 on the bottom side), 15 nets.

Parts:
BT1: Battery_Cell; BatteryHolder_MPD_BH-18650-PC2
C1, C3: 0.1uF; CP_EIA-1608-10_AVX-L_Pad1.25x1.05mm_HandSolder
C2: 10uF; CP_EIA-1608-10_AVX-L_Pad1.25x1.05mm_HandSolder
C4: 22uF; CP_EIA-3216-18_Kemet-A_Pad1.58x1.35mm_HandSolder
C5: 47uF; CP_EIA-3216-18_Kemet-A_Pad1.58x1.35mm_HandSolder
D1: D_Schottky; D_SMA_Handsoldering
L1: 100uH; L_7.3x7.3_H4.5
Q1: IRLZ44N; TO-220-3_Vertical
R1, R4: 10k; R_0805_2012Metric_Pad1.20x1.40mm_HandSolder
R2: 1k; R_0805_2012Metric_Pad1.20x1.40mm_HandSolder
R3: 100; R_0805_2012Metric_Pad1.20x1.40mm_HandSolder
R5: 330k; R_0805_2012Metric_Pad1.20x1.40mm_HandSolder
R6: 100k; R_0805_2012Metric_Pad1.20x1.40mm_HandSolder
SW1: Pairing; SW_PUSH_6mm
U1: TP4056; TP4056_SOP-8-PP
U2: DW01; SOT-23-6_Handsoldering
U3: FS8205A; SOT-23-6_Handsoldering
U4: ESP-12F; ESP-12E
U5: HT7750-1-SOT89; SOT-89-3

Connections:
unnamed: BT1.1, C2.1, C5.1, L1.2, R3.1, R5.2, U1.5, U4.3, U4.8
unnamed: BT1.2, C3.1, R6.2, U2.6, U3.2, U3.3
unnamed: C1.1, U1.4, U1.8
unnamed: C1.2, C2.2, C4.2, C5.2, Q1.3, R1.2, R2.2, R4.1, SW1.2, U1.1, U1.3, U3.6, U4.15, U4.16, U5.1
unnamed: C3.2, R3.2, U2.5
unnamed: C4.1, D1.1, U5.2
unnamed: D1.2, L1.1, U5.3
unnamed: Q1.1, R4.2, U4.5
unnamed: R1.1, U1.2
unnamed: R2.1, U2.2
unnamed: R5.1, R6.1, U4.2
unnamed: SW1.1, U4.7
unnamed: U2.1, U3.4
unnamed: U2.3, U3.5
unnamed: U4.1, U4.4
