Noschvie/shrdzm/KiCAD/IM350_AM550/IM350_AM550.kicad_pcb

## KiCad design KiCAD/IM350_AM550/IM350_AM550.kicad_pcb (2021-07-03)

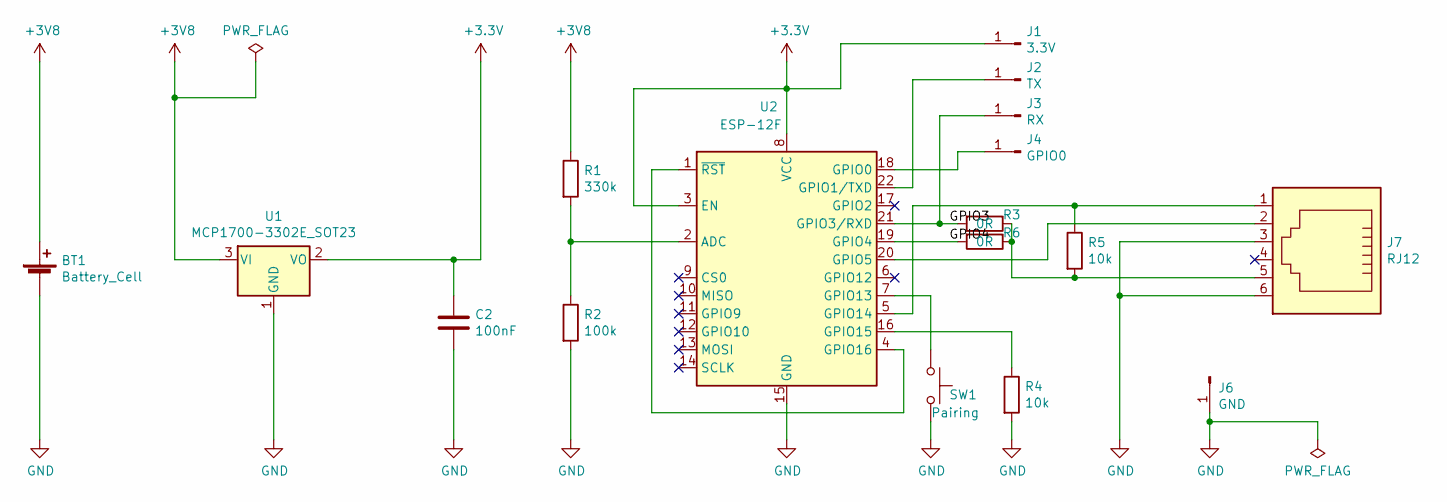
[picture p269: schematic IM350_AM550.sch]

Parts:
BT1: Battery_Cell; BatteryHolder_MPD_BH-18650-PC2_NoHole
C2: 100nF; C_1206_3216Metric_Pad1.33x1.80mm_HandSolder
J1: 3.3V; Pin_D1.3mm_L11.0mm_LooseFit
J2: TX; Pin_D1.3mm_L11.0mm_LooseFit
J3: RX; Pin_D1.3mm_L11.0mm_LooseFit
J4: GPIO0; Pin_D1.3mm_L11.0mm_LooseFit
J6: GND; Pin_D1.3mm_L11.0mm_LooseFit
J7: RJ12; RJ12_Amphenol_54601
R1: 330k; R_0805_2012Metric_Pad1.20x1.40mm_HandSolder
R2: 100k; R_0805_2012Metric_Pad1.20x1.40mm_HandSolder
R3, R6: 0R; R_0402_1005Metric_Pad0.72x0.64mm_HandSolder
R4, R5: 10k; R_0805_2012Metric_Pad1.20x1.40mm_HandSolder
SW1: Pairing; SW_SPST_CK_RS282G05A3
U1: MCP1700-3302E_SOT23; SOT-23_Handsoldering
U2: ESP-12F; ESP-12E

Connections:
+3V3: C2.1, J1.1, U1.2 (VO), U2.3 (EN), U2.8 (VCC)
+3V8: BT1.1 (+), R1.1, U1.3 (VI)
/GPIO3: J3.1, R3.2, U2.21 (GPIO3/RXD)
/GPIO4: R6.2, U2.19 (GPIO4)
GND: BT1.2 (-), C2.2, J6.1, J7.3, J7.6, R2.2, R4.2, SW1.2, U1.1 (GND), U2.15 (GND)
unnamed: J2.1, U2.22 (GPIO1/TXD)
unnamed: J4.1, U2.18 (GPIO0)
unnamed: J7.1, R5.1, U2.5 (GPIO14)
unnamed: J7.2, U2.20 (GPIO5)
unnamed: J7.5, R3.1, R5.2, R6.1
unnamed: R1.2, R2.1, U2.2 (ADC)
unnamed: R4.1, U2.16 (GPIO15)
unnamed: SW1.1, U2.7 (GPIO13)
unnamed: U2.1 (~RST), U2.4 (GPIO16)

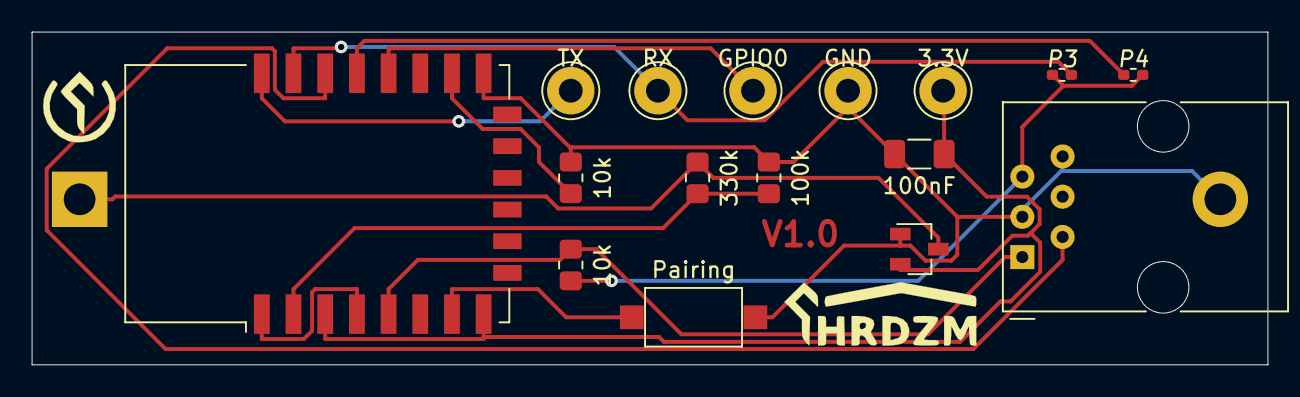
[picture p270: board IM350_AM550.kicad_pcb from above]

Board: 2 copper layers, 78.0 x 21.0 mm, 19 parts (1 on the bottom side), 14 nets.

Other parts of the board:
G1: LOGO; SHRDZM 12x4
G2: LOGO; SHRDZM Symbol 5x5
