Noschvie/shrdzm/KiCAD/Mainboard/Mainboard1/Mainboard1.kicad_pcb

## KiCad design KiCAD/Mainboard/Mainboard1/Mainboard1.kicad_pcb (2021-07-03)

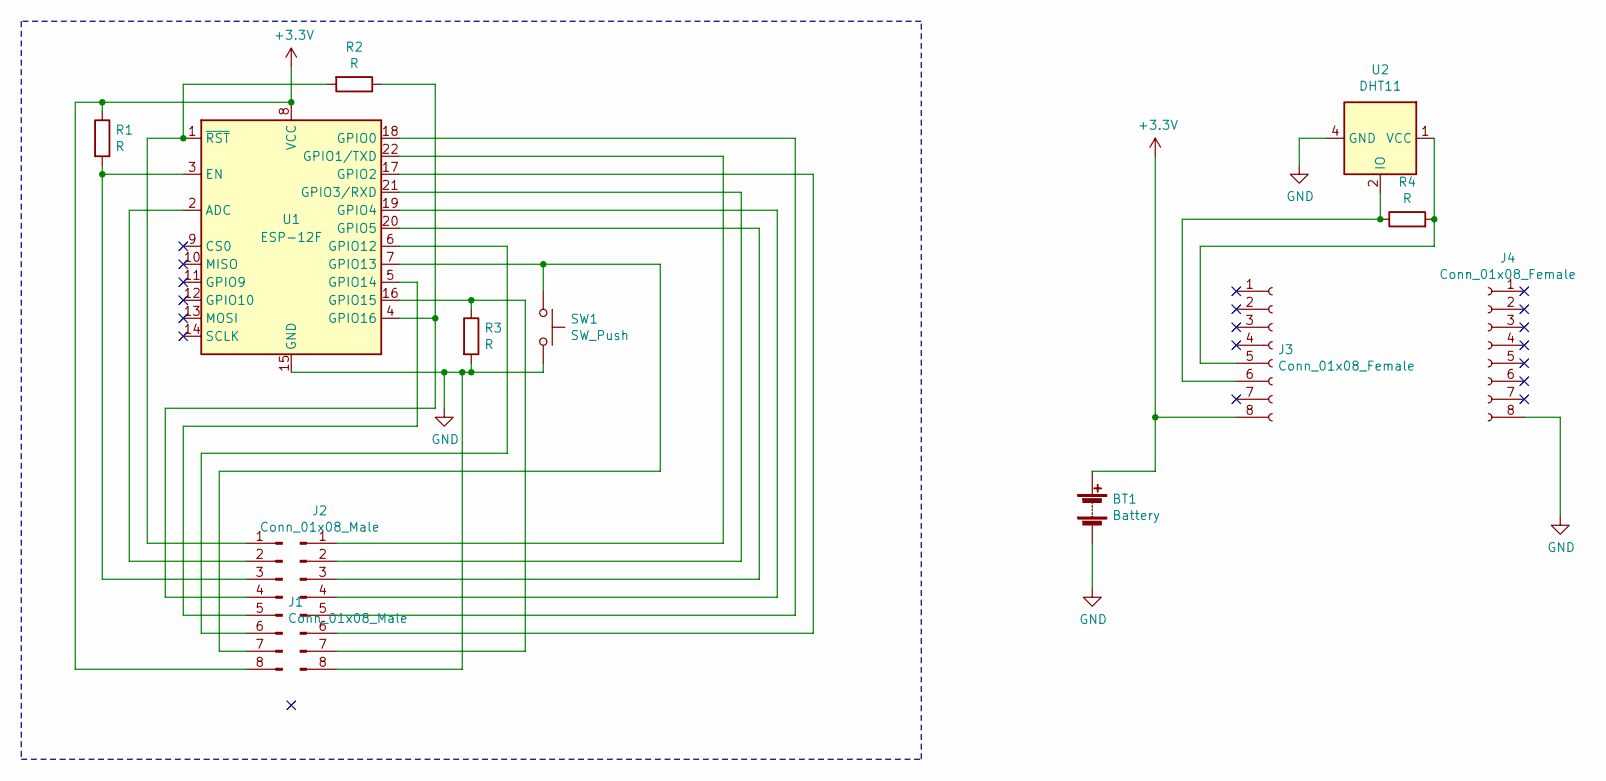
[picture p271: schematic Mainboard1.sch, SHRDZM Device Mainboard]

Parts:
BT1: Battery
J1, J2: Conn_01x08_Male; PinHeader_1x08_P2.54mm_Vertical
J3, J4: Conn_01x08_Female; PinSocket_1x08_P2.54mm_Vertical
R1, R2, R3: R; R_0603_1608Metric_Pad0.98x0.95mm_HandSolder
R4: R; R_Axial_DIN0207_L6.3mm_D2.5mm_P10.16mm_Horizontal
SW1: SW_Push; SW_SPST_CK_RS282G05A3
U1: ESP-12F; ESP-12E
U2: DHT11; Aosong_DHT11_5.5x12.0_P2.54mm

Connections:
+3V3: BT1.1 (+), J1.8, J3.8, R1.1, U1.8 (VCC)
GND: BT1.2 (-), J2.8, J4.8, R3.2, SW1.2, U1.15 (GND), U2.4 (GND)
unnamed: J1.1, R2.2, U1.1 (~RST)
unnamed: J1.2, U1.2 (ADC)
unnamed: J1.3, R1.2, U1.3 (EN)
unnamed: J1.4, R2.1, U1.4 (GPIO16)
unnamed: J1.5, U1.5 (GPIO14)
unnamed: J1.6, U1.6 (GPIO12)
unnamed: J1.7, SW1.1, U1.7 (GPIO13)
unnamed: J2.1, U1.22 (GPIO1/TXD)
unnamed: J2.2, U1.21 (GPIO3/RXD)
unnamed: J2.3, U1.20 (GPIO5)
unnamed: J2.4, U1.19 (GPIO4)
unnamed: J2.5, U1.18 (GPIO0)
unnamed: J2.6, U1.17 (GPIO2)
unnamed: J2.7, R3.1, U1.16 (GPIO15)
unnamed: J3.5, R4.2, U2.1 (VCC)
unnamed: J3.6, R4.1, U2.2 (IO)

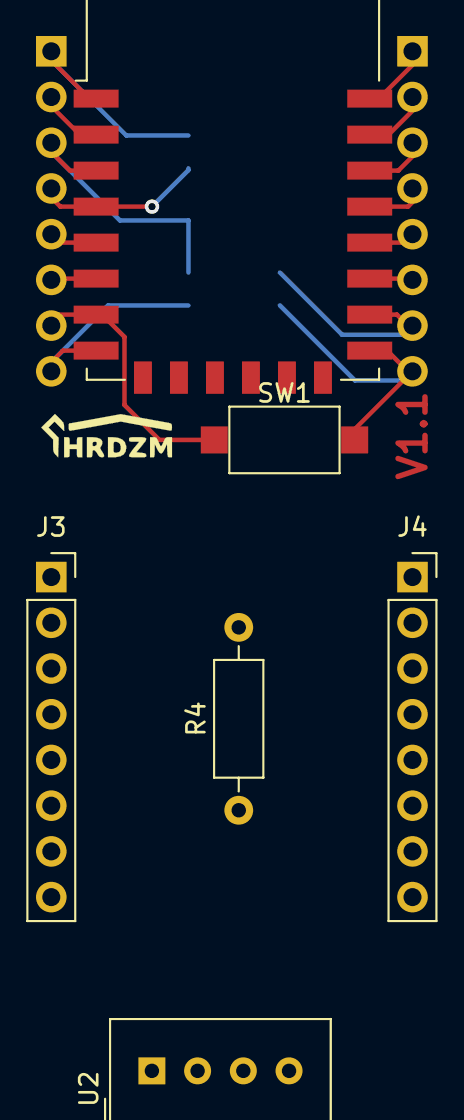
[picture p272: board Mainboard1.kicad_pcb from above]

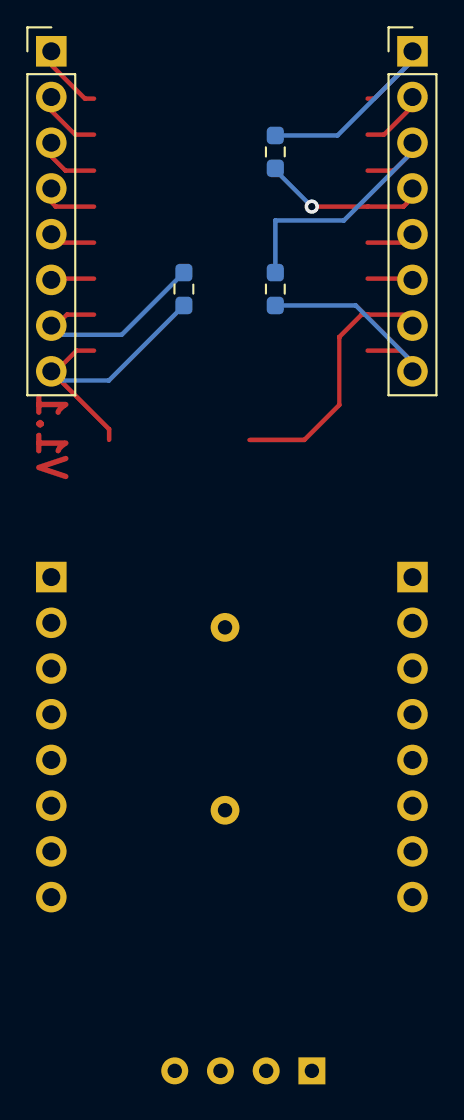
[picture p273: board Mainboard1.kicad_pcb from below]

Board: 2 copper layers, 11 parts (5 on the bottom side), 18 nets.
