Noschvie/shrdzm/KiCAD/Mainboard/DOORSENSOR_Enhanced/DOORSENSOR_Enhanced/DOORSENSOR_Enhanced.kicad_pcb

## KiCad design KiCAD/Mainboard/DOORSENSOR_Enhanced/DOORSENSOR_Enhanced/DOORSENSOR_Enhanced.kicad_pcb (2021-07-03)

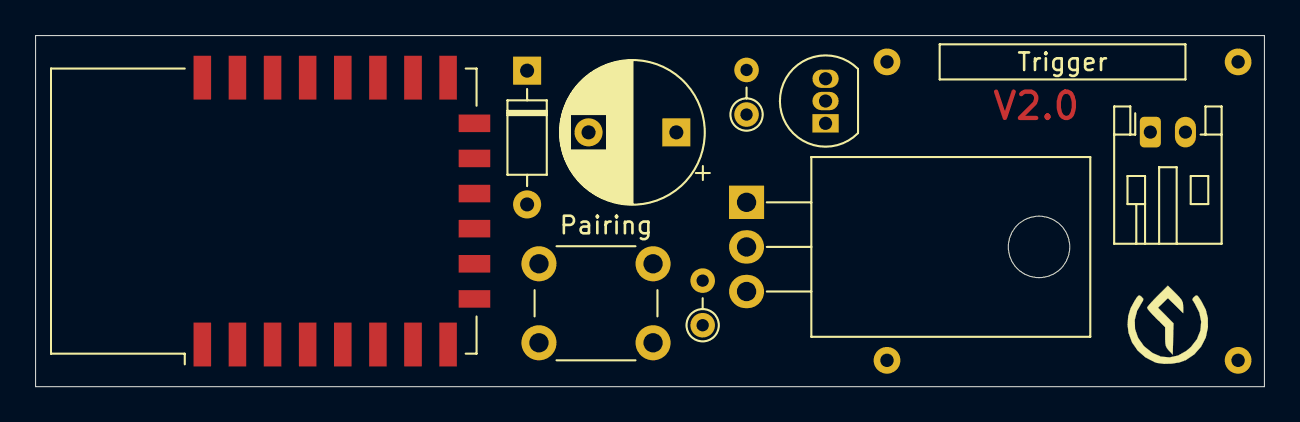
[picture p274: board DOORSENSOR_Enhanced.kicad_pcb from above]

Board: 2 copper layers, 70.0 x 20.0 mm, 11 parts (1 on the bottom side), 10 nets, no tracks yet.

Parts:
C1: 33uF; CP_Radial_D8.0mm_P5.00mm
D1: 1N4148; D_DO-35_SOD27_P7.62mm_Horizontal
J1: Power; JST_PH_S2B-PH-K_1x02_P2.00mm_Horizontal
Q1: 2N2222; TO-92_Inline
Q2: NDP6020P; TO-220-3_Horizontal_TabDown
R1: 10k; R_Axial_DIN0204_L3.6mm_D1.6mm_P2.54mm_Vertical
R2: 1k; R_Axial_DIN0204_L3.6mm_D1.6mm_P2.54mm_Vertical
SW1: Trigger; Magnetic Reed Relay
SW2: Pairing; SW_PUSH_6mm
SW3: Open/Close; Magnetic Reed Relay
U1: ESP-12F; ESP-12E

Connections:
+3V3: J1.2, Q2.3, R2.1, SW1.1
GND: C1.2, J1.1, Q1.1, SW2.2, SW3.2, U1.15, U1.16
unnamed: C1.1, D1.1, R1.2, SW1.2
unnamed: D1.2, U1.5
unnamed: Q1.2, R1.1
unnamed: Q1.3, Q2.1, R2.2
unnamed: Q2.2, U1.3, U1.8
unnamed: SW2.1, U1.7
unnamed: SW3.1, U1.20
unnamed: U1.1, U1.4
