Noschvie/shrdzm/KiCAD/Mainboard/IM350/IM350/IM350.kicad_pcb

## KiCad design KiCAD/Mainboard/IM350/IM350/IM350.kicad_pcb (2021-07-03)

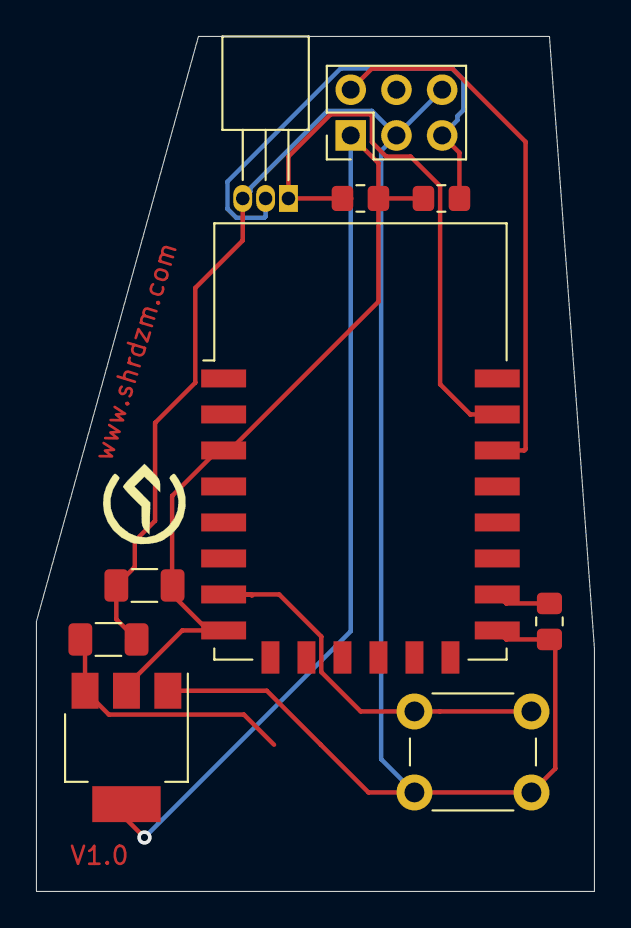
[picture p275: board IM350.kicad_pcb from above]

Board: 2 copper layers, 31.0 x 47.5 mm, 10 parts (0 on the bottom side), 8 nets.

Parts:
C1, C2: 22uF; C_1206_3216Metric_Pad1.33x1.80mm_HandSolder
J2: Conn_02x03_Odd_Even; PinHeader_2x03_P2.54mm_Vertical
Q1: BC547; TO-92_Inline_Horizontal1
R1, R2, R3: 10k; R_0805_2012Metric_Pad1.20x1.40mm_HandSolder
SW1: SW_Push; SW_PUSH_6mm
U1: AMS1117-3.3; SOT-223-3_TabPin2
U2: ESP-12F; ESP-12E

Connections:
+3V3: C2.1, J2.1, R1.1, R2.2, U1.2, U2.3, U2.8
+5V: C1.2, U1.3
GND: C1.1, C2.2, J2.3, J2.6, Q1.3, R3.1, SW1.2, U1.1, U2.15
unnamed: J2.2, U2.20
unnamed: J2.5, Q1.2, R2.1
unnamed: Q1.1, R1.2, U2.21
unnamed: R3.2, U2.16
unnamed: SW1.1, U2.7
