Noschvie/shrdzm/KiCAD/Mainboard/Mainboard.kicad_pcb

## KiCad design KiCAD/Mainboard/Mainboard.kicad_pcb (2021-07-03)

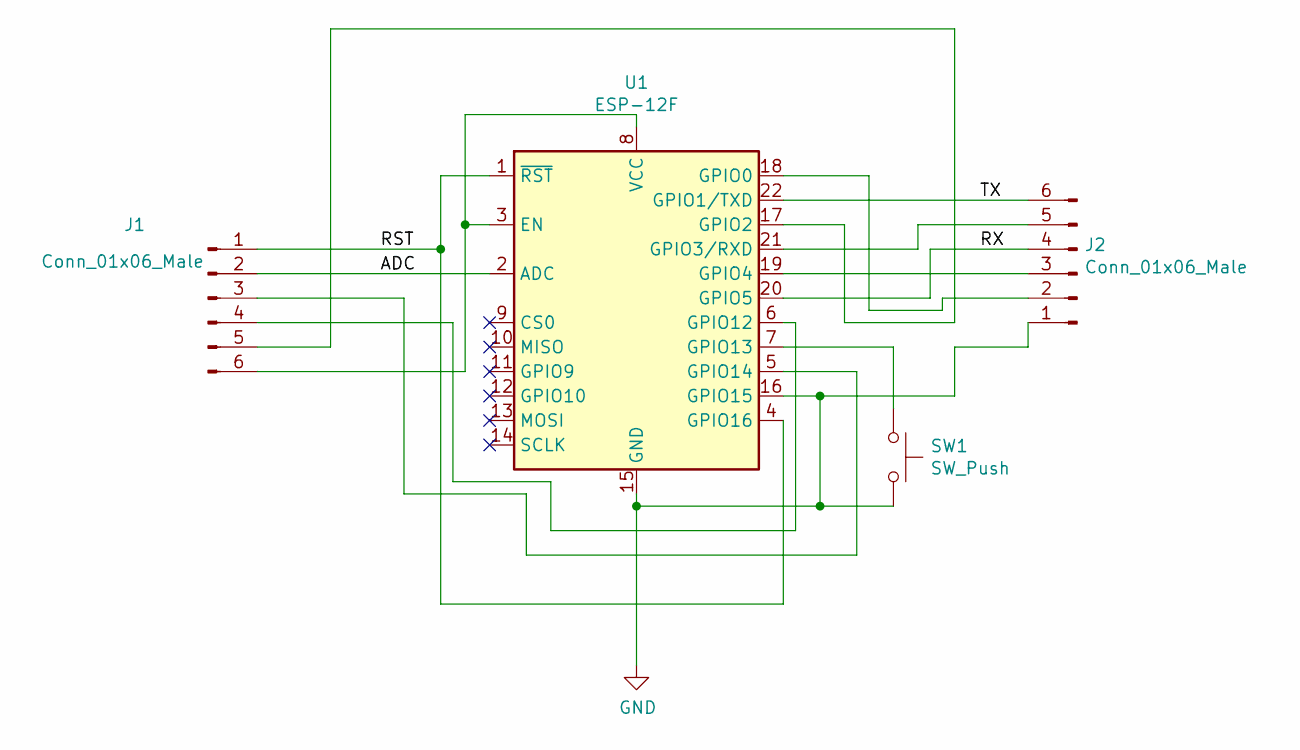
[picture p276: schematic Mainboard.sch, SHRDZM Mainboard]

Parts:
J1, J2: Conn_01x06_Male; PinHeader_1x06_P2.54mm_Vertical
SW1: SW_Push; SW_SPST_CK_RS282G05A3
U1: ESP-12F; ESP-12E

Connections:
/ADC: J1.2, U1.2 (ADC)
/RST: J1.1, U1.1 (~RST), U1.4 (GPIO16)
/RX: J2.4, U1.20 (GPIO5)
/TX: J2.6, U1.22 (GPIO1/TXD)
GND: J2.1, SW1.2, U1.15 (GND), U1.16 (GPIO15)
unnamed: J1.3, U1.5 (GPIO14)
unnamed: J1.4, U1.6 (GPIO12)
unnamed: J1.5, U1.17 (GPIO2)
unnamed: J1.6, U1.3 (EN), U1.8 (VCC)
unnamed: J2.2, U1.18 (GPIO0)
unnamed: J2.3, U1.19 (GPIO4)
unnamed: J2.5, U1.21 (GPIO3/RXD)
unnamed: SW1.1, U1.7 (GPIO13)

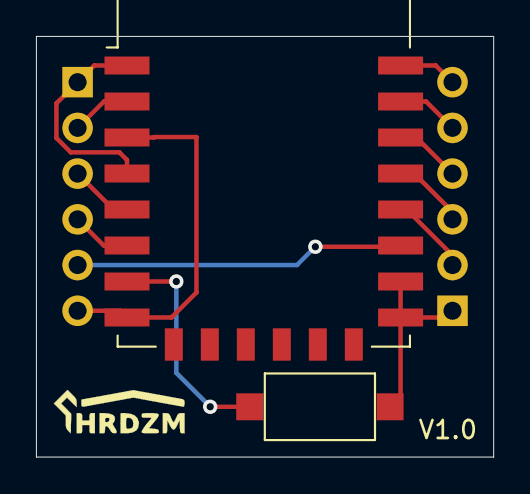
[picture p277: board Mainboard.kicad_pcb from above]

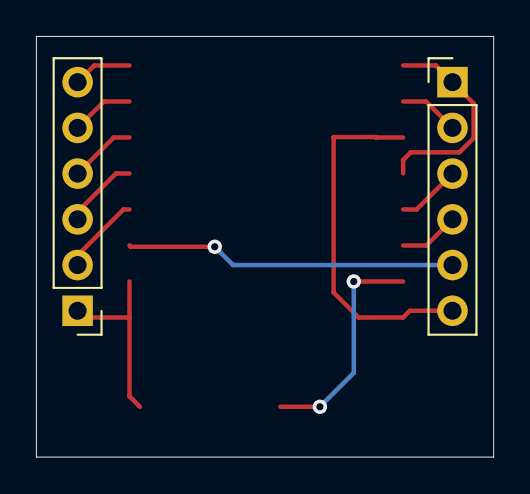
[picture p278: board Mainboard.kicad_pcb from below]

Board: 2 copper layers, 25.4 x 23.4 mm, 4 parts (2 on the bottom side), 13 nets.
