Noschvie/shrdzm/KiCAD/RainSensor/RainSensor.kicad_pcb

## KiCad design KiCAD/RainSensor/RainSensor.kicad_pcb (2021-07-03)

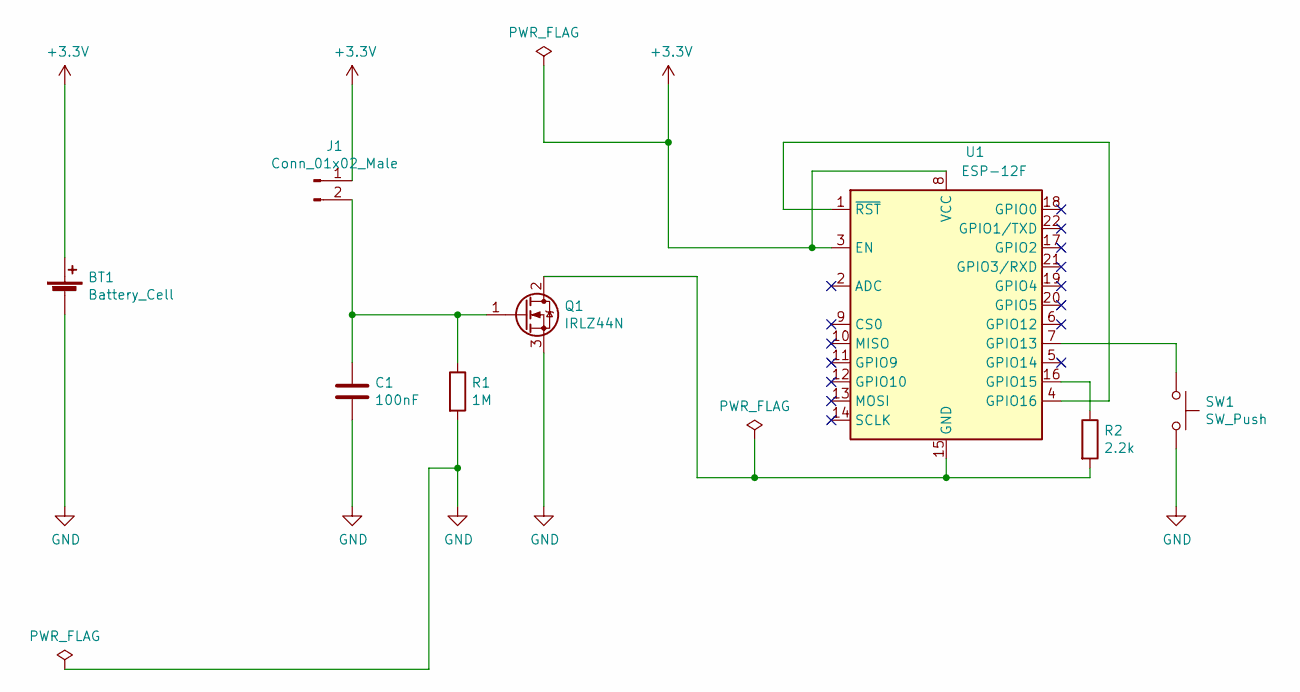
[picture p279: schematic RainSensor.sch]

Parts:
BT1: Battery_Cell; BatteryHolder_MPD_BH-18650-PC2
C1: 100nF; C_0805_2012Metric_Pad1.18x1.45mm_HandSolder
J1: Conn_01x02_Male; JST_PH_B2B-PH-K_1x02_P2.00mm_Vertical
Q1: IRLZ44N; TO-220-3_Horizontal_TabDown
R1: 1M; R_0805_2012Metric_Pad1.20x1.40mm_HandSolder
R2: 2.2k; R_0805_2012Metric_Pad1.20x1.40mm_HandSolder
SW1: SW_Push; SW_PUSH_6mm
U1: ESP-12F; ESP-12E

Connections:
+3V3: BT1.1 (+), J1.1, U1.3 (EN), U1.8 (VCC)
GND: BT1.2 (-), C1.2, Q1.3 (S), R1.2, SW1.2
unnamed: C1.1, J1.2, Q1.1 (G), R1.1
unnamed: Q1.2 (D), R2.2, U1.15 (GND)
unnamed: R2.1, U1.16 (GPIO15)
unnamed: SW1.1, U1.7 (GPIO13)
unnamed: U1.1 (~RST), U1.4 (GPIO16)

Board: 2 copper layers, 8 parts (1 on the bottom side), 7 nets, no tracks yet.
