Noschvie/shrdzm/KiCAD/IM350_AM550_T210_5V_V5.0/IM350_AM550_T210_5V_V5.0_multi.kicad_pcb

## KiCad design KiCAD/IM350_AM550_T210_5V_V5.0/IM350_AM550_T210_5V_V5.0_multi.kicad_pcb (2021-11-23)

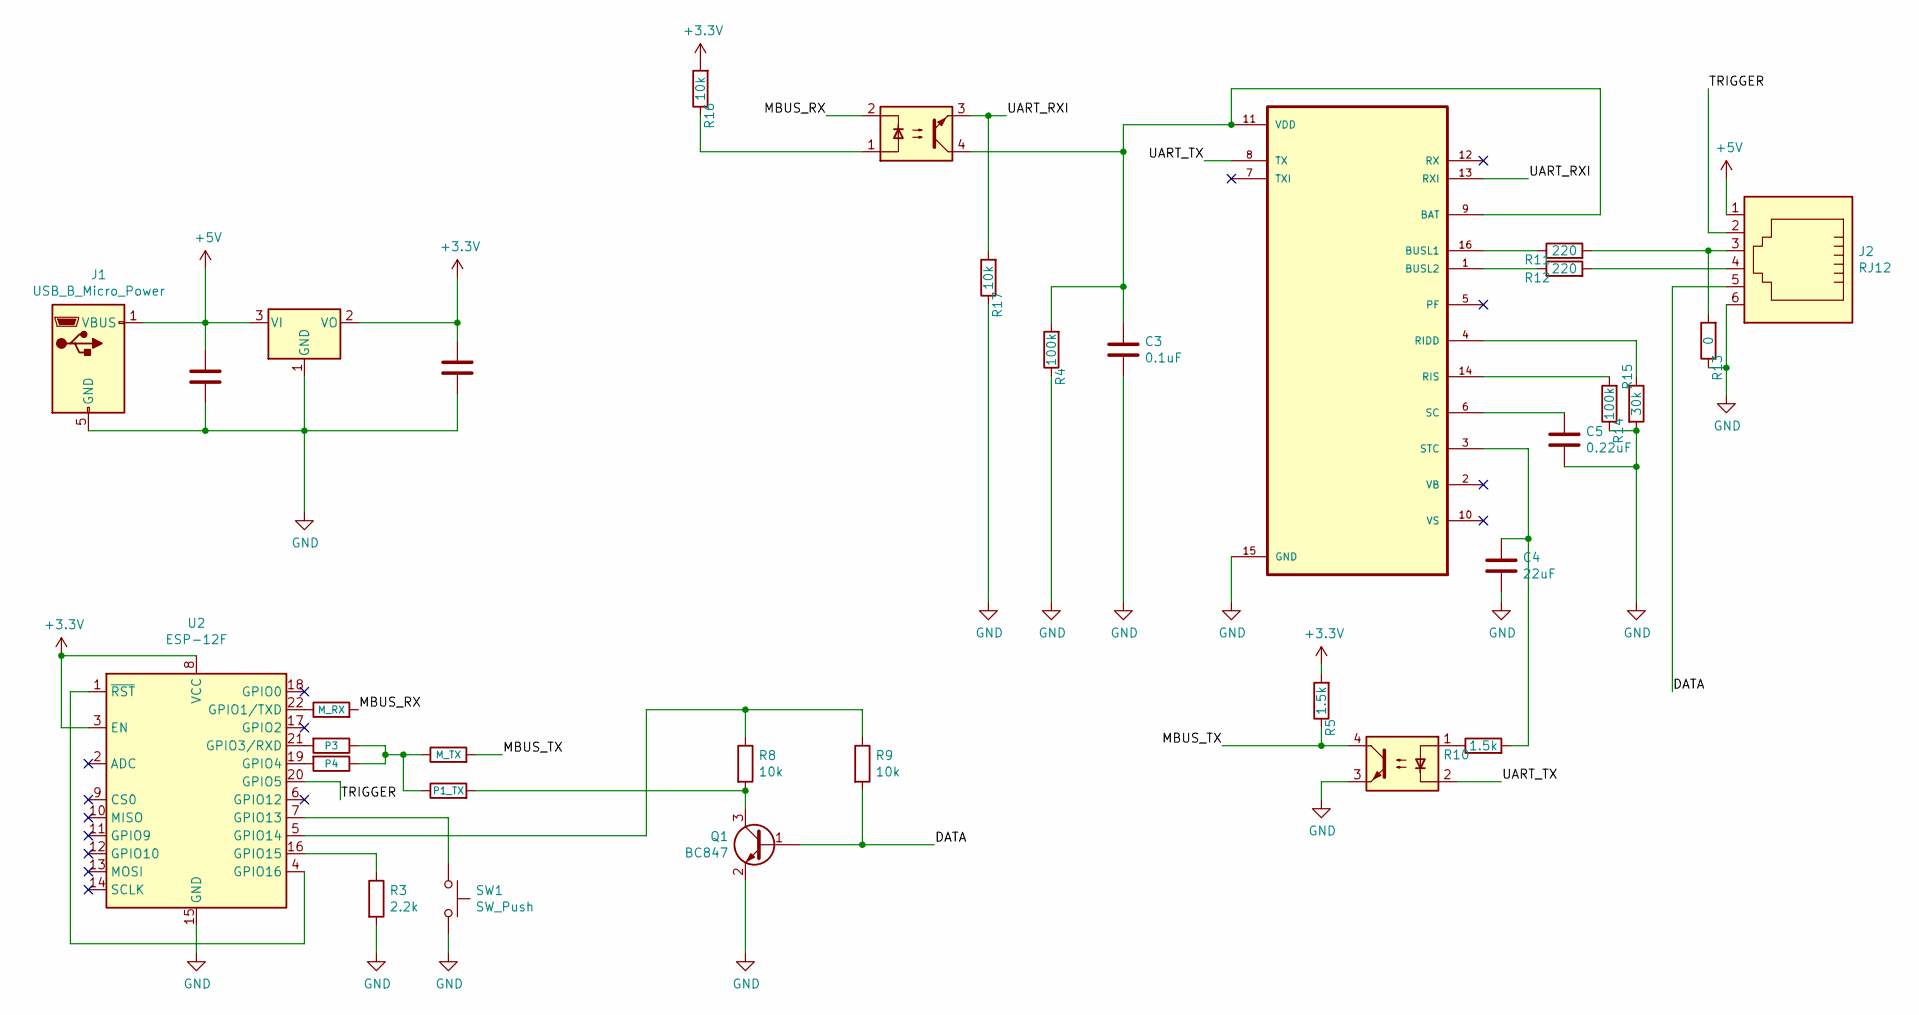
[picture p280: schematic IM350_AM550_T210_5V_V5.0.sch]

Parts:
C1, C2, C4: 22uF; C_1206_3216Metric_Pad1.33x1.80mm_HandSolder
C3: 0.1uF; C_1206_3216Metric_Pad1.33x1.80mm_HandSolder
C5: 0.22uF; C_1206_3216Metric_Pad1.33x1.80mm_HandSolder
J1: USB_B_Micro_Power; USB_Micro-B_Power
J2: RJ12; RJ12_Amphenol_54601
Q1: BC847; SOT-23
R1: P3; R_0201_0603Metric_Pad0.64x0.40mm_HandSolder
R2: P4; R_0201_0603Metric_Pad0.64x0.40mm_HandSolder
R3: 2.2k; R_0805_2012Metric_Pad1.20x1.40mm_HandSolder
R4, R14: 100k; R_0805_2012Metric_Pad1.20x1.40mm_HandSolder
R5, R10: 1.5k; R_0805_2012Metric_Pad1.20x1.40mm_HandSolder
R6: M_TX; R_0201_0603Metric_Pad0.64x0.40mm_HandSolder
R7: P1_TX; R_0201_0603Metric_Pad0.64x0.40mm_HandSolder
R8, R9, R16, R17: 10k; R_0805_2012Metric_Pad1.20x1.40mm_HandSolder
R11, R12: 220; R_0805_2012Metric_Pad1.20x1.40mm_HandSolder
R13: 0; R_0201_0603Metric_Pad0.64x0.40mm_HandSolder
R15: 30k; R_0805_2012Metric_Pad1.20x1.40mm_HandSolder
R18: M_RX; R_0201_0603Metric_Pad0.64x0.40mm_HandSolder
SW1: SW_Push; SW_SPST_CK_RS282G05A3
U1: AMS1117-3.3; SOT-223-3_TabPin2
U2: ESP-12F; ESP-12E
U3: TSS721ADR; SOIC127P600X175-16N
U4, U5: EL357NC; SOIC-4_4.55x2.6mm_P1.27mm

Connections:
+3V3: C1.1, R5.2, R16.2, U1.2 (VO), U2.3 (EN), U2.8 (VCC)
+5V: C2.1, J1.1 (VBUS), J2.1, U1.3 (VI)
/DATA: J2.5, Q1.1 (B), R9.2
/MBUS_RX: R18.2, U5.2
/MBUS_TX: R5.1, R6.2, U4.4
/TRIGGER: J2.2, U2.20 (GPIO5)
/UART_RXI: R17.2, U3.13 (RXI), U5.3
/UART_TX: U3.8 (TX), U4.2
GND: C1.2, C2.2, C3.2, C4.2, C5.2, J1.5 (GND), J2.6, Q1.2 (E), R3.2, R4.1, R13.1, R14.1, R15.2, R17.1, SW1.2, U1.1 (GND), U2.15 (GND), U3.15 (GND), U4.3; also elsewhere on the board
unnamed: C3.1, R4.2, U3.9 (BAT), U3.11 (VDD), U5.4
unnamed: C4.1, R10.2, U3.3 (STC)
unnamed: C5.1, U3.6 (SC)
unnamed: J2.4, R12.2
unnamed: Q1.3 (C), R7.2, R8.2
unnamed: R1.1, R2.1, R6.1, R7.1
unnamed: R1.2, U2.21 (GPIO3/RXD)
unnamed: R2.2, U2.19 (GPIO4)
unnamed: R3.1, U2.16 (GPIO15)
unnamed: R8.1, R9.1, U2.5 (GPIO14)
unnamed: R10.1, U4.1
unnamed: R11.1, U3.16 (BUSL1)
unnamed: R12.1, U3.1 (BUSL2)
unnamed: R14.2, U3.14 (RIS)
unnamed: R15.1, U3.4 (RIDD)
unnamed: R16.1, U5.1
unnamed: R18.1, U2.22 (GPIO1/TXD)
unnamed: SW1.1, U2.7 (GPIO13)
unnamed: U2.1 (~RST), U2.4 (GPIO16)

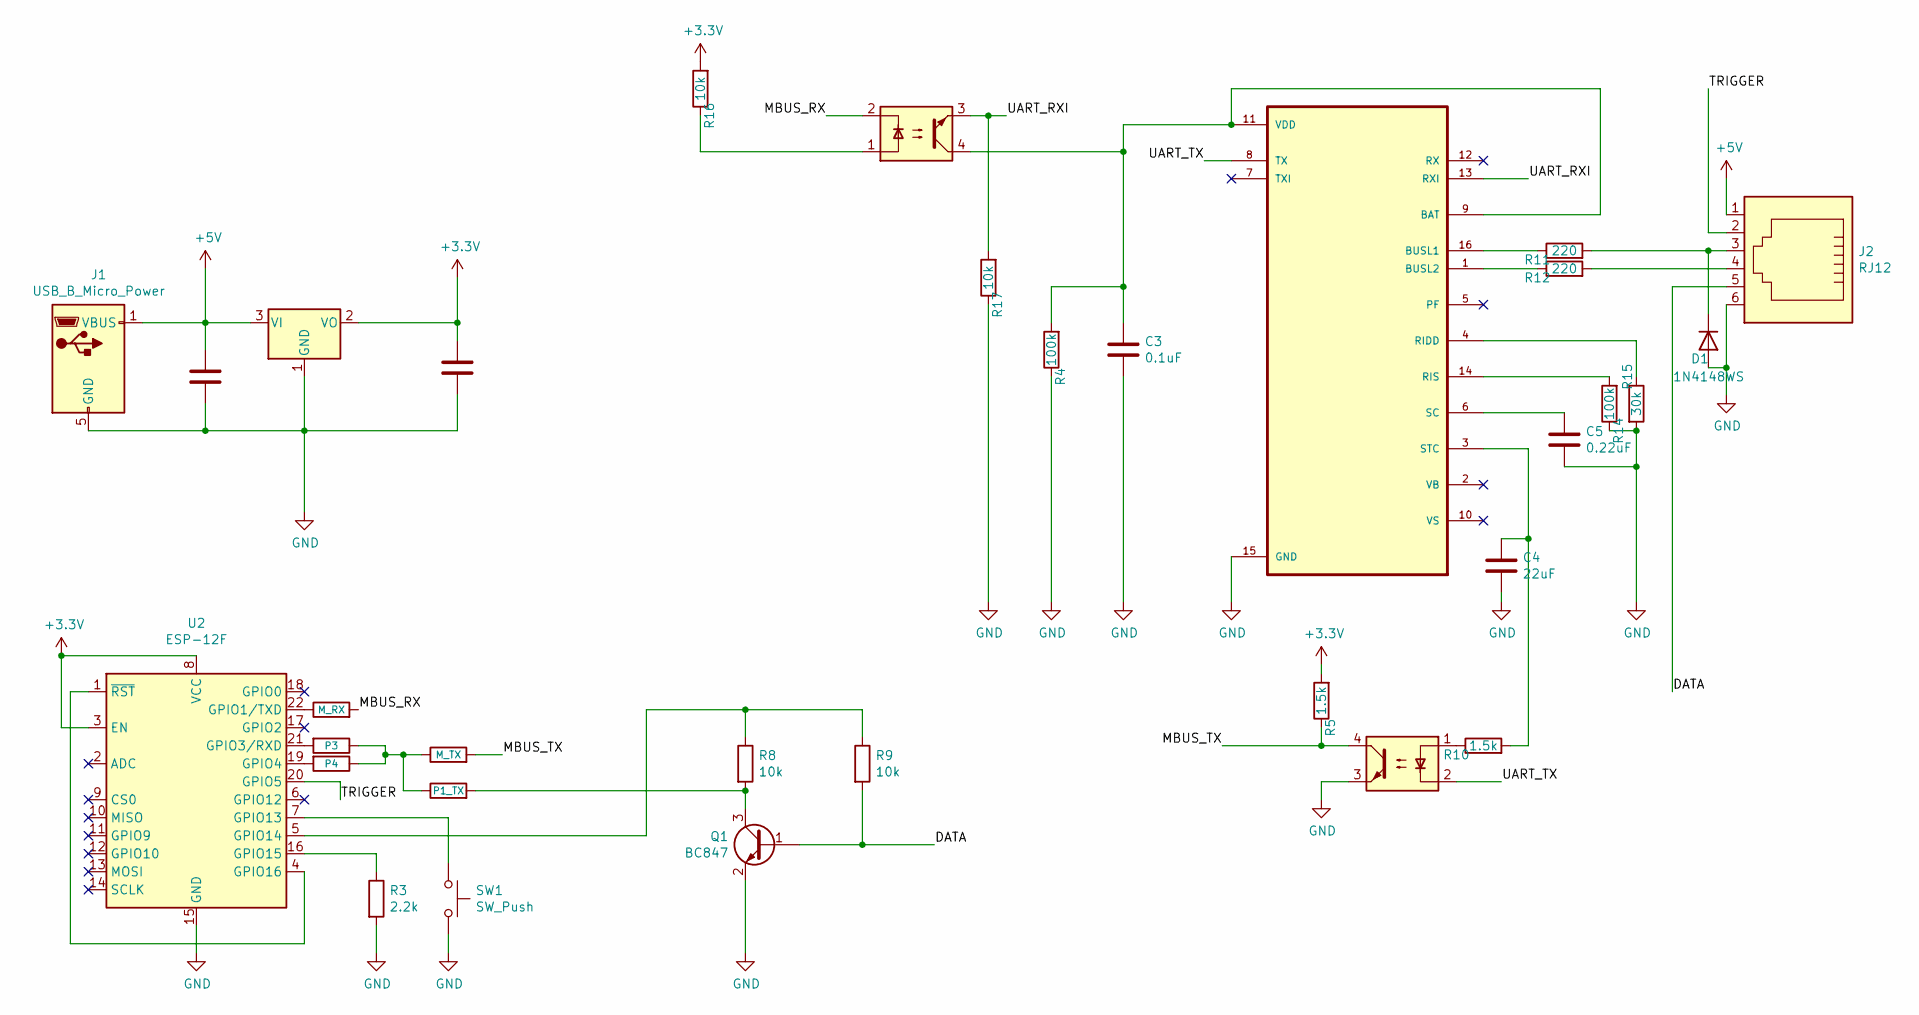
[picture p281: schematic IM350_AM550_T210_5V_V5.1.sch]

Parts:
C1, C2, C4: 22uF; C_1206_3216Metric_Pad1.33x1.80mm_HandSolder
C3: 0.1uF; C_1206_3216Metric_Pad1.33x1.80mm_HandSolder
C5: 0.22uF; C_1206_3216Metric_Pad1.33x1.80mm_HandSolder
D1: 1N4148WS; D_SOD-323_HandSoldering
J1: USB_B_Micro_Power; USB_Micro-B_Power
J2: RJ12; RJ12_Amphenol_54601
Q1: BC847; SOT-23
R1: P3; R_0201_0603Metric_Pad0.64x0.40mm_HandSolder
R2: P4; R_0201_0603Metric_Pad0.64x0.40mm_HandSolder
R3: 2.2k; R_0805_2012Metric_Pad1.20x1.40mm_HandSolder
R4, R14: 100k; R_0805_2012Metric_Pad1.20x1.40mm_HandSolder
R5, R10: 1.5k; R_0805_2012Metric_Pad1.20x1.40mm_HandSolder
R6: M_TX; R_0201_0603Metric_Pad0.64x0.40mm_HandSolder
R7: P1_TX; R_0201_0603Metric_Pad0.64x0.40mm_HandSolder
R8, R9, R16, R17: 10k; R_0805_2012Metric_Pad1.20x1.40mm_HandSolder
R11, R12: 220; R_0805_2012Metric_Pad1.20x1.40mm_HandSolder
R15: 30k; R_0805_2012Metric_Pad1.20x1.40mm_HandSolder
R18: M_RX; R_0201_0603Metric_Pad0.64x0.40mm_HandSolder
SW1: SW_Push; SW_SPST_CK_RS282G05A3
U1: AMS1117-3.3; SOT-223-3_TabPin2
U2: ESP-12F; ESP-12E
U3: TSS721ADR; SOIC127P600X175-16N
U4, U5: EL357NC; SOIC-4_4.55x2.6mm_P1.27mm

Connections:
+3V3: C1.1, R5.2, R16.2, U1.2 (VO), U2.3 (EN), U2.8 (VCC)
+5V: C2.1, J1.1 (VBUS), J2.1, U1.3 (VI)
/DATA: J2.5, Q1.1 (B), R9.2
/MBUS_RX: R18.2, U5.2
/MBUS_TX: R5.1, R6.2, U4.4
/TRIGGER: J2.2, U2.20 (GPIO5)
/UART_RXI: R17.2, U3.13 (RXI), U5.3
/UART_TX: U3.8 (TX), U4.2
GND: C1.2, C2.2, C3.2, C4.2, C5.2, D1.2 (A), J1.5 (GND), J2.6, Q1.2 (E), R3.2, R4.1, R14.1, R15.2, R17.1, SW1.2, U1.1 (GND), U2.15 (GND), U3.15 (GND), U4.3; also elsewhere on the board
unnamed: C3.1, R4.2, U3.9 (BAT), U3.11 (VDD), U5.4
unnamed: C4.1, R10.2, U3.3 (STC)
unnamed: C5.1, U3.6 (SC)
unnamed: J2.4, R12.2
unnamed: Q1.3 (C), R7.2, R8.2
unnamed: R1.1, R2.1, R6.1, R7.1
unnamed: R1.2, U2.21 (GPIO3/RXD)
unnamed: R2.2, U2.19 (GPIO4)
unnamed: R3.1, U2.16 (GPIO15)
unnamed: R8.1, R9.1, U2.5 (GPIO14)
unnamed: R10.1, U4.1
unnamed: R11.1, U3.16 (BUSL1)
unnamed: R12.1, U3.1 (BUSL2)
unnamed: R14.2, U3.14 (RIS)
unnamed: R15.1, U3.4 (RIDD)
unnamed: R16.1, U5.1
unnamed: R18.1, U2.22 (GPIO1/TXD)
unnamed: SW1.1, U2.7 (GPIO13)
unnamed: U2.1 (~RST), U2.4 (GPIO16)

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
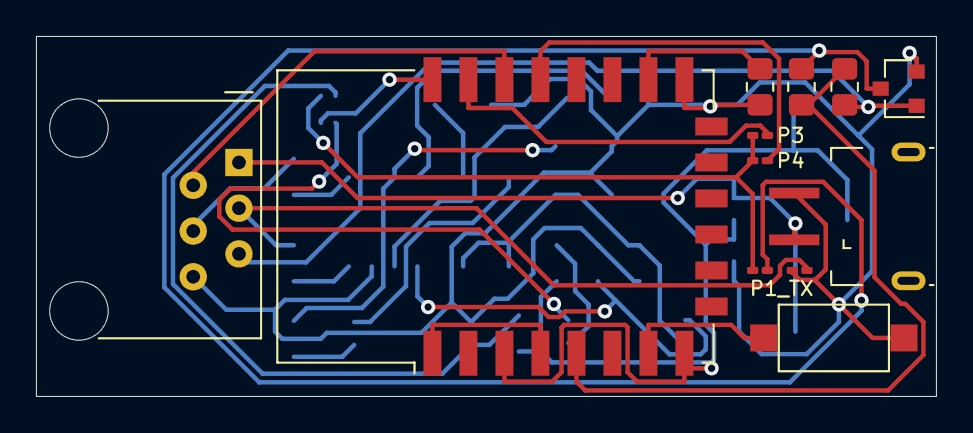
[picture p282: board IM350_AM550_T210_5V_V5.0_multi.kicad_pcb from above]

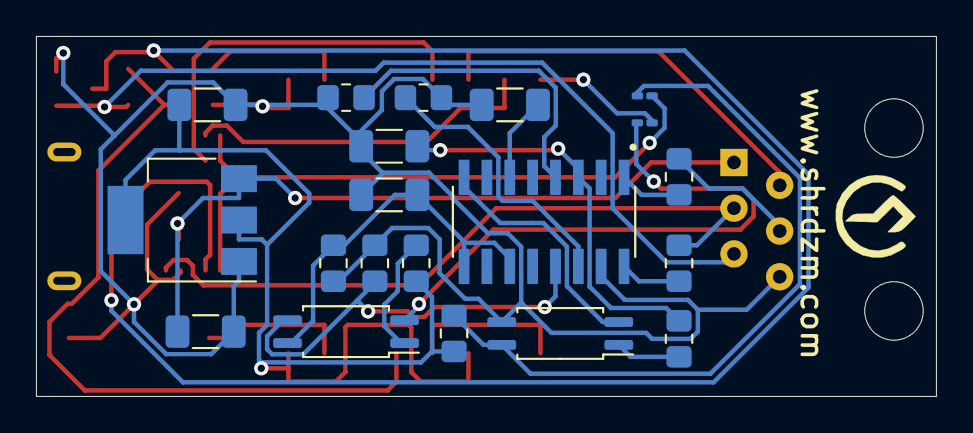
[picture p283: board IM350_AM550_T210_5V_V5.0_multi.kicad_pcb from below]

Board: 2 copper layers, 50.0 x 20.0 mm, 33 parts (21 on the bottom side), 29 nets.

Other parts of the board:
G1: LOGO; SHRDZM Symbol 5x5
