Noschvie/shrdzm/KiCAD/DOORSENSOR_Simple_9V/DOORSENSOR_Simple_9V_single.kicad_pcb

## KiCad design KiCAD/DOORSENSOR_Simple_9V/DOORSENSOR_Simple_9V_single.kicad_pcb (2021-07-03)

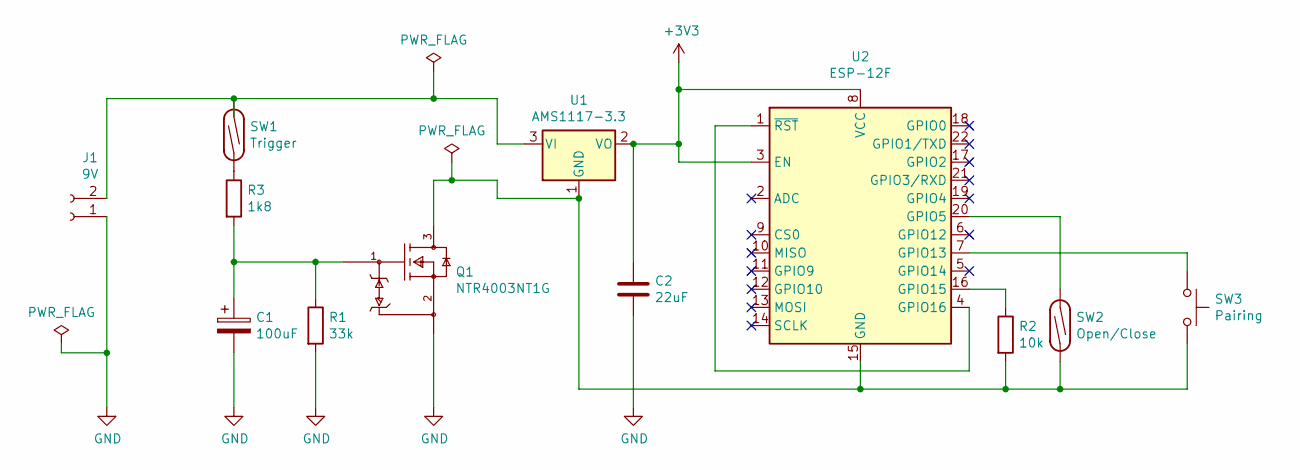
[picture p284: schematic DOORSENSOR_Simple_9V.sch]

Parts:
C1: 100uF; CP_Radial_D5.0mm_P2.50mm
C2: 22uF; C_1206_3216Metric_Pad1.33x1.80mm_HandSolder
J1: 9V; JST_PH_S2B-PH-K_1x02_P2.00mm_Horizontal
Q1: NTR4003NT1G; SOT-23; mouser part number 863-NTR4003NT1G; digikey description MOSFET N-CH 30V 500MA SOT-23
R1: 33k; R_0805_2012Metric_Pad1.20x1.40mm_HandSolder
R2: 10k; R_0805_2012Metric_Pad1.20x1.40mm_HandSolder
R3: 1k8; R_0805_2012Metric_Pad1.20x1.40mm_HandSolder
SW1: Trigger; Magnetic Reed Relay
SW2: Open/Close; Magnetic Reed Relay
SW3: Pairing; SW_SPST_CK_RS282G05A3
U1: AMS1117-3.3; SOT-223-3_TabPin2
U2: ESP-12F; ESP-12E

Connections:
+3V3: C2.1, U1.2 (VO), U2.3 (EN), U2.8 (VCC)
GND: C1.2, C2.2, J1.1, Q1.2 (S), R1.2
unnamed: C1.1, Q1.1 (G), R1.1, R3.2
unnamed: J1.2, SW1.1, U1.3 (VI)
unnamed: Q1.3 (D), R2.2, SW2.2, SW3.2, U1.1 (GND), U2.15 (GND)
unnamed: R2.1, U2.16 (GPIO15)
unnamed: R3.1, SW1.2
unnamed: SW2.1, U2.20 (GPIO5)
unnamed: SW3.1, U2.7 (GPIO13)
unnamed: U2.1 (~RST), U2.4 (GPIO16)

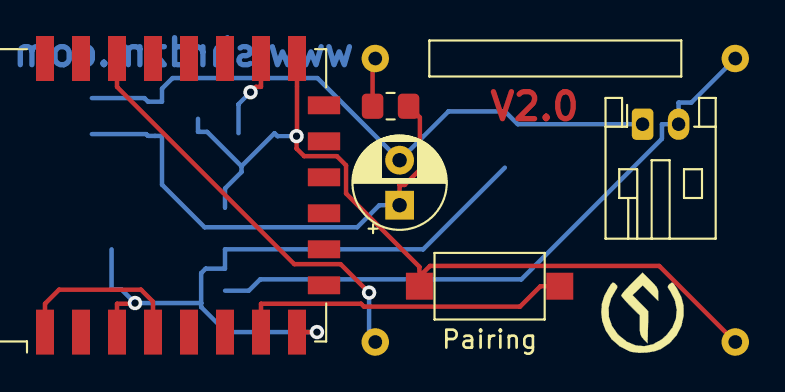
[picture p285: board DOORSENSOR_Simple_9V_single.kicad_pcb from above]

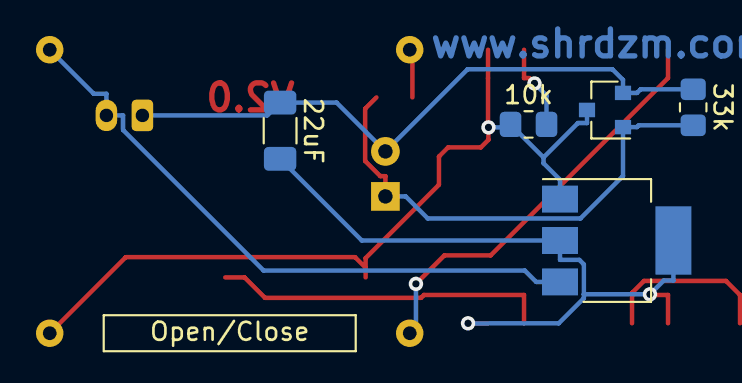
[picture p286: board DOORSENSOR_Simple_9V_single.kicad_pcb from below]

Board: 2 copper layers, 14 parts (7 on the bottom side), 10 nets.

Other parts of the board:
G1: LOGO; SHRDZM Symbol 5x5
G2: LOGO; SHRDZM 12x4
