Noschvie/shrdzm/code/SHRDZMDevice/Device_IM350.cpp

#include "Device_IM350.h"

#define UART_RXD_INV (BIT(19)) 
#define DEBUG_SHRDZM

const byte firstByte = 0x7E; 
const byte firstByteSagemcom = 0xDB; 
const byte lastByte = 0x7E; 
const int lenNormal = 123;
const int lenSagemcom = 511;

/*Vector_GCM Vector_SM;
GCM<AES128> *gcmaes128 = 0;
*/

  // IM350
//  String c2 = "7EA079CF0002002313D986E6E700DB08534D53677004C4465F200001A92916FC1EF62AB5F476F8A59772745CC99365500ACF5EBEEA82F95581762C2D18804A1E7F7700FB10752F04D9344779C6A332C973EAF3CF375095D1821E87C68909EE47759AD925976C42E4D92FF9727E4213FDEE5F1ABE45D9D97F5E5E7E";
//  String c2 = "7EA079CF0002002313D986E6E700DB08534D53677004C4465F200001A92A57400A90D827A575C749DAB31F44F3C4B83D9B15F9FD20D9FE147F5AD3A0432A65208408AE177E31AF4CD985DAD92F7647BB5ED8F619F629059606BBC55128D5E9A23BB992F564D098BBE8E759ECC0A01B259A02599A236EC45475A07E";
//  String c1 = "7EA079CF0002002313D986E6E700DB08534D53677004C4465F200001A92A57400A90D827A575C749DAB31F44F3C4B83D9B15F9FD20D9FE147F5AD3A0432A65208408AE177E31AF4CD985DAD92F7647BB5ED8F619F629059606BBC55128D5E9A23BB992F564D098BBE8E759ECC0A01B259A02599A236EC45475A07E";  
//  String ckSimulation = "612888F59306A7855AC5C08CB3A96B39"; // IM350
//    String adSimulation = "D0D1D2D3D4D5D6D7D8D9DADBDCDDDEDF"; // IM350

  // AM550
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
       codeBuffer[0] == 'y' ||
       codeBuffer[0] == '1' ||
       codeBuffer[0] == 'T' ||
       codeBuffer[0] == 't'
       )
    {
      obj[F("invertrx")] = F("YES");
      inverted = true;
    }
    else
    {
      obj[F("invertrx")] = F("NO");
    }    
  }  

  if(obj.containsKey(F("rxpin")))
  {
    if(obj[F("rxpin")].as<uint8_t>() != 3) // if not pin 3, software serial is needed
    {
      mySoftwareSerial.enableIntTx(false);
      mySoftwareSerial.begin(baud, SWSERIAL_8N1, obj[F("rxpin")].as<uint8_t>(), -1, inverted, 256);
      mySoftwareSerial.enableIntTx(false);
      softwareSerialUsed = true;    
    }
    else
    {
      if(inverted)
      {
        U0C0 = BIT(UCBN) | BIT(UCBN+1) | BIT(UCSBN); 
      }      
    }
  }  

  DeviceBase::setDeviceParameter(obj);

  if(m_pConfigurationObject != NULL)
    interval = atoi((*m_pConfigurationObject)["interval"]);

  return true;
}

void Device_IM350::prepare()
{
}

bool Device_IM350::initialize()
{
  deviceParameter = doc.to<JsonObject>();
  deviceParameter[F("baud")] = F("115200");
  deviceParameter[F("requestpin")] = F("5");
  deviceParameter[F("cipherkey")] = F("00000000000000000000000000000000");
  deviceParameter[F("rxpin")] = F("3");
  deviceParameter[F("invertrx")] = F("NO");
  deviceParameter[F("sendRawData")] = F("NO");
  deviceParameter[F("autoRebootMinutes")] = F("0");

  return true;
}

SensorData* Device_IM350::readParameterTypes()
{
  SensorData *al = new SensorData(6);

  al->di[0].nameI = F("counter_reading_p_in");
  al->di[1].nameI = F("counter_reading_p_out");
  al->di[2].nameI = F("counter_reading_q_in");
  al->di[3].nameI = F("counter_reading_q_out");
  al->di[4].nameI = F("current_power_usage_in");
  al->di[5].nameI = F("current_power_usage_out");

  return al;
}

SensorData* Device_IM350::readInitialSetupParameter()
{
  SensorData *al = new SensorData(1);

  al->di[0].nameI = F("interval");
  al->di[0].valueI = F("120");

  return al; 
}

SensorData* Device_IM350::readParameter()
{  
  SensorData *al = NULL;  
  char str[15] = "";
  devicetype dt = unknown;

  String ck = deviceParameter[F("cipherkey")];

  if(!deviceParameter[F("autoRebootMinutes")].isNull())
  {
    if(strcmp(deviceParameter[F("autoRebootMinutes")],"0") != 0)
    {
      // Check whether to reboot first
      if(millis() > (atol(deviceParameter[F("autoRebootMinutes")]) * 1000 * 60))
      {
        Serial.println(F("Will reboot now"));
        
        delay(500); 
        ESP.restart();      
      }
    }
  }

  if(ck == F("00000000000000000000000000000000") || ck.length() != 32)
  {
    al = new SensorData(2);
    
    al->di[0].nameI = F("lasterror");
    al->di[0].valueI = F("cipherkey not set!");  
    
    timeToString(str, sizeof(str));
    al->di[1].nameI = F("uptime");
    al->di[1].valueI = String(str);       

    return al;
  }

  digitalWrite(atoi(deviceParameter[F("requestpin")]), LOW);

  // clear serial buffer
  if(softwareSerialUsed)
  {
    mySoftwareSerial.flush();

    while(mySoftwareSerial.available() > 0)
    {
      byte trash = mySoftwareSerial.read();
    }
  }
  else
  {
    Serial.flush();
    while(Serial.available() > 0)
    {
      byte trash = Serial.read();
    }
    
    if(inverted)
      U0C0 = BIT(UCRXI) | BIT(UCBN) | BIT(UCBN+1) | BIT(UCSBN); 
  
    Serial.begin(baud);

    if(inverted)
      U0C0 = BIT(UCRXI) | BIT(UCBN) | BIT(UCBN+1) | BIT(UCSBN); 

    while(Serial.available() > 0)
    {
      byte trash = Serial.read();
    }
  }

  pinMode(LED_BUILTIN, OUTPUT); // LED als Output definieren

  // enable request
  digitalWrite(atoi(deviceParameter[F("requestpin")]), HIGH); 
  digitalWrite(LED_BUILTIN, LOW);
  
  uint32_t timeout=2000;

  bool finished = false;
  int readCnt = 0;
  uint32_t start_time = millis();
  byte tempChar = 0;
  byte *readMessage;
  uint32_t messageLen = 0;

  if(softwareSerialUsed)
    Serial.printf("SS baud = %d\n", mySoftwareSerial.baudRate());


  while ((tempChar != 0x7E  && tempChar != firstByteSagemcom) && (millis() - start_time < timeout)) 
  {
    if (softwareSerialUsed ? mySoftwareSerial.available() : Serial.available()) 
    {
      tempChar = softwareSerialUsed ? mySoftwareSerial.read() : Serial.read(); 
    }
  }

  start_time = millis();
  timeout = 1000;
  bool done = false;
  
  if (tempChar == firstByte) // if first byte == 0x7E
  {
    while ((millis() - start_time) < timeout && !done)
    {
      if (softwareSerialUsed ? mySoftwareSerial.available() : Serial.available()) 
      {
        tempChar = softwareSerialUsed ? mySoftwareSerial.read() : Serial.read(); // second byte must be 0xA0
        
        if(tempChar == 0xA0)
        {
          while ((millis() - start_time) < timeout && !done)
          {
            if (softwareSerialUsed ? mySoftwareSerial.available() : Serial.available()) 
            {
              tempChar = softwareSerialUsed ? mySoftwareSerial.read() : Serial.read(); // 3rd byte tells the legth of the message
    
              readMessage = new byte[tempChar+2];
              memset(readMessage, 0, tempChar+2);
              readMessage[0] = firstByte;
              readMessage[1] = 0xA0;
              readMessage[2] = tempChar;
              messageLen = ((uint32_t)(tempChar))+2;  
              readCnt = 3;
      
              while ( readCnt < messageLen && ((millis() - start_time) < timeout))  // minimum len 120 chars for 0x7E format
              {
                if (softwareSerialUsed ? mySoftwareSerial.available() : Serial.available()) 
                {
                  readMessage[readCnt] = softwareSerialUsed ? mySoftwareSerial.read() : Serial.read(); 
                  readCnt++; 
        
                  if(readCnt == tempChar+2 && readMessage[readCnt-1] != lastByte)
                  {
                    done = true;
                    Serial.printf("Wrong end byte found - %d\n", readMessage[readCnt-1]);  
                  }
                  else if(readCnt == tempChar+2)
                    done = true;
                }
              }
            }      
          }
        }
      }
    }    
  }  
  else if(tempChar == firstByteSagemcom)
  {
    readCnt++;

    readMessage = new byte[lenSagemcom];
    memset(readMessage, 0, lenSagemcom);
    readMessage[0] = tempChar;
    messageLen = lenSagemcom;
    
    while ( readCnt < lenSagemcom && (millis() - start_time < timeout+2000) ) 
    {
      if (softwareSerialUsed ? mySoftwareSerial.available() : Serial.available()) 
      {
        readMessage[readCnt] = softwareSerialUsed ? mySoftwareSerial.read() : Serial.read(); 
        readCnt++; 
      }
    }
  }    

  // disable read request as soon as we have finished the data collection

  digitalWrite(atoi(deviceParameter[F("requestpin")]), LOW); 
  digitalWrite(LED_BUILTIN, HIGH); 

  if(!softwareSerialUsed)
  {
    Serial.flush();
    Serial.end();
    Serial.begin(SERIAL_BAUD);
  }

  if(readCnt > 10)
  {  
    if(readMessage[0] == firstByteSagemcom)  
    {
      dt = sagemcom;
    }
    else if(readCnt == 123)
    {
      dt = im350;
    }
    else if(readCnt == 121)
    {
      dt = am550;
    }
    else if(readCnt == 114)
    {
      dt = im350Wels;
    }
  }

  if(readCnt == 0)
  {
    al = new SensorData(2);    
    
    al->di[0].nameI = F("lasterror");    
    al->di[0].valueI = F("No data read");  
            
    timeToString(str, sizeof(str));
    al->di[1].nameI = F("uptime");
    al->di[1].valueI = String(str);       
    
    return al;    
  }
  else if (dt == unknown)
  {
    if(!deviceParameter[F("sendRawData")].isNull() && strcmp(deviceParameter[F("sendRawData")],"YES") == 0)
    {    
      al = new SensorData(3);
      al->di[2].nameI = F("data");
      al->di[2].valueI = hexToString(readMessage, readCnt);
    }
    else
    {
      al = new SensorData(2);
    }
    
    al->di[0].nameI = F("lasterror");    
    al->di[0].valueI = F("No supported SmartMeter Type identified - No end Byte found");  

    timeToString(str, sizeof(str));
    al->di[1].nameI = F("uptime");
    al->di[1].valueI = String(str);       
    
    if(readCnt)
      delete readMessage;
            
    return al;
  }  
  else // IM350 or AM550 or T210 read
  {
    init_vector(&Vector_SM, m_blockCipherKey, readMessage, dt); 
    byte bufferResult[Vector_SM.datasize+1];
    memset(bufferResult, 0, Vector_SM.datasize+1);

    decrypt_text(&Vector_SM, bufferResult);

    if(dt == sagemcom)
    {
      char *posBuffer = NULL;
      int posBufferPosition = 0;

      if(bufferResult[0] != NULL && bufferResult[0] == 47) // first char must be a slash
      {
        posBuffer = strstr( (char *)bufferResult, "0-0:1.0.0" );  
      }
      
      if(posBuffer != NULL)
      {
        String data((char *)bufferResult);
        uint8_t counter = 0;
        
        posBufferPosition = posBuffer - (char *)bufferResult;
  
        data = "{"+data.substring(posBufferPosition);
        int endChar = data.lastIndexOf('!');

        if(endChar > 0)
        {
          data = data.substring(0, endChar-1);
          data.replace(",\r\n", "}");
        }
  
        data.replace("0-0:", "\"");
        data.replace("1-0:", "\"");
        data.replace("(", "\" : \"");
        data.replace(")", "\",");
        data.replace("*Wh", "");
        data.replace("*W", "");
        data.replace("*varh", "");
        data.replace("*var", "");

        
        DynamicJsonDocument doc(800);
        deserializeJson(doc, data);
        JsonObject obj = doc.as<JsonObject>();

        if(!deviceParameter[F("sendRawData")].isNull() && strcmp(deviceParameter[F("sendRawData")],"YES") == 0)
          al = new SensorData(obj.size()+2);
        else
          al = new SensorData(obj.size()+1);        
  
        for (JsonPair kv : obj) 
        {      
          al->di[counter].nameI = String(kv.key().c_str());
  
          if(strcmp(kv.key().c_str(), "1.0.0") == 0)
            al->di[counter].valueI = String(kv.value().as<char*>());
          else
            al->di[counter].valueI = String(atol(kv.value().as<char*>()), DEC);
          
          counter++;
        }

        if(!deviceParameter[F("sendRawData")].isNull() && strcmp(deviceParameter[F("sendRawData")],"YES") == 0)
        {
          al->di[counter].nameI = F("data");
          al->di[counter].valueI = hexToString(readMessage, readCnt);
          counter++;
        }
          
        timeToString(str, sizeof(str));
        al->di[counter].nameI = F("uptime");
        al->di[counter].valueI = String(str);       
      }
      else
      {
        if(!deviceParameter[F("sendRawData")].isNull() && strcmp(deviceParameter[F("sendRawData")],"YES") == 0)
          al = new SensorData(3);
        else
          al = new SensorData(2);
        
        
        al->di[0].nameI = F("lasterror");    
        al->di[0].valueI = F("cipherkey does not fit");        

        timeToString(str, sizeof(str));
        al->di[1].nameI = F("uptime");
        al->di[1].valueI = String(str);       

        if(!deviceParameter[F("sendRawData")].isNull() && strcmp(deviceParameter[F("sendRawData")],"YES") == 0)
        {
          al->di[2].nameI = F("data");
          al->di[2].valueI = hexToString(readMessage, readCnt);
        }
      }
    }
    else if((dt == am550 && 
              bufferResult[56] == 0x06 &&
              bufferResult[61] == 0x06 &&
              bufferResult[66] == 0x06 &&
              bufferResult[71] == 0x06) || dt == im350) // AM550/IM350 Carinthia
    {
      parse_message(bufferResult, dt);
   
      if(!deviceParameter[F("sendRawData")].isNull() && strcmp(deviceParameter[F("sendRawData")],"YES") == 0)
        al = new SensorData(9);
      else
        al = new SensorData(8);

      al->di[0].nameI = F("counter_reading_p_in");
      al->di[0].valueI = String(counter_reading_p_in);  
    
      al->di[1].nameI = F("counter_reading_p_out");
      al->di[1].valueI = String(counter_reading_p_out);  
    
      al->di[2].nameI = F("counter_reading_q_in");
      al->di[2].valueI = String(counter_reading_q_in);  
    
      al->di[3].nameI = F("counter_reading_q_out");
      al->di[3].valueI = String(counter_reading_q_out);  
    
      al->di[4].nameI = F("counter_power_usage_in");
      al->di[4].valueI = String(current_power_usage_in);  
    
      al->di[5].nameI = F("counter_power_usage_out");
      al->di[5].valueI = String(current_power_usage_out); 
    
      al->di[6].nameI = F("timestamp");
      al->di[6].valueI = String(meterTime); 
    
      timeToString(str, sizeof(str));
      al->di[7].nameI = F("uptime");
      al->di[7].valueI = String(str);    
         
      if(!deviceParameter[F("sendRawData")].isNull() && strcmp(deviceParameter[F("sendRawData")],"YES") == 0)
      {
        al->di[8].nameI = F("data");
        al->di[8].valueI = hexToString(readMessage, readCnt);
      }      
    }
    else if(dt == am550 && bufferResult[38] == 0x06) // parse Slovenia am550
    {  
      if(!deviceParameter[F("sendRawData")].isNull() && strcmp(deviceParameter[F("sendRawData")],"YES") == 0)
      {
        al = new SensorData(11);
        al->di[10].nameI = F("data");
        al->di[10].valueI = hexToString(readMessage, readCnt); 
      }
      else
        al = new SensorData(10);

      sprintf(meterTime, "%02d-%02d-%02dT%02d:%02d:%02d", (bufferResult[6] << 8) + (bufferResult[7]),bufferResult[8], bufferResult[9], bufferResult[11], bufferResult[12], bufferResult[13]);

      al->di[0].nameI = F("timestamp");
      al->di[0].valueI = String(meterTime); 

      al->di[1].nameI = F("value1");
      al->di[1].valueI = String(byteToUInt32(bufferResult, 39));         
      al->di[2].nameI = F("value2");
      al->di[2].valueI = String(byteToUInt32(bufferResult, 44));         
      al->di[3].nameI = F("value3");
      al->di[3].valueI = String(byteToUInt32(bufferResult, 49));         
      al->di[4].nameI = F("value4");
      al->di[4].valueI = String(byteToUInt32(bufferResult, 54));         
      al->di[5].nameI = F("value5");
      al->di[5].valueI = String(byteToUInt32(bufferResult, 59));         
      al->di[6].nameI = F("value6");
      al->di[6].valueI = String(byteToUInt32(bufferResult, 64));         
      al->di[7].nameI = F("value7");
      al->di[7].valueI = String(byteToUInt32(bufferResult, 69));         
      al->di[8].nameI = F("value8");
      al->di[8].valueI = String(byteToUInt32(bufferResult, 74));         

        
      timeToString(str, sizeof(str));
      al->di[9].nameI = F("uptime");
      al->di[9].valueI = String(str);          
    }
    else
    {
      if(!deviceParameter[F("sendRawData")].isNull() && strcmp(deviceParameter[F("sendRawData")],"YES") == 0)
      {
        al = new SensorData(3);
        al->di[2].nameI = F("data");
        al->di[2].valueI = hexToString(readMessage, readCnt); 
      }
      else
        al = new SensorData(2);
      
      al->di[0].nameI = F("lasterror");    
      al->di[0].valueI = F("Invalid data");  

      timeToString(str, sizeof(str));
      al->di[1].nameI = F("uptime");
      al->di[1].valueI = String(str);          
    }            
        
    delete readMessage;

    return al;
  }
}


/////////////////////////////
uint32_t Device_IM350::writeHourValue(const char *value)
{
  char content[20];
  memset(content, 0, 20);
#ifdef LITTLEFS  
  File hourFile = LittleFS.open("/IM350_hour.txt", "r");
#else
  File hourFile = SPIFFS.open("/IM350_hour.txt", "r");
#endif
  Serial.println("file opened...");
  
  if (hourFile) 
  {
    for(int i=0;i<hourFile.size();i++) //Read upto complete file size
    {
      content[i] += (char)hourFile.read();
      if(i == 19)
      {
        hourFile.close();      
        return 0;
      }
    }  
  }
  
  hourFile.close();  

#ifdef LITTLEFS  
  LittleFS.remove("/IM350_hour.txt");
  hourFile = LittleFS.open("/IM350_hour.txt", "w");
#else
  SPIFFS.remove("/IM350_hour.txt");
  hourFile = SPIFFS.open("/IM350_hour.txt", "w");  
#endif
  
  if (hourFile) 
  {
    hourFile.write(value, strlen(value));
  }

  hourFile.close();  

  return atol(content);
}

uint32_t Device_IM350::writeDayValue(const char *value)
{
  char content[20];
  memset(content, 0, 20);
#ifdef LITTLEFS  
  File dayFile = LittleFS.open("/IM350_day.txt", "r");
#else
  File dayFile = SPIFFS.open("/IM350_day.txt", "r");
#endif
  Serial.println("file opened...");
  
  if (dayFile) 
  {
    for(int i=0;i<dayFile.size();i++) //Read upto complete file size
    {
      content[i] += (char)dayFile.read();
      if(i == 19)
      {
        dayFile.close();      
        return 0;
      }
    }  
  }
  
  dayFile.close();  

#ifdef LITTLEFS  
  LittleFS.remove("/IM350_day.txt");
  dayFile = LittleFS.open("/IM350_day.txt", "w");
#else
  SPIFFS.remove("/IM350_day.txt");
  dayFile = SPIFFS.open("/IM350_day.txt", "w");  
#endif
  
  if (dayFile) 
  {
    dayFile.write(value, strlen(value));
  }

  dayFile.close();  

  return atol(content);
}

time_t Device_IM350::tmConvert_t(int YYYY, byte MM, byte DD, byte hh, byte mm, byte ss)
{
/*  tmElements_t tmSet;
  tmSet.Year = YYYY - 1970;
  tmSet.Month = MM;
  tmSet.Day = DD;
  tmSet.Hour = hh;
  tmSet.Minute = mm;
  tmSet.Second = ss;
  return makeTime(tmSet); */

  return NULL;
}

void Device_IM350::timeToString(char* string, size_t size)
{
  unsigned long nowMillis = millis();
  unsigned long seconds = nowMillis / 1000;
  int days = seconds / 86400;
  seconds %= 86400;
  byte hours = seconds / 3600;
  seconds %= 3600;
  byte minutes = seconds / 60;
  seconds %= 60;
  snprintf(string, size, "%04d:%02d:%02d:%02d", days, hours, minutes, seconds);
}

String Device_IM350::hexToString(byte array[], int readCnt)
{
  String data;
  char hexCode[3];
  hexCode[2] = 0;
    
  for(int i = 0; i<readCnt; i++)
  {
    sprintf(hexCode, "%02X", array[i]);
    data += String(hexCode);    
  }  

  return data;
}

void Device_IM350::hexToBytes(const char* code, byte* result)
{
  if(code != NULL)
  {
    String bb(code);
    char hexCode[2];
    
    bb.replace( " ", "" );
    
    for(int i = 0; i<bb.length() / 2; i++)
    {
      result[i] = strtoul(bb.substring(i*2, i*2+2).c_str(), NULL, 16);
    }   
  } 
}

uint32_t Device_IM350::byteToUInt32(byte array[], unsigned int startByte)
{
    uint32_t result;
    result = (uint32_t) array[startByte] << 24;
    result |=  (uint32_t) array[startByte+1] << 16;
    result |= (uint32_t) array[startByte+2] << 8;
    result |= (uint32_t) array[startByte+3];

    return result;
}

void Device_IM350::parse_message(byte array[], devicetype dt) 
{  
  int startPos = 0;

  if(dt == im350 || dt == am550)
    startPos = 57;  
  else if(dt == im350Wels)
    startPos = 52;
  
  sprintf(meterTime, "%02d-%02d-%02dT%02d:%02d:%02d", (array[6] << 8) + (array[7]),array[8], array[9], array[11], array[12], array[13]);
  Serial.printf("Timestamp = %s\n", meterTime);
    
  counter_reading_p_in = byteToUInt32(array, startPos);
  counter_reading_p_out = byteToUInt32(array, startPos+5);
  counter_reading_q_in = byteToUInt32(array, startPos+10);
  counter_reading_q_out = byteToUInt32(array, startPos+15);
  current_power_usage_in = byteToUInt32(array, startPos+20);
  current_power_usage_out = byteToUInt32(array, startPos+25);
}

void Device_IM350::decrypt_text(Vector_GCM *vect, byte *bufferResult)
{
  gcmaes128 = new GCM<AES128>();
  gcmaes128->setKey(vect->key, gcmaes128->keySize());
  gcmaes128->setIV(vect->iv, vect->ivsize);
  gcmaes128->decrypt((byte*)bufferResult, (byte*)vect->ciphertextPos, vect->datasize);
  delete gcmaes128;

  Serial.println(hexToString(bufferResult, vect->datasize));
}

void Device_IM350::init_vector(Vector_GCM *vect, byte *key_SM, byte *readMessage, devicetype dt) 
{
  int inaddi = 0;
  int iv1start = 0;
  int iv2start = 0;  
  byte tag[] = {0,0,0,0,0,0,0,0,0,0,0,0}; 

  for (int i = 0; i < 12; i++) 
  {
    vect->tag[i] = tag[i];
  }  
  
  if(dt == im350)
  {
    inaddi = 30;
    vect->datasize = 90;
    iv1start = 16;
    iv2start = 18;  
  }
  else if(dt == am550)
  {
    inaddi = 28;
    vect->datasize = 90;
    iv1start = 14;
    iv2start = 16;  
  }
  else if(dt == im350Wels)
  {
    inaddi = 30;
    vect->datasize = 81;
    iv1start = 16;
    iv2start = 18;  
  }
  else if(dt == sagemcom)
  {
    inaddi = 18;
    vect->datasize = 481;
    iv1start = 2;
    iv2start = 6;  
  }
  
  vect->name = "Smartmeter";  // vector name
  for (unsigned int i = 0; i < 16; i++) 
  {
    vect->key[i] = key_SM[i];
  }

  vect->ciphertextPos = readMessage+inaddi;

  for (int i = 0; i < 8; i++) 
  {
     vect->iv[i] = readMessage[iv1start+i]; // manufacturer + serialnumber 8 bytes
  }
  for (int i = 8; i < 12; i++) 
  {
     vect->iv[i] = readMessage[iv2start+i]; // frame counter
  }
    
  vect->authsize = 16;
  vect->tagsize = 12;
  vect->ivsize  = 12;  
}
